beagleboard/beaglebone-ai/regulatory/FCC_ID/CTL1906244051-WF02 FCC 15.247  BT4.0.pdf

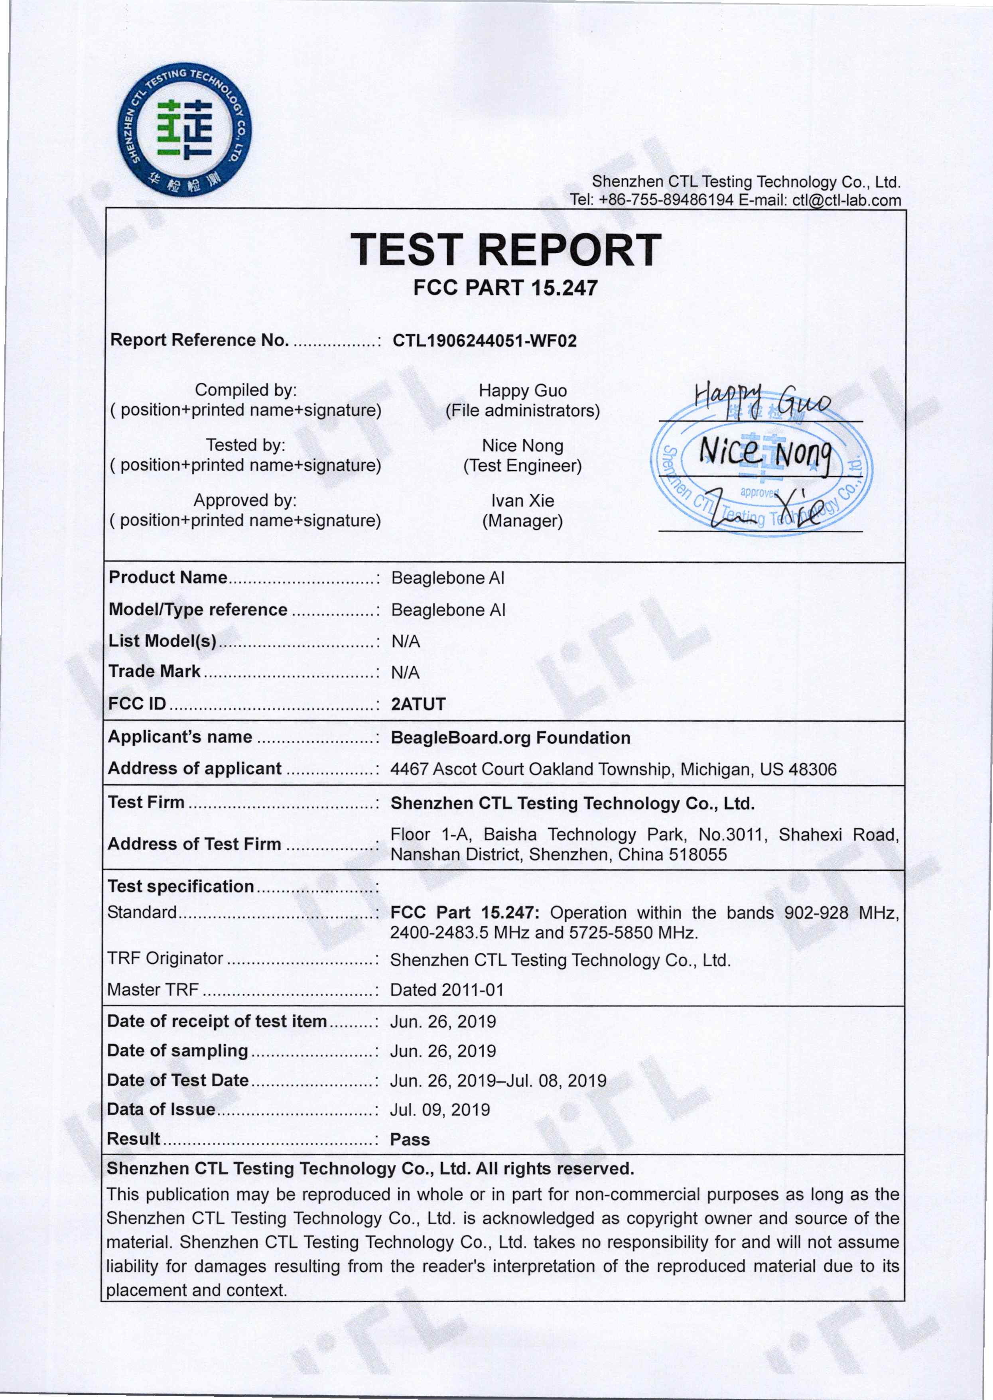
[picture p64: page 1]

V1.0 | Page 2 of 30 | Report No.: CTL1906244051-WF02

# TEST REPORT

Test Report No. : | CTL1906244051-WF02 | Jul. 09, 2019
Date of issue
Equipment under Test | : | Beaglebone AI
Model /Type | : | Beaglebone AI
Listed Models | : | N/A
Applicant | : | BeagleBoard.org Foundation
Address | : | 4467 Ascot Court Oakland Township, Michigan, US
48306
Manufacturer | : | BeagleBoard.org Foundation
Address | : | 4467 Ascot Court Oakland Township, Michigan, US
48306
Test result | Pass *

* In the configuration tested, the EUT complied with the standards specified page 5.
The test results presented in this report relate only to the object tested.
This report shall not be reproduced, except in full, without the written approval of the issuing testing laboratory.

V1.0 | Page 3 of 30 | Report No.: CTL1906244051-WF02

### ** Modified History **

Revisions | Description | Issued Data | Report No. | Remark
Version 1.0 | Initial Test Report Release | 2019-07-09 | CTL1906244051-WF02 | Tracy Qi

V1.0 | Page 4 of 30 | Report No.: CTL1906244051-WF02
| Table of Contents | Page

V1.0 | Page 5 of 30 | Report No.: CTL1906244051-WF02

## 1. SUMMARY

### 1.1. TEST STANDARDS

The tests were performed according to following standards:
FCC Rules Part 15.247: Frequency Hopping, Direct Spread Spectrum and Hybrid Systems that are in operation within the bands of 902-928 MHz, 2400-2483.5 MHz, and 5725-5850 MHz
ANSI C63.10: 2013: American National Standard for Testing Unlicensed Wireless Devices
KDB558074 D01 15.247 Meas Guidance v05r02: Guidance for Performing Compliance Measurements on Digital Transmission Systems (DTS) Operating Under §15.247

### 1.2. Test Description

FCC PART 15.247
FCC Part 15.207 | AC Power Conducted Emission | N/A
FCC Part 15.247(a)(2) | 6dB Bandwidth | PASS
FCC Part 15.247(d) | Spurious RF Conducted Emission | PASS
FCC Part 15.247(b) | Maximum Conducted Output Power | PASS
FCC Part 15.247(e) | Power Spectral Density | PASS
FCC Part 15.109/ 15.205/ 15.209 | Radiated Emissions | PASS
FCC Part 15.247(d) | Band Edge | PASS
FCC Part 15.203/15.247 (b) | Antenna Requirement | PASS

V1.0 | Page 6 of 30 | Report No.: CTL1906244051-WF02

### 1.3. Test Facility

### 1.3.1 Address of the test laboratory

Shenzhen CTL Testing Technology Co., Ltd.
Floor 1-A, Baisha Technology Park, No. 3011, Shahexi Road, Nanshan, Shenzhen 518055 China

There is one 3m semi-anechoic chamber and two line conducted labs for final test. The Test Sites meet the requirements in documents ANSI C63.4 and CISPR 32/EN 55032 requirements.

### 1.3.2 Laboratory accreditation

The test facility is recognized, certified, or accredited by the following organizations:
CNAS-Lab Code: L7497
Shenzhen CTL Testing Technology Co., Ltd. has been assessed and proved to be in compliance with CNAS-CL01 Accreditation Criteria for Testing and Calibration Laboratories (identical to ISO/IEC 17025: 2005 General Requirements) for the Competence of Testing and Calibration Laboratories.
A2LA-Lab Cert. No. 4343.01
Shenzhen CTL Testing Technology Co., Ltd. EMC Laboratory has been accredited by A2LA for technical competence in the field of electrical testing, and proved to be in compliance with ISO/IEC 17025: 2005 General Requirements for the Competence of Testing and Calibration Laboratories and any additional program requirements in the identified field of testing.
IC Registration No.: 9518B
CAB identifier: CN0041
The 3m alternate test site of Shenzhen CTL Testing Technology Co., Ltd. EMC Laboratory has been registered by Innovation, Science and Economic Development Canada to test to Canadian radio equipment requirements with Registration No.: 9518B on Jan. 22, 2019.
FCC-Registration No.: 399832
Designation No.: CN1216
Shenzhen CTL Testing Technology Co., Ltd. EMC Laboratory has been registered and fully described in a report filed with the (FCC) Federal Communications Commission. The acceptance letter from the FCC is maintained in our files. Registration 399832, December 08, 2017.

### 1.4. Statement of the measurement uncertainty

The data and results referenced in this document are true and accurate. The reader is cautioned that there may be errors within the calibration limits of the equipment and facilities. The measurement uncertainty was calculated for all measurements listed in this test report acc. to CISPR 16 - 4 “Specification for radio disturbance and immunity measuring apparatus and methods – Part 4: Uncertainty in EMC Measurements“ and is documented in the Shenzhen CTL Testing Technology Co., Ltd. quality system acc. to DIN EN ISO/IEC 17025. Furthermore, component and process variability of devices similar to that tested may result in additional deviation. The manufacturer has the sole responsibility of continued compliance of the device.

Hereafter the best measurement capability for CTL laboratory is reported:
Test | Measurement Uncertainty | Notes
Transmitter power conducted | ±0.57 dB | (1)
Transmitter power Radiated | ±2.20 dB | (1)
Conducted spurious emission 9KHz-40 GHz | ±2.20 dB | (1)
Occupied Bandwidth | ±0.01ppm | (1)
Radiated Emission 30~1000MHz | ±4.10dB | (1)
Radiated Emission Above 1GHz | ±4.32dB | (1)

V1.0 | Page 7 of 30 | Report No.: CTL1906244051-WF02
Conducted Disturbance0.15~30MHz | ±3.20dB | (1)
(1) This uncertainty represents an expanded uncertainty expressed at approximately the 95% confidence level using a coverage factor of k=2.

V1.0 | Page 8 of 30 | Report No.: CTL1906244051-WF02

## 2. GENERAL INFORMATION

### 2.1. Environmental conditions

During the measurement the environmental conditions were within the listed ranges:
Normal Temperature: | 25°C
Relative Humidity: | 55 %
Air Pressure: | 101 kPa

### 2.2. General Description of EUT

Product Name: | Beaglebone AI
Model/Type reference: | Beaglebone AI
Power supply: | DC 5.0V
Bluetooth LE
Supported type: | Bluetooth low Energy
Modulation: | GFSK
Operation frequency: | 2402MHz to 2480MHz
Channel number: | 40
Channel separation: | 2 MHz
Antenna type: | Snap antenna
Antenna gain: | 1.5dBi
Note: For more details, please refer to the user’s manual of the EUT.

### 2.3. Description of Test Modes and Test Frequency

The Applicant provides communication tools software to control the EUT for staying in continuous transmitting (Duty Cycle more than 98%) and receiving mode for testing.
There are 39 channels provided to the EUT and Channel 00/19/39 were selected for BLE test.

Operation Frequency List：
Channel | Frequency (MHz)
00 2402
02 | 2404
03 | 2406 ... ...
19 | 2440 ... ...
37 | 2476
38 | 2478
39 2480
Note: The line display in grey were the channel selected for testing

V1.0 | Page 9 of 30 | Report No.: CTL1906244051-WF02

### 2.4. Equipments Used during the Test

Test Equipment | Manufacturer | Model No. | Serial No. | Calibration Date | Calibration Due Date
LISN | R&S | ENV216 | 3560.6550.1 2 | 2019/05/24 | 2020/05/23
LISN | R&S | ESH2-Z5 | 860014/010 | 2019/05/24 | 2020/05/23
Bilog Antenna | Sunol Sciences Corp. | JB1 | A061713 | 2019/05/24 | 2020/05/23
EMI Test Receiver | R&S | ESCI | 1166.5950.03 | 2019/05/24 | 2020/05/23
Spectrum Analyzer | Agilent | E4407B | MY41440676 | 2019/05/24 | 2020/05/23
Spectrum Analyzer | Agilent | N9020 | US46220290 | 2019/05/24 | 2020/05/23
Controller | EM Electronics | EM 1000 | 060859 | 2019/05/24 | 2020/05/23
Horn Antenna | Sunol Sciences Corp. | DRH-118 | A062013 | 2019/05/24 | 2020/05/23
Active Loop Antenna | Da Ze | ZN30900A | / | 2019/05/24 | 2020/05/23
Amplifier | Agilent | 8449B | 3008A02306 | 2019/05/24 | 2020/05/23
Amplifier | Agilent | 8447D | 2944A10176 | 2019/05/24 | 2020/05/23
Temperature/Humi dity Meter | Gangxing | CTH-608 | 02 | 2019/05/24 | 2020/05/23
High-Pass Filter | micro-tranics | HPM50108 | G174 | 2019/05/24 | 2020/05/23
High-Pass Filter | micro-tranics | HPM50111 | G142 | 2019/05/24 | 2020/05/23
Coaxial Cables | HUBER+SUHN ER | SUCOFLEX 104PEA-10M | 10m | 2019/05/24 | 2020/05/23
Coaxial Cables | HUBER+SUHN ER | SUCOFLEX 104PEA-3M | 3m | 2019/05/24 | 2020/05/23
Coaxial Cables | HUBER+SUHN ER | SUCOFLEX 104PEA-3M | 3m | 2019/05/24 | 2020/05/23
RF Cable | Megalon | RF-A303 | N/A | 2019/05/24 | 2020/05/23
Power Sensor | Agilent | U2021XA | MY5365004 | 2019/05/24 | 2020/05/23
Power Meter | Agilent | U2531A | TW53323507 | 2019/05/24 | 2020/05/23
The calibration interval was one year

### 2.5. Related Submittal(s) / Grant (s)

This submittal(s) (test report) is intended to comply with Section 15.247 of the FCC Part 15, Subpart C Rules.

### 2.6. Modifications

No modifications were implemented to meet testing criteria.

V1.0 | Page 10 of 30 | Report No.: CTL1906244051-WF02

## 3. TEST CONDITIONS AND RESULTS

### 3.1. Conducted Emissions Test

LIMIT
FCC CFR Title 47 Part 15 Subpart C Section 15.207
Frequency range (MHz) | Limit (dBuV)
Quasi-peak | Average
0.15-0.5 | 66 to 56* | 56 to 46*
0.5-5 | 56 | 46
5-30 | 60 | 50

* Decreases with the logarithm of the frequency.

TEST CONFIGURATION

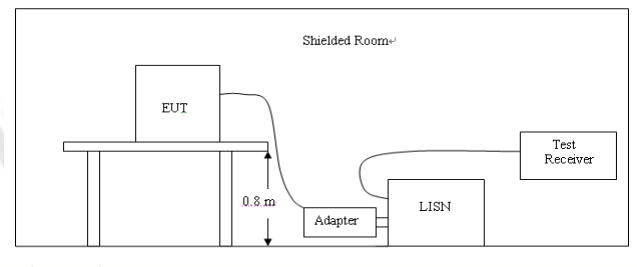
[picture p65: figure]

TEST PROCEDURE

1. The equipment was set up as per the test configuration to simulate typical actual usage per the user’s manual. The EUT is a tabletop system; a wooden table with a height of 0.8 meters is used and is placed on the ground plane as per ANSI C63.10:2013.
2. Support equipment, if needed, was placed as per ANSI C63.10:2013.
3. All I/O cables were positioned to simulate typical actual usage as per ANSI C63.10:2013.
4. The adapter received AC120V/60Hz power through a Line Impedance Stabilization Network (LISN) which supplied power source and was grounded to the ground plane.
5. All support equipments received AC power from a second LISN, if any.
6. The EUT test program was started. Emissions were measured on each current carrying line of the EUT using a spectrum Analyzer / Receiver connected to the LISN powering the EUT. The LISN has two monitoring points: Line 1 (Hot Side) and Line 2 (Neutral Side). Two scans were taken: one with Line 1 connected to Analyzer / Receiver and Line 2 connected to a 50 ohm load; the second scan had Line 1 connected to a 50 ohm load and Line 2 connected to the Analyzer / Receiver.
7. Analyzer / Receiver scanned from 150 KHz to 30MHz for emissions in each of the test modes.
8. During the above scans, the emissions were maximized by cable manipulation.

TEST RESULTS

Not applicable to this device, which is powered by battery.

V1.0 | Page 11 of 30 | Report No.: CTL1906244051-WF02

### 3.2. Radiated Emissions and Band Edge

Limit

For intentional device, according to § 15.209(a), the general requirement of field strength of radiated emission out of authorized band shall not exceed the following table at a 3 meters measurement distance.
In addition, radiated emissions which fall in the restricted bands, as defined in §15.205(a), must also comply with the radiated emission limits specified in §15.209(a)

Radiated emission limits
Frequency (MHz) | Distance (Meters) | Radiated (dBμV/m) | Radiated (μV/m)
0.009-0.49 | 3 | 20log(2400/F(KHz))+40log(300/3) | 2400/F(KHz)
0.49-1.705 | 3 | 20log(24000/F(KHz))+ 40log(30/3) | 24000/F(KHz)
1.705-30 | 3 | 20log(30)+ 40log(30/3) | 30
30-88 | 3 | 40.0 | 100
88-216 | 3 | 43.5 | 150
216-960 | 3 | 46.0 | 200
Above 960 | 3 | 54.0 | 500

TEST CONFIGURATION
(A) Radiated Emission Test Set-Up, Frequency Below 30MHz

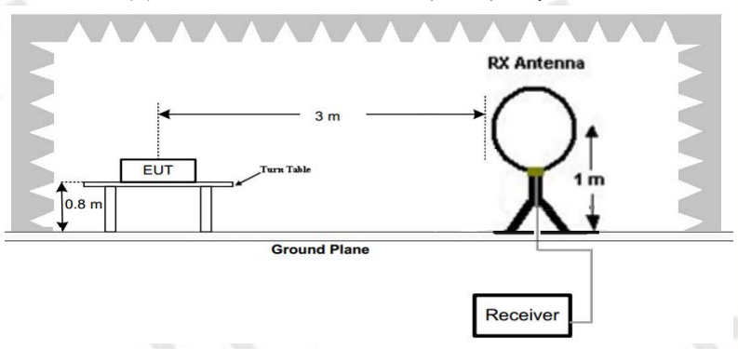
[picture p66: figure]

(B) Radiated Emission Test Set-Up, Frequency below 1000MHz

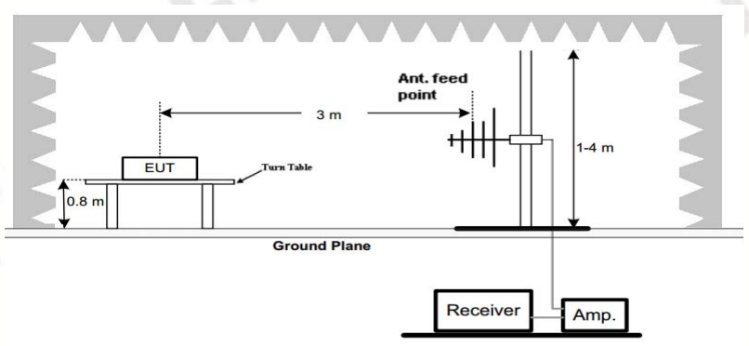
[picture p67: figure]

(C) Radiated Emission Test Set-Up, Frequency above 1000MHz

V1.0 | Page 12 of 30 | Report No.: CTL1906244051-WF02

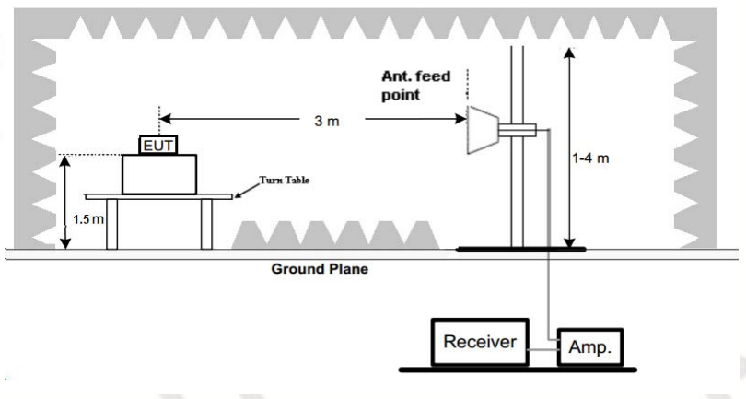
[picture p68: figure]

Test Procedure

1. Below 1GHz measurement the EUT is placed on a turntable which is 0.8m above ground plane, and above 1GHz measurement EUT was placed on a low permittivity and low loss tangent turn table which is 1.5m above ground plane.
2. Maximum procedure was performed by raising the receiving antenna from 1m to 4m and rotating the turn table from 0℃ to 360℃ to acquire the highest emissions from EUT
3. And also, each emission was to be maximized by changing the polarization of receiving antenna both horizontal and vertical.
4. Repeat above procedures until all frequency measurements have been completed.

TEST RESULTS
Remark:
1. For below 1GHz testing recorded worst at BLE low channel.
2. Radiated emission test from 9 KHz to 10th harmonic of fundamental was verified, and no emission found except system noise floor in 9 KHz to 30MHz and not recorded in this report.

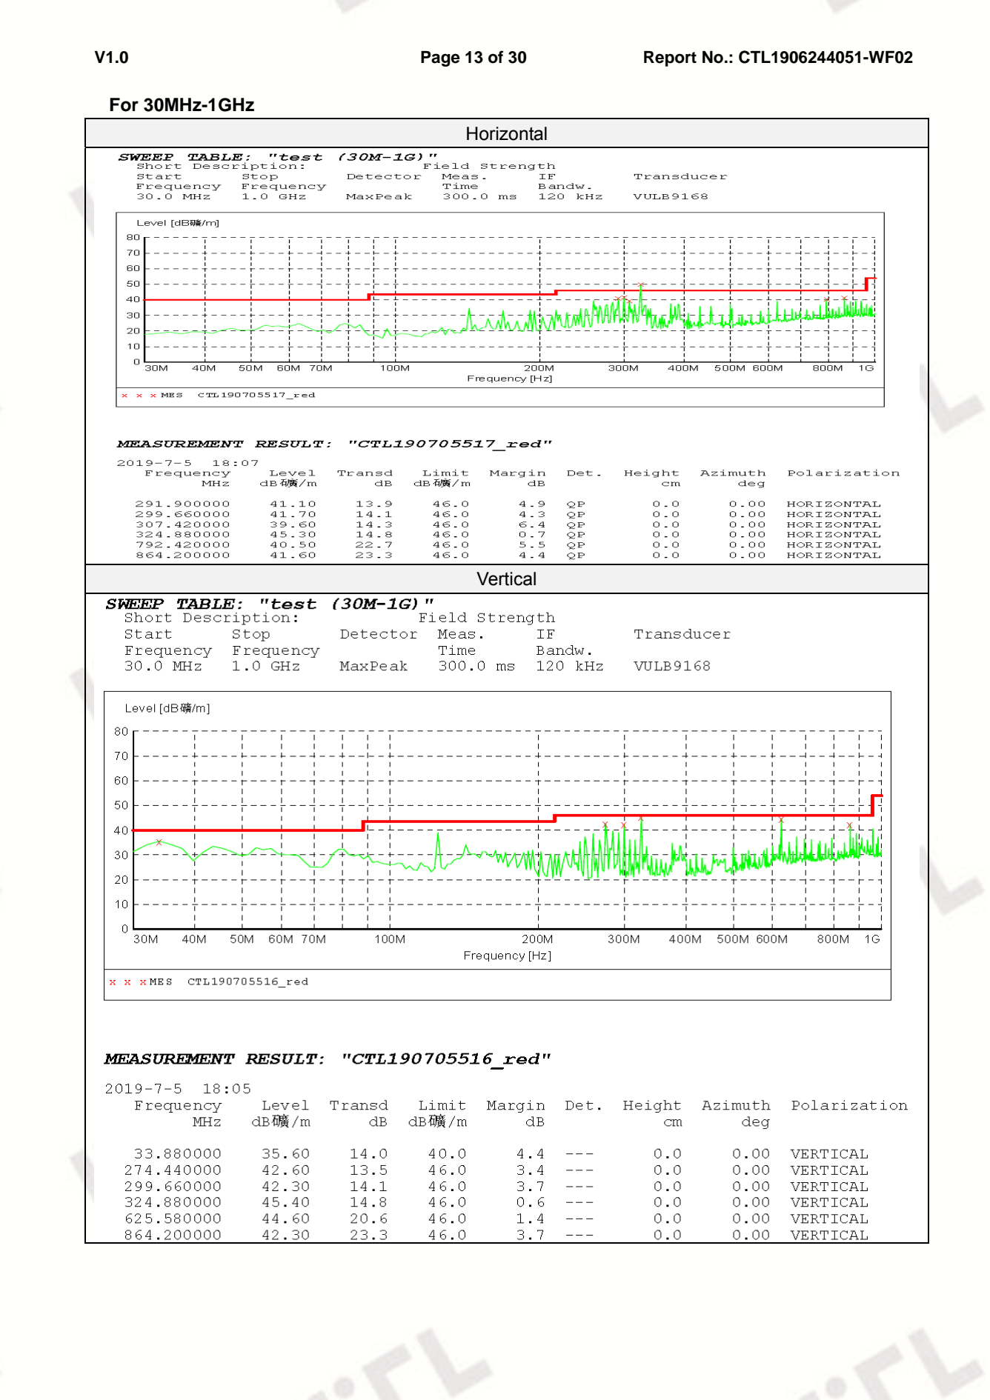
[picture p69: page 13]

V1.0 | Page 13 of 30 | Report No.: CTL1906244051-WF02

For 30MHz-1GHz
Horizontal

Vertical

V1.0 | Page 14 of 30 | Report No.: CTL1906244051-WF02

For 1GHz to 25GHz
BLE Mode (above 1GHz)
Frequency(MHz): | 2402 | Polarity: | HORIZONTAL
Frequency (MHz) | Emission Level (dBuV/m) | Limit (dBuV/m) | Margin (dB) | Raw Value (dBuV) | Antenna Factor (dB/m) | Cable Factor (dB) | Pre-amplifier (dB) | Correction Factor (dB/m)
4804.00 | 51.16 | PK | 74.00 | 22.84 | 46.65 | 33.49 | 6.91 | 35.89 | 4.51
4804.00 | -- | AV | 54.00 | -- | -- | -- | -- | -- | --
5120.05 | 46.15 | PK | 74.00 | 27.85 | 38.94 | 34.38 | 7.10 | 34.27 | 7.21
5120.05 | -- | AV | 54.00 | -- | -- | -- | -- | -- | --
7206.00 | 46.29 | PK | 74.00 | 27.71 | 35.19 | 36.95 | 9.18 | 35.03 | 11.10
7206.00 | -- | AV | 54.00 | -- | -- | -- | -- | -- | --
Frequency(MHz): | 2402 | Polarity: | VERTICAL
Frequency (MHz) | Emission Level (dBuV/m) | Limit (dBuV/m) | Margin (dB) | Raw Value (dBuV) | Antenna Factor (dB/m) | Cable Factor (dB) | Pre-amplifier (dB) | Correction Factor (dB/m)
4804.00 | 49.16 | PK | 74.00 | 24.84 | 44.65 | 33.49 | 6.91 | 35.89 | 4.51
4804.00 | -- | AV | 54.00 | -- | -- | -- | -- | -- | --
5120.05 | 47.01 | PK | 74.00 | 26.99 | 39.45 | 34.69 | 7.23 | 34.36 | 7.56
5120.05 | -- | AV | 54.00 | -- | -- | -- | -- | -- | --
7206.00 | 45.86 | PK | 74.00 | 28.14 | 34.76 | 36.95 | 9.18 | 35.03 | 11.10
7206.00 | -- | AV | 54.00 | -- | -- | -- | -- | -- | --
Frequency(MHz): | 2440 | Polarity: | HORIZONTAL
Frequency (MHz) | Emission Level (dBuV/m) | Limit (dBuV/m) | Margin (dB) | Raw Value (dBuV) | Antenna Factor (dB/m) | Cable Factor (dB) | Pre-amplifier (dB) | Correction Factor (dB/m)
4880.00 | 47.03 | PK | 74.00 | 26.97 | 40.78 | 33.60 | 6.95 | 34.30 | 6.25
4880.00 | -- | AV | 54.00 | -- | -- | -- | -- | -- | --
5235.15 | 43.86 | PK | 74.00 | 30.14 | 36.23 | 34.57 | 7.16 | 34.10 | 7.63
5235.15 | -- | AV | 54.00 | -- | -- | -- | -- | -- | --
7320.00 | 45.18 | PK | 74.00 | 28.82 | 33.49 | 37.46 | 9.23 | 35.00 | 11.69
7320.00 | -- | AV | 54.00 | -- | -- | -- | -- | -- | --
Frequency(MHz): | 2440 | Polarity: | VERTICAL
Frequency (MHz) | Emission Level (dBuV/m) | Limit (dBuV/m) | Margin (dB) | Raw Value (dBuV) | Antenna Factor (dB/m) | Cable Factor (dB) | Pre-amplifier (dB) | Correction Factor (dB/m)
4880.00 | 48.25 | PK | 74.00 | 25.75 | 42.00 | 33.60 | 6.95 | 34.30 | 6.25
4880.00 | -- | AV | 54.00 | -- | -- | -- | -- | -- | --
5235.15 | 42.58 | PK | 74.00 | 31.42 | 34.94 | 34.58 | 7.16 | 34.10 | 7.64
5235.15 | -- | AV | 54.00 | -- | -- | -- | -- | -- | --
7320.00 | 46.31 | PK | 74.00 | 27.69 | 34.62 | 37.46 | 9.23 | 35.00 | 11.69
7320.00 | -- | AV | 54.00 | -- | -- | -- | -- | -- | --

V1.0 | Page 15 of 30 | Report No.: CTL1906244051-WF02
Frequency(MHz): | 2480 | Polarity: | HORIZONTAL
Frequency (MHz) | Emission Level (dBuV/m) | Limit (dBuV/m) | Margin (dB) | Raw Value (dBuV) | Antenna Factor (dB/m) | Cable Factor (dB) | Pre-amplifier (dB) | Correction Factor (dB/m)
4960.00 | 48.69 | PK | 74.00 | 25.31 | 43.77 | 33.84 | 7.00 | 35.92 | 4.92
4960.00 | -- | AV | 54.00 | -- | -- | -- | -- | -- | --
5325.05 | 44.56 | PK | 74.00 | 29.44 | 37.02 | 34.67 | 7.22 | 34.35 | 7.54
5325.05 | -- | AV | 54.00 | -- | -- | -- | -- | -- | --
7440.00 | 45.83 | PK | 74.00 | 28.17 | 33.88 | 37.64 | 9.28 | 34.97 | 11.95
7440.00 | -- | AV | 54.00 | -- | -- | -- | -- | -- | --
Frequency(MHz): | 2480 | Polarity: | VERTICAL
Frequency (MHz) | Emission Level (dBuV/m) | Limit (dBuV/m) | Margin (dB) | Raw Value (dBuV) | Antenna Factor (dB/m) | Cable Factor (dB) | Pre-amplifier (dB) | Correction Factor (dB/m)
4960.00 | 47.68 | PK | 74.00 | 26.32 | 42.76 | 33.84 | 7.00 | 35.92 | 4.92
4960.00 | -- | AV | 54.00 | -- | -- | -- | -- | -- | --
5325.05 | 43.51 | PK | 74.00 | 30.49 | 36.32 | 34.36 | 7.10 | 34.27 | 7.19
5325.05 | -- | AV | 54.00 | -- | -- | -- | -- | -- | --
7440.00 | 44.32 | PK | 74.00 | 29.68 | 32.37 | 37.64 | 9.28 | 34.97 | 11.95
7440.00 | -- | AV | 54.00 | -- | -- | -- | -- | -- | --

REMARKS:
1. Emission level (dBuV/m) =Raw Value (dBuV)+Correction Factor (dB/m)
2. Correction Factor (dB/m) = Antenna Factor (dB/m)+Cable Factor (dB)-Pre-amplifier Factor
3. Margin value = Limit value- Emission level.
4. -- Mean the PK detector measured value is below average limit.
5. The other emission levels were very low against the limit.
6. RBW1MHz VBW3MHz Peak detector is for PK value; RBW 1MHz VBW10Hz Peak detector is for AV value.

V1.0 | Page 16 of 30 | Report No.: CTL1906244051-WF02

Results of Band Edges Test (Radiated)
Frequency(MHz): | 2402 | Polarity: | HORIZONTAL
Frequency (MHz) | Emission Level (dBuV/m) | Limit (dBuV/m) | Margin (dB) | Raw Value (dBuV) | Antenna Factor (dB/m) | Cable Factor (dB) | Pre-amplifier (dB) | Correction Factor (dB/m)
2402.00 | 94.93 | PK | -- | -- | 61.54 | 28.78 | 4.61 | 0.00 | 33.39
2402.00 | 90.48 | AV | -- | -- | 57.09 | 28.78 | 4.61 | 0.00 | 33.39
2357.75 | 44.81 | PK | 74.00 | 29.19 | 11.73 | 28.52 | 4.56 | 0.00 | 33.08
2357.75 | -- | AV | 54.00 | -- | -- | -- | -- | -- | --
2390.00 | 45.20 | PK | 74.00 | 28.80 | 11.88 | 28.72 | 4.60 | 0.00 | 33.32
2390.00 | -- | AV | 54.00 | -- | -- | -- | -- | -- | --
2400.00 | 47.85 | PK | 74.00 | 26.15 | 14.46 | 28.78 | 4.61 | 0.00 | 33.39
2400.00 | -- | AV | 54.00 | -- | -- | -- | -- | -- | --
Frequency(MHz): | 2402 | Polarity: | VERTICAL
Frequency (MHz) | Emission Level (dBuV/m) | Limit (dBuV/m) | Margin (dB) | Raw Value (dBuV) | Antenna Factor (dB/m) | Cable Factor (dB) | Pre-amplifier (dB) | Correction Factor (dB/m)
2402.00 | 94.71 | PK | -- | -- | 61.32 | 28.78 | 4.61 | 0 | 33.39
2402.00 | 89.22 | AV | -- | -- | 55.83 | 28.78 | 4.61 | 0 | 33.39
2357.75 | 45.07 | PK | 74 | 28.93 | 11.99 | 28.52 | 4.56 | 0 | 33.08
2357.75 | -- | AV | 54 | -- | -- | -- | -- | -- | --
2390.00 | 46.18 | PK | 74 | 27.82 | 12.86 | 28.72 | 4.60 | 0 | 33.32
2390.00 | -- | AV | 54 | -- | -- | -- | -- | -- | --
2400.00 | 48.26 | PK | 74 | 25.74 | 14.87 | 28.78 | 4.61 | 0 | 33.39
2400.00 | -- | AV | 54 | -- | -- | -- | -- | -- | --
Frequency(MHz): | 2480 | Polarity: | HORIZONTAL
Frequency (MHz) | Emission Level (dBuV/m) | Limit (dBuV/m) | Margin (dB) | Raw Value (dBuV) | Antenna Factor (dB/m) | Cable Factor (dB) | Pre-amplifier (dB) | Correction Factor (dB/m)
2480.00 | 95.11 | PK | -- | -- | 61.49 | 28.92 | 4.70 | 0.00 | 33.62
2480.00 | 90.35 | AV | -- | -- | 56.73 | 28.92 | 4.70 | 0.00 | 33.62
2483.50 | 43.12 | PK | 74 | 30.88 | 9.49 | 28.93 | 4.70 | 0.00 | 33.63
2483.50 | -- | AV | 54 | -- | -- | -- | -- | -- | --
2491.95 | 43.26 | PK | 74 | 30.74 | 9.6 | 28.95 | 4.71 | 0.00 | 33.66
2491.95 | -- | AV | 54 | -- | -- | -- | -- | -- | --
2500.00 | 47.42 | PK | 74 | 26.58 | 13.74 | 28.96 | 4.72 | 0.00 | 33.68
2500.00 | -- | AV | 54 | -- | -- | -- | -- | -- | --
Frequency(MHz): | 2480 | Polarity: | VERTICAL
Frequency (MHz) | Emission Level (dBuV/m) | Limit (dBuV/m) | Margin (dB) | Raw Value (dBuV) | Antenna Factor (dB/m) | Cable Factor (dB) | Pre-amplifier (dB) | Correction Factor (dB/m)
2480.00 | 93.87 | PK | -- | -- | 60.25 | 28.92 | 4.70 | 0.00 | 33.62
2480.00 | 89.04 | AV | -- | -- | 55.42 | 28.92 | 4.70 | 0.00 | 33.62
2483.50 | 43.06 | PK | 74 | 30.94 | 9.43 | 28.93 | 4.70 | 0.00 | 33.63
2483.50 | -- | AV | 54 | -- | -- | -- | -- | -- | --
2489.05 | 42.71 | PK | 74 | 31.29 | 9.05 | 28.95 | 4.71 | 0.00 | 33.66
2489.05 | -- | AV | 54 | -- | -- | -- | -- | -- | --
2500.00 | 45.25 | PK | 74 | 28.75 | 11.57 | 28.96 | 4.72 | 0.00 | 33.68
2500.00 | -- | AV | 54 | -- | -- | -- | -- | -- | --

V1.0 | Page 17 of 30 | Report No.: CTL1906244051-WF02

REMARKS:
1. Emission level (dBuV/m) =Raw Value (dBuV)+Correction Factor (dB/m)
2. Correction Factor (dB/m) = Antenna Factor (dB/m)+Cable Factor (dB)-Pre-amplifier Factor
3. Margin value = Limit value- Emission level.
4. -- Mean the PK detector measured value is below average limit.
5. The other emission levels were very low against the limit.
6. RBW1MHz VBW3MHz Peak detector is for PK value; RBW 1MHz VBW10Hz Peak detector is for AV value.
7. For fundamental frequency, RBW 3MHz VBW 3MHz Peak detector is for PK Value; RMS detector is for AV value.

V1.0 | Page 18 of 30 | Report No.: CTL1906244051-WF02

### 3.3. Maximum Conducted Output Power

Limit

The Maximum Peak Output Power Measurement is 30dBm.

Test Procedure

Remove the antenna from the EUT and then connect a low loss RF cable from the antenna port to the power sensor.

Test Configuration

EUT

| Power Sensor | Power Meter

Test Results

Type | Channel | Output power (dBm) | Limit (dBm) | Result
GFSK | 00 | 1.562 | 30.00 | Pass
| 19 | 2.191
| 39 | 0.833
Note: 1.The test results including the cable lose.

V1.0 | Page 19 of 30 | Report No.: CTL1906244051-WF02

### 3.4. Power Spectral Density

Limit

For digitally modulated systems, the power spectral density conducted from the intentional radiator to the antenna shall not be greater than 8 dBm in any 3 kHz band during any time interval of continuous transmission.
Test Procedure
1. Use this procedure when the maximum peak conducted output power in the fundamental emission is used to demonstrate compliance.
2. Set the RBW ≥ 3 kHz.
3. Set the VBW ≥ 3× RBW.
4. Set the span to 1.5 times the DTS channel bandwidth.
5. Detector = peak.
6. Sweep time = auto couple.
7. Trace mode = max hold.
8. Allow trace to fully stabilize.
9. Use the peak marker function to determine the maximum power level.
10. If measured value exceeds limit, reduce RBW (no less than 3 kHz) and repeat.
11. The resulting peak PSD level must be 8dBm.
Test Configuration

EUT

SPECTRUM
ANALYZER

Test Results

Type | Channel | Power Spectral Density (dBm/3KHz) | Limit (dBm/3KHz) | Result
GFSK | 00 | -12.853 | 8.00 | Pass
| 19 | -12.157
| 39 | -13.513

Test plot as follows:

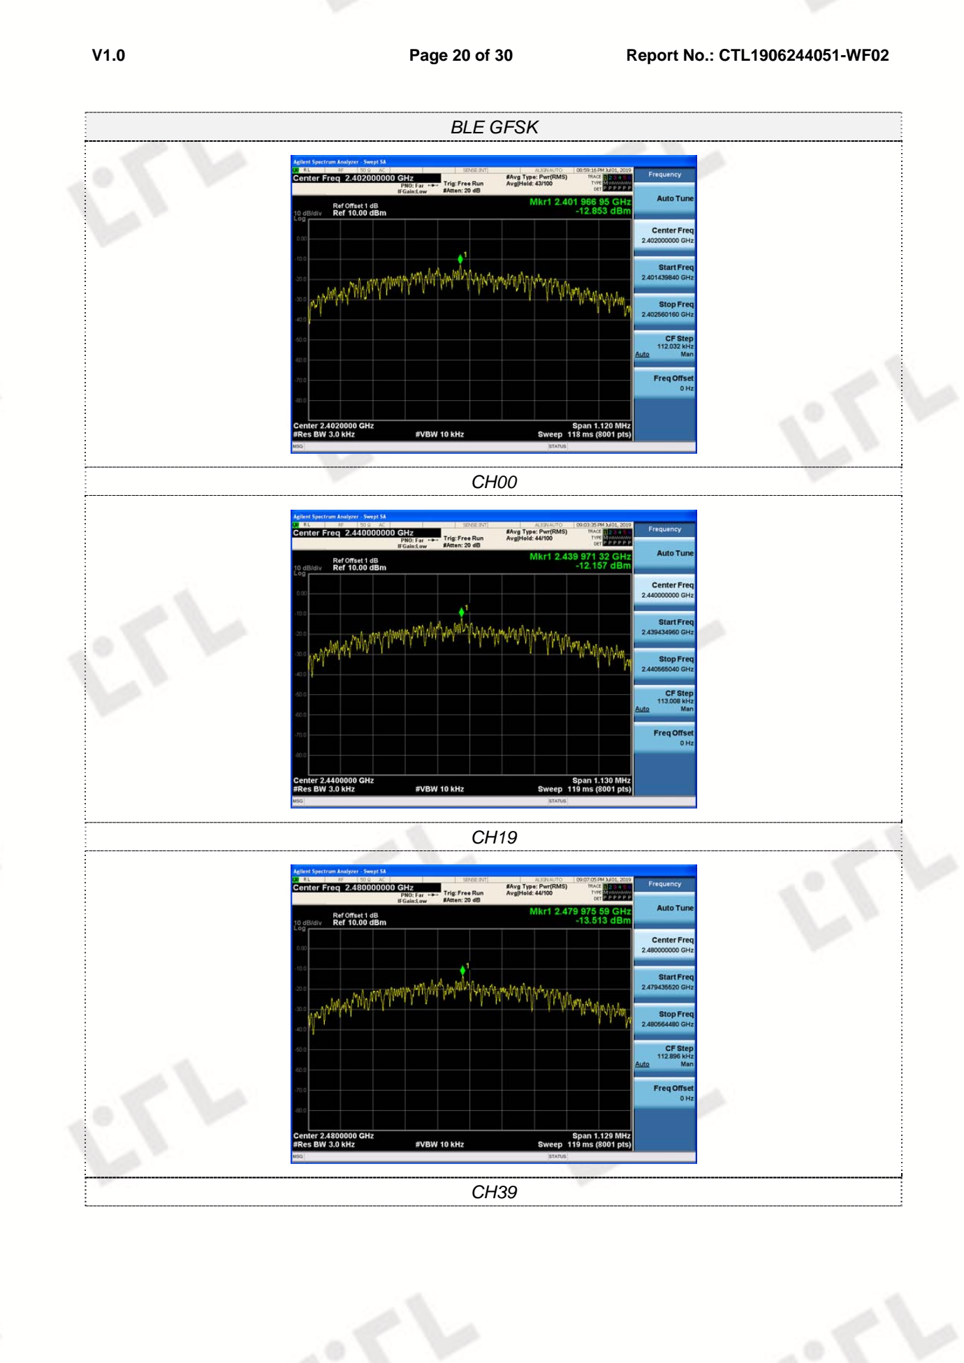
[picture p70: page 20]

V1.0 | Page 20 of 30 | Report No.: CTL1906244051-WF02

BLE GFSK

CH00

CH19

CH39

V1.0 | Page 21 of 30 | Report No.: CTL1906244051-WF02

### 3.5. 6dB Bandwidth

Limit

For digital modulation systems, the minimum 6 dB bandwidth shall be at least 500 kHz

Test Procedure

The transmitter output was connected to the spectrum analyzer through an attenuator. The bandwidth of the fundamental frequency was measured by spectrum analyzer with 100 KHz RBW and 300 KHz VBW. The 6dB bandwidth is defined as the total spectrum the power of which is higher than peak power minus 6dB.

Test Configuration

EUT

SPECTRUM
ANALYZER

Test Results

Type | Channel | 6dB Bandwidth (MHz) | 99% OBW (MHz) | Limit (KHz) | Result
GFSK | 00 | 0.7002 | 1.0842 | ≥500 | Pass
| 19 | 0.7063 | 1.0866
| 39 | 0.7056 | 1.0842

Test plot as follows:

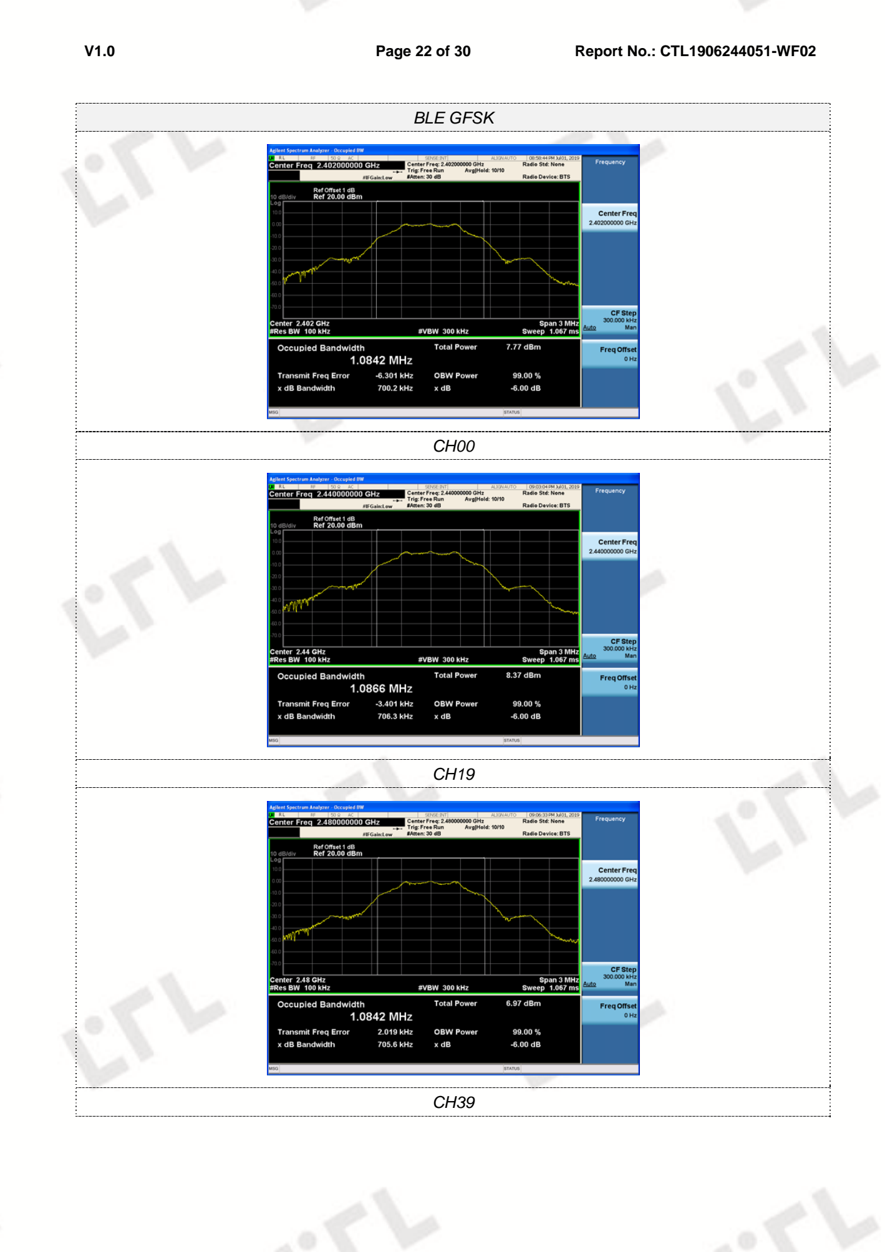
[picture p71: page 22]

V1.0 | Page 22 of 30 | Report No.: CTL1906244051-WF02

BLE GFSK

CH00

CH19

CH39

V1.0 | Page 23 of 30 | Report No.: CTL1906244051-WF02

### 3.6. Out-of-band Emissions

Limit
In any 100 kHz bandwidth outside the frequency band in which the spread spectrum or digitally modulated intentional radiator is operating, the radio frequency power that is produced by the intentional radiator shall be at least 20 dB below that in the 100 kHz bandwidth within the band that contains the highest level of the desired power, based on either an RF con-ducted or a radiated measurement, pro-vided the transmitter demonstrates compliance with the peak conducted power limits. If the transmitter com-plies with the conducted power limits based on the use of RMS averaging over a time interval, as permitted under paragraph (b)(3) of this section, the attenuation required under this paragraph shall be 30 dB instead of 20 dB. Attenuation below the general limits specified in §15.209(a) is not required.

Test Procedure

Connect the transmitter output to spectrum analyzer using a low loss RF cable, and set the spectrum analyzer to RBW=100 kHz, VBW= 300 kHz, peak detector , and max hold. Measurements utilizing these setting are made of the in-band reference level, bandedge and out-of-band emissions.

Test Configuration

EUT

SPECTRUM
ANALYZER

Test Results

Remark: The measurement frequency range is from 30MHz to the 10th harmonic of the fundamental frequency. The lowest, middle and highest channels are tested to verify the spurious emissions and bandage measurement data.

Test plot as follows:

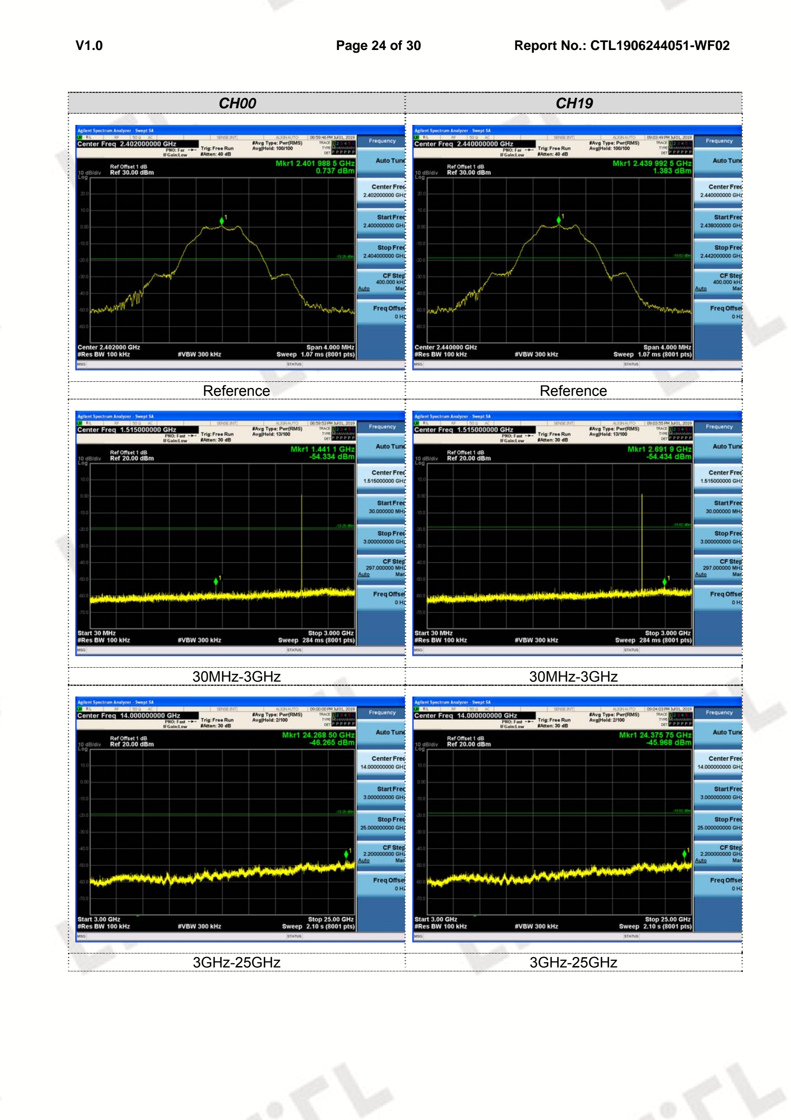
[picture p72: page 24]

V1.0 | Page 24 of 30 | Report No.: CTL1906244051-WF02
CH00 | CH19
Reference | Reference
30MHz-3GHz | 30MHz-3GHz
3GHz-25GHz | 3GHz-25GHz

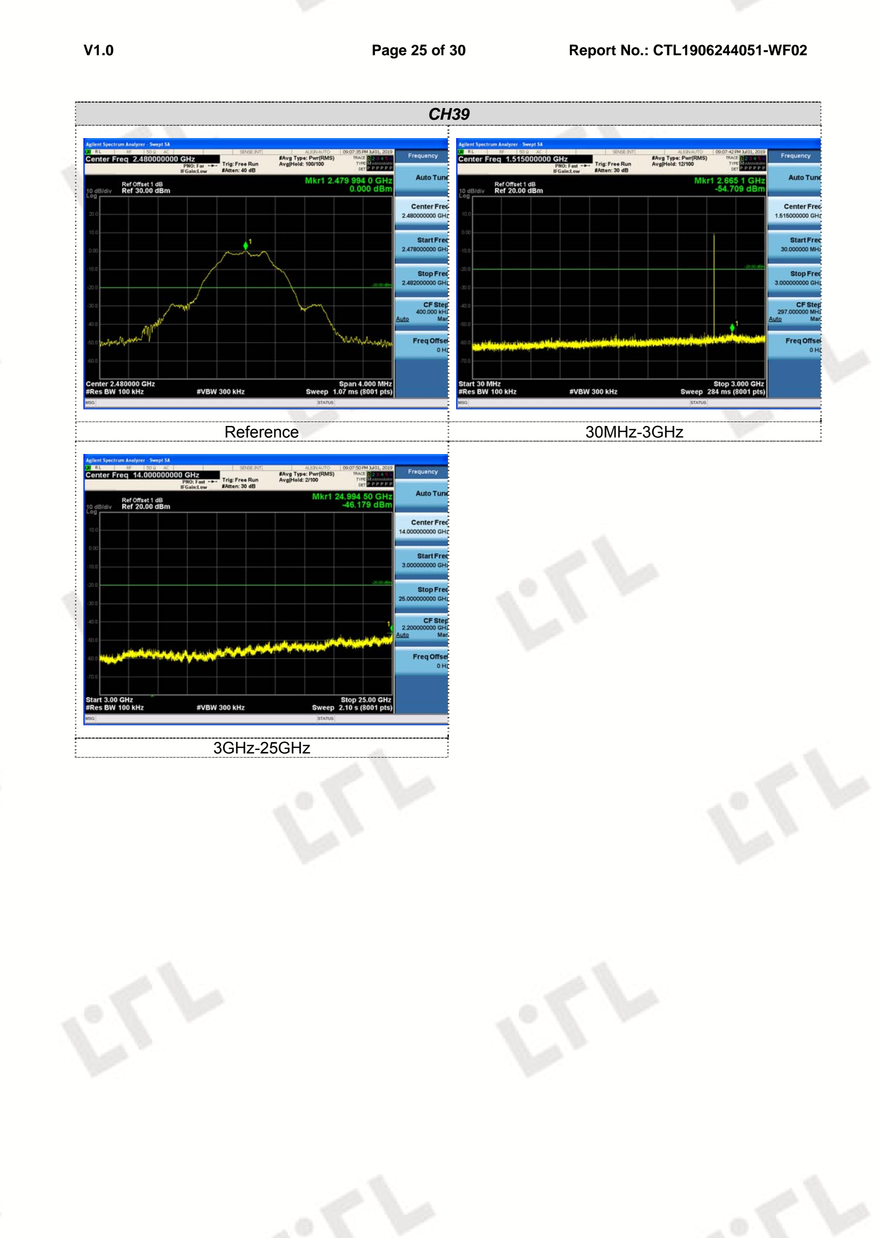
[picture p73: page 25]

V1.0 | Page 25 of 30 | Report No.: CTL1906244051-WF02

CH39

Reference | 30MHz-3GHz

3GHz-25GHz

V1.0 | Page 26 of 30 | Report No.: CTL1906244051-WF02

Band-edge Measurements for RF Conducted Emissions:

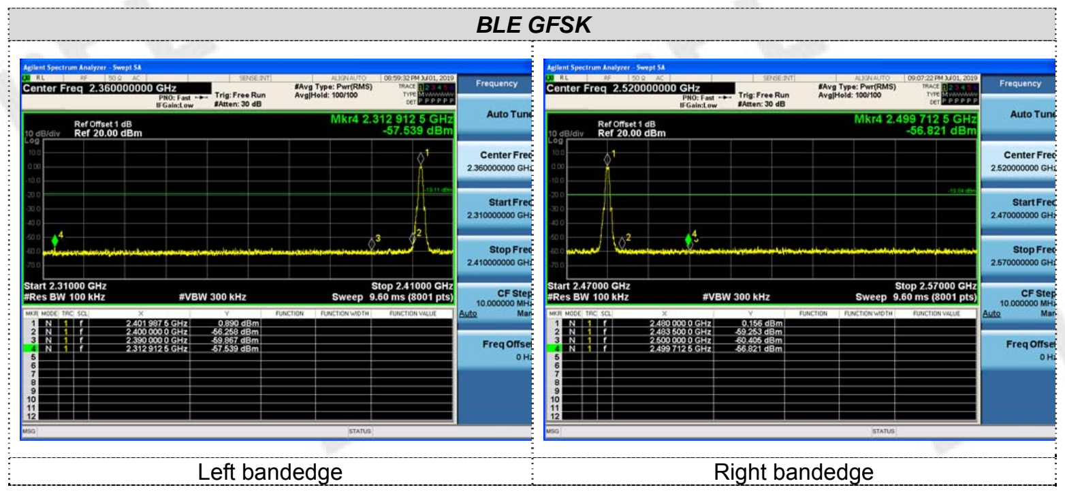
[picture p74: figure]
BLE GFSK; Left bandedge; Right bandedge

V1.0 | Page 27 of 30 | Report No.: CTL1906244051-WF02

### 3.7. Antenna Requirement

Standard Applicable

For intentional device, according to FCC 47 CFR Section 15.203:

An intentional radiator shall be designed to ensure that no antenna other than that furnished by the responsible party shall be used with the device. The use of a permanently attached antenna or of an antenna that uses a unique coupling to the intentional radiator, the manufacturer may design the unit so that a broken antenna can be replaced by the user, but the use of a standard antenna jack or electrical connector is prohibited

FCC CFR Title 47 Part 15 Subpart C Section 15.247(c) (1) (I):

(i) Systems operating in the 2400-2483.5 MHz band that is used exclusively for fixed. Point-to-point operations may employ transmitting antennas with directional gain greater than 6dBi provided the maximum conducted output power of the intentional radiator is reduced by 1 dB for every 3 dB that the directional gain of the antenna exceeds 6dBi.

Test Result:
The maximum gain of antenna was 1.5dBi.

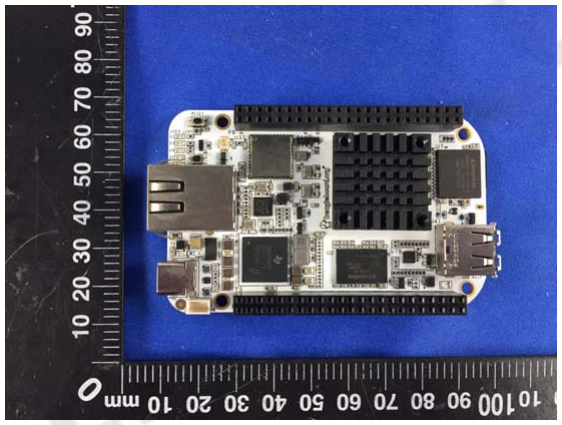
[picture p75: figure]

## 4. Test Setup Photos of the EUT

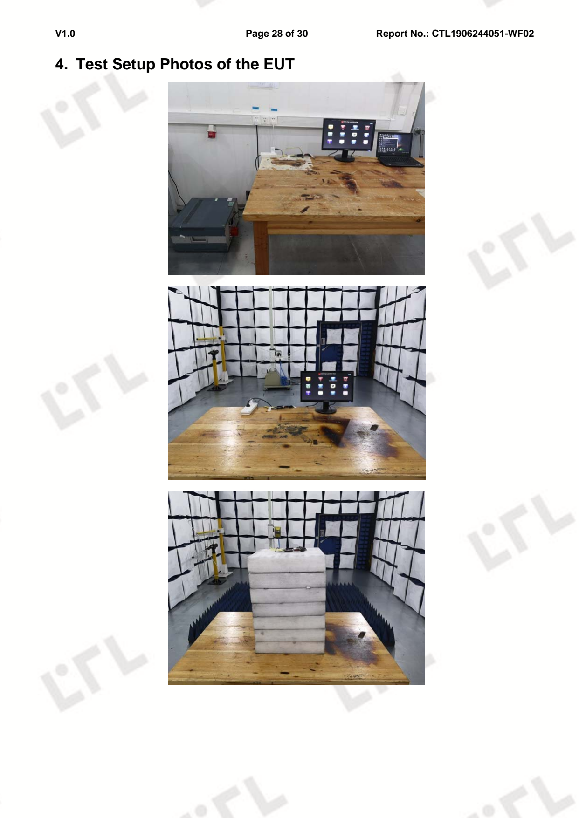
[picture p76: page 28]

V1.0 | Page 28 of 30 | Report No.: CTL1906244051-WF02

## 5. Photos of the EUT

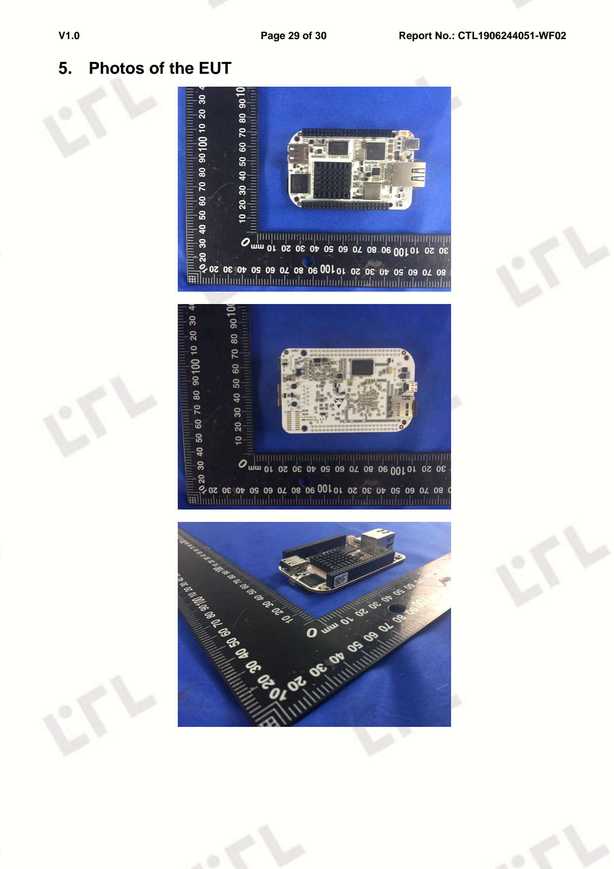
[picture p77: page 29]

V1.0 | Page 29 of 30 | Report No.: CTL1906244051-WF02

V1.0 | Page 30 of 30 | Report No.: CTL1906244051-WF02

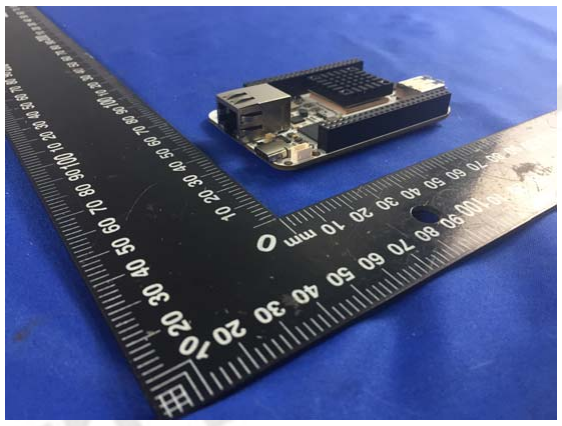
[picture p78: figure]

********************** End of Report **********************
