beagleboard/beaglebone-ai/kicad/beaglebone-ai-rev-a1/adc.kicad_sch

## KiCad design kicad/beaglebone-ai-rev-a1/adc.kicad_sch (2021-06-15)

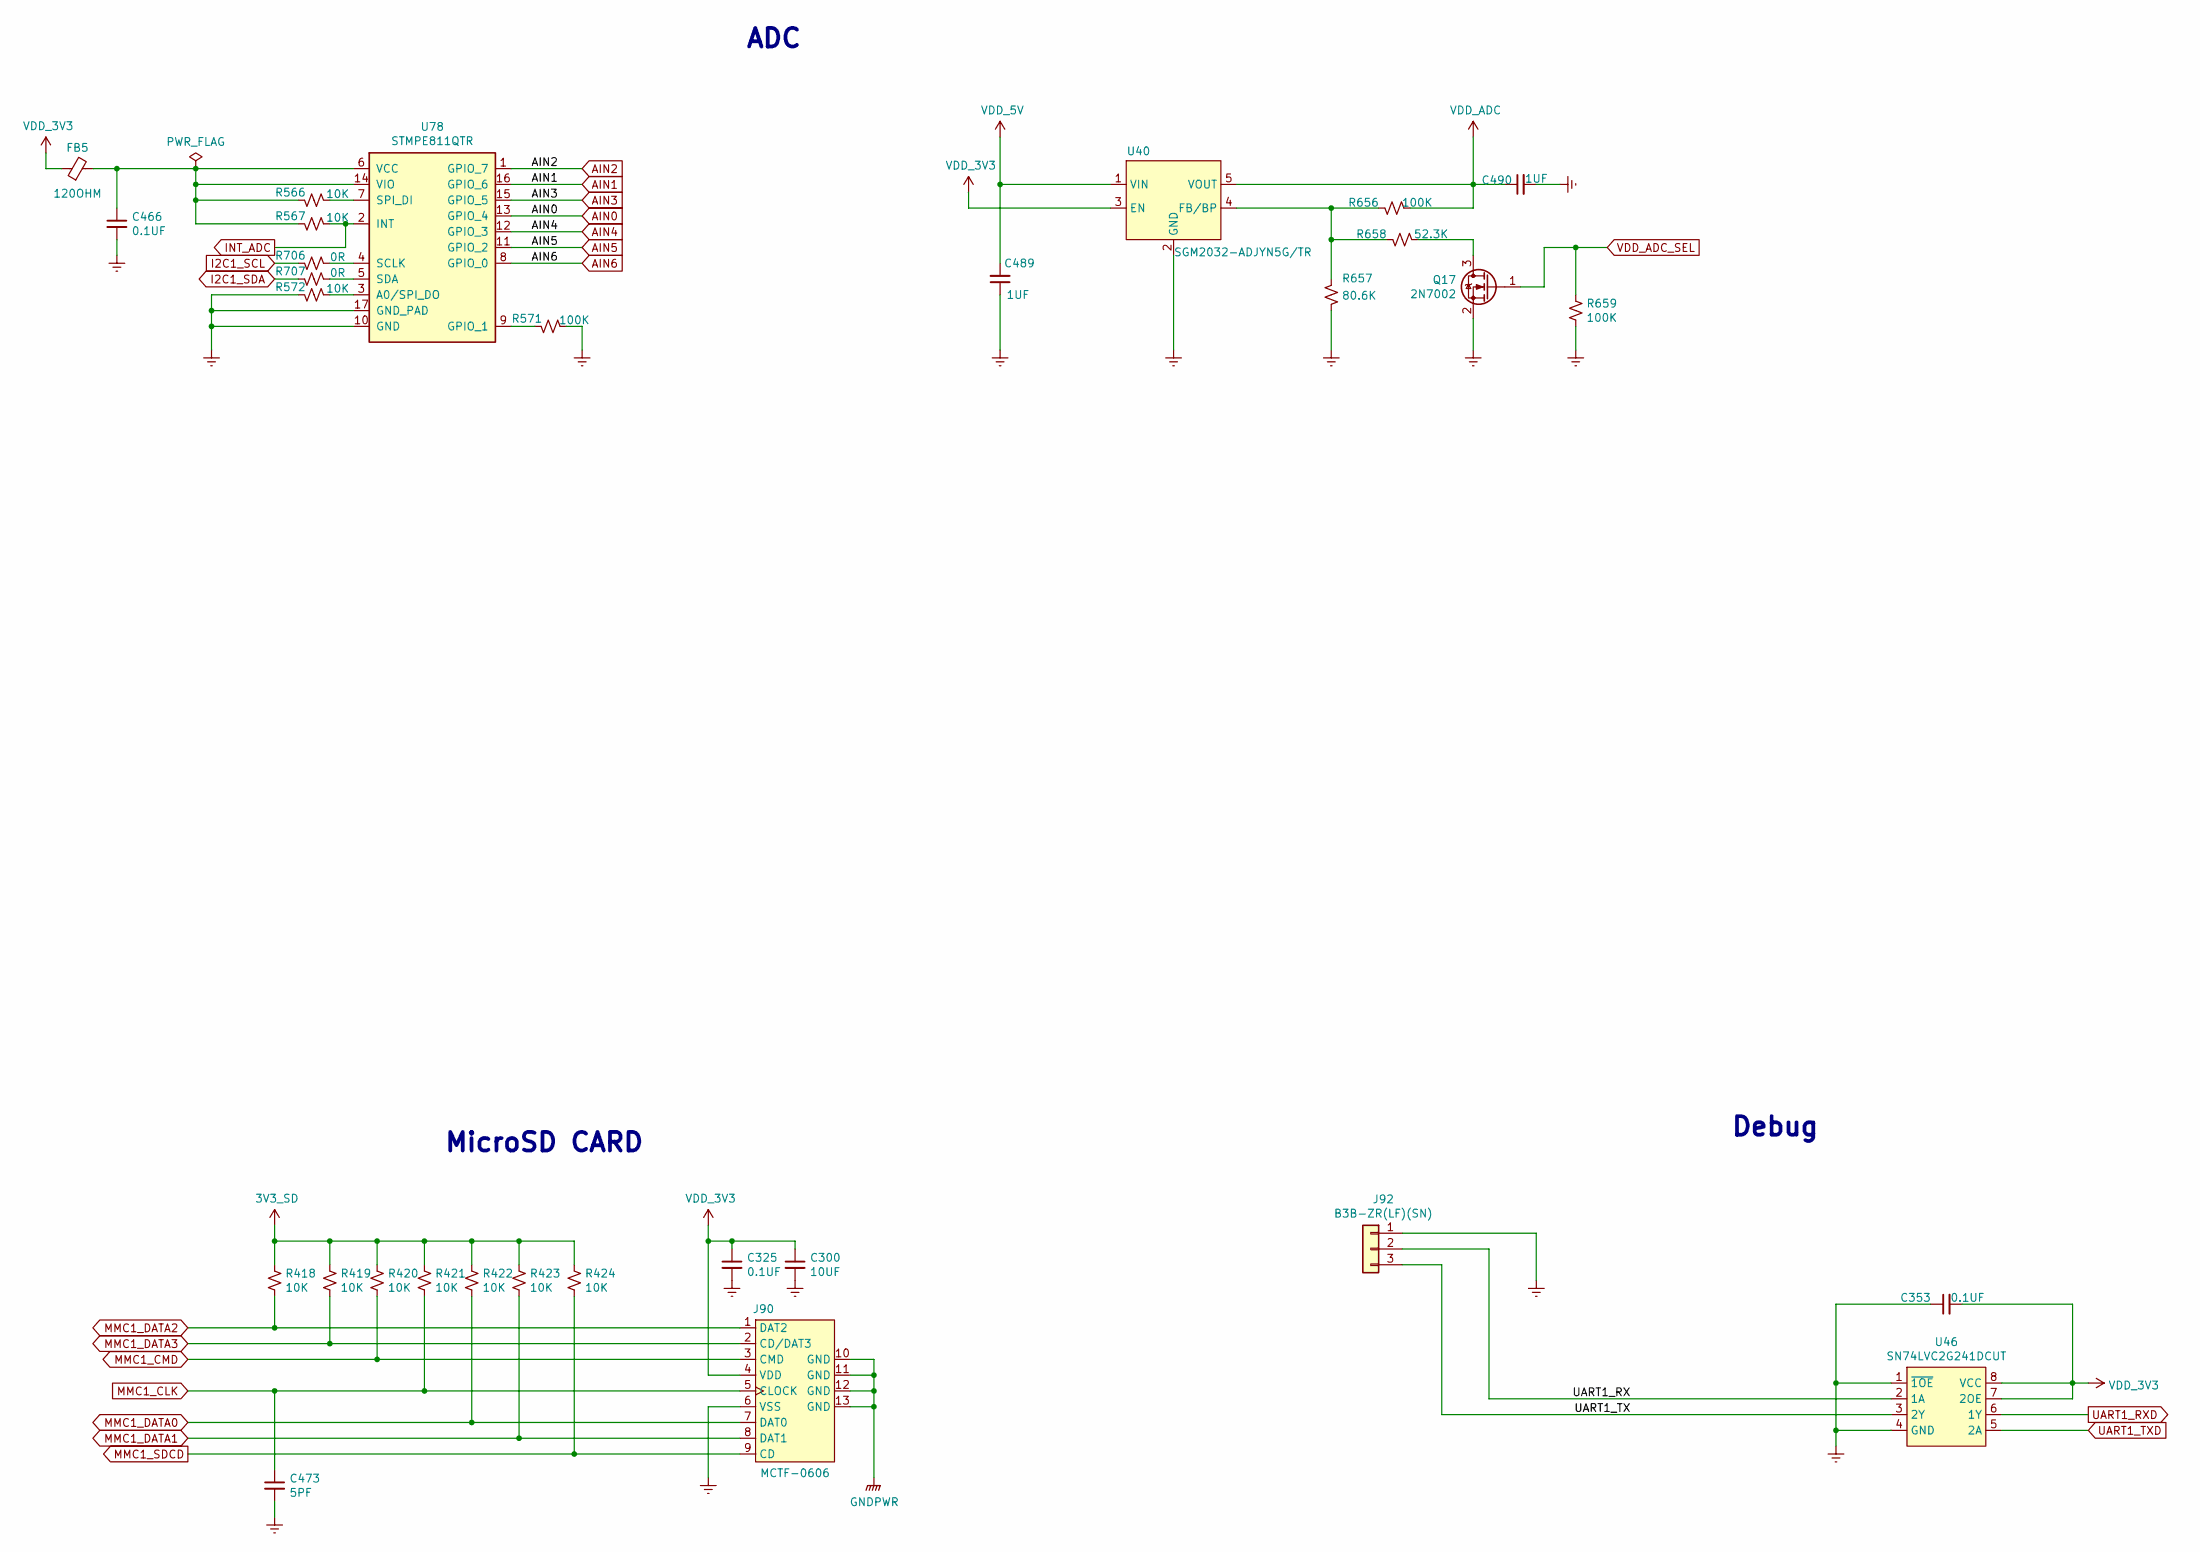
[picture p122: schematic adc.kicad_sch]

Parts:
C300: 10UF; C0603; Rating 10V,X5R; Manufacturer P/N GRM188R61A106KE69D
C325, C353, C466: 0.1UF; C0402; Rating 16V,X7R; Manufacturer P/N GRM155R71C104KA88D
C473: 5PF; C0402; Rating 50V,C0G; Manufacturer P/N GRM1555C1H5R0CA01D
C489, C490: 1UF; C0402; Rating 10V,X5R; Manufacturer P/N GRM155R61A105KE15D
FB5: 120OHM; L0402; Rating 1300mA; Manufacturer P/N BLM15PD121SN1D
J90: MCTF-0606; SD_HSF-COMPLIANT_MCTF-0606; Manufacturer P/N Card Connector MCTF-0606 Connector,Micr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
J92: B3B-ZR(LF)(SN); CON3B35X60; Manufacturer P/N Connector, Wire-To-Board Top Entry, ZH 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
Q17: 2N7002; SOT-23; Manufacturer P/N 2N7002
R418, R419, R420, R421, R422, R423, R424: 10K; R0402; Rating 1%; Manufacturer P/N RC0402FR-0710KL
R566, R567, R572: 10K; R0402; Rating 5%; Manufacturer P/N RC0402JR-0710KL
R571: 100K; R0402; Rating 5%; Manufacturer P/N RC0402JR-07100KL
R656, R659: 100K; R0402; Rating 1%; Manufacturer P/N RC0402FR-07100KL
R657: 80.6K; R0402; Rating 1%; Manufacturer P/N RC0402FR-0780K6L
R658: 52.3K; R0402; Rating 1%; Manufacturer P/N RC0402FR-0752K3L
R706, R707: 0R; R0402; Rating 5%; Manufacturer P/N RC0402JR-070RL
U40: SGM2032-ADJYN5G/TR; SOT23_5; Manufacturer P/N SGM2032-ADJYN5G/TR
U46: SN74LVC2G241DCUT; VSSOP8CR; Manufacturer P/N SN74LVC2G241DCUT
U78: STMPE811QTR; QFN50P300X300X100-17N; Manufacturer P/N STMPE811QTR

Connections:
3V3_SD: R418.1, R419.1, R420.1, R421.1, R422.1, R423.1, R424.1
AIN0: U78.13 (GPIO_4)
AIN1: U78.16 (GPIO_6)
AIN2: U78.1 (GPIO_7)
AIN3: U78.15 (GPIO_5)
AIN4: U78.12 (GPIO_3)
AIN5: U78.11 (GPIO_2)
AIN6: U78.8 (GPIO_0)
Earth: C300.2, C325.2, C353.1, C466.2, C473.2, C489.1, C490.2, J90.6 (VSS), J92.1, Q17.2 (S), R571.2, R572.1, R657.1, R659.2, U40.2 (GND), U46.1 (~1OE), U46.4 (GND), U78.10 (GND), U78.17 (GND_PAD)
GNDPWR: J90.10 (GND), J90.11 (GND), J90.12 (GND), J90.13 (GND)
I2C1_SCL: R706.1
I2C1_SDA: R707.1
INT_ADC: R567.2, U78.2 (INT)
MMC1_CLK: C473.1, J90.5 (CLOCK), R421.2
MMC1_CMD: J90.3 (CMD), R420.2
MMC1_DATA0: J90.7 (DAT0), R422.2
MMC1_DATA1: J90.8 (DAT1), R423.2
MMC1_DATA2: J90.1 (DAT2), R418.2
MMC1_DATA3: J90.2 (CD/DAT3), R419.2
MMC1_SDCD: J90.9 (CD), R424.2
unnamed: C466.1, FB5.2, R566.1, R567.1, U78.6 (VCC), U78.14 (VIO)
unnamed: Q17.3 (D), R658.2
unnamed: R566.2, U78.7 (SPI_DI)
unnamed: R571.1, U78.9 (GPIO_1)
unnamed: R572.2, U78.3 (A0/SPI_DO)
unnamed: R656.1, R657.2, R658.1, U40.4 (FB/BP)
unnamed: R706.2, U78.4 (SCLK)
unnamed: R707.2, U78.5 (SDA)
UART1_RX: J92.2, U46.2 (1A)
UART1_RXD: U46.6 (1Y)
UART1_TX: J92.3, U46.3 (2Y)
UART1_TXD: U46.5 (2A)
VDD_3V3: C300.1, C325.1, C353.2, FB5.1, J90.4 (VDD), U40.3 (EN), U46.7 (2OE), U46.8 (VCC)
VDD_5V: C489.2, U40.1 (VIN)
VDD_ADC: C490.1, R656.2, U40.5 (VOUT)
VDD_ADC_SEL: Q17.1 (G), R659.1

Notes on the sheet:
MicroSD CARD
ADC
Debug
