beagleboard/beaglebone-ai/kicad/beaglebone-ai-rev-a1/am572system.kicad_sch

## KiCad design kicad/beaglebone-ai-rev-a1/am572system.kicad_sch (2021-06-15)

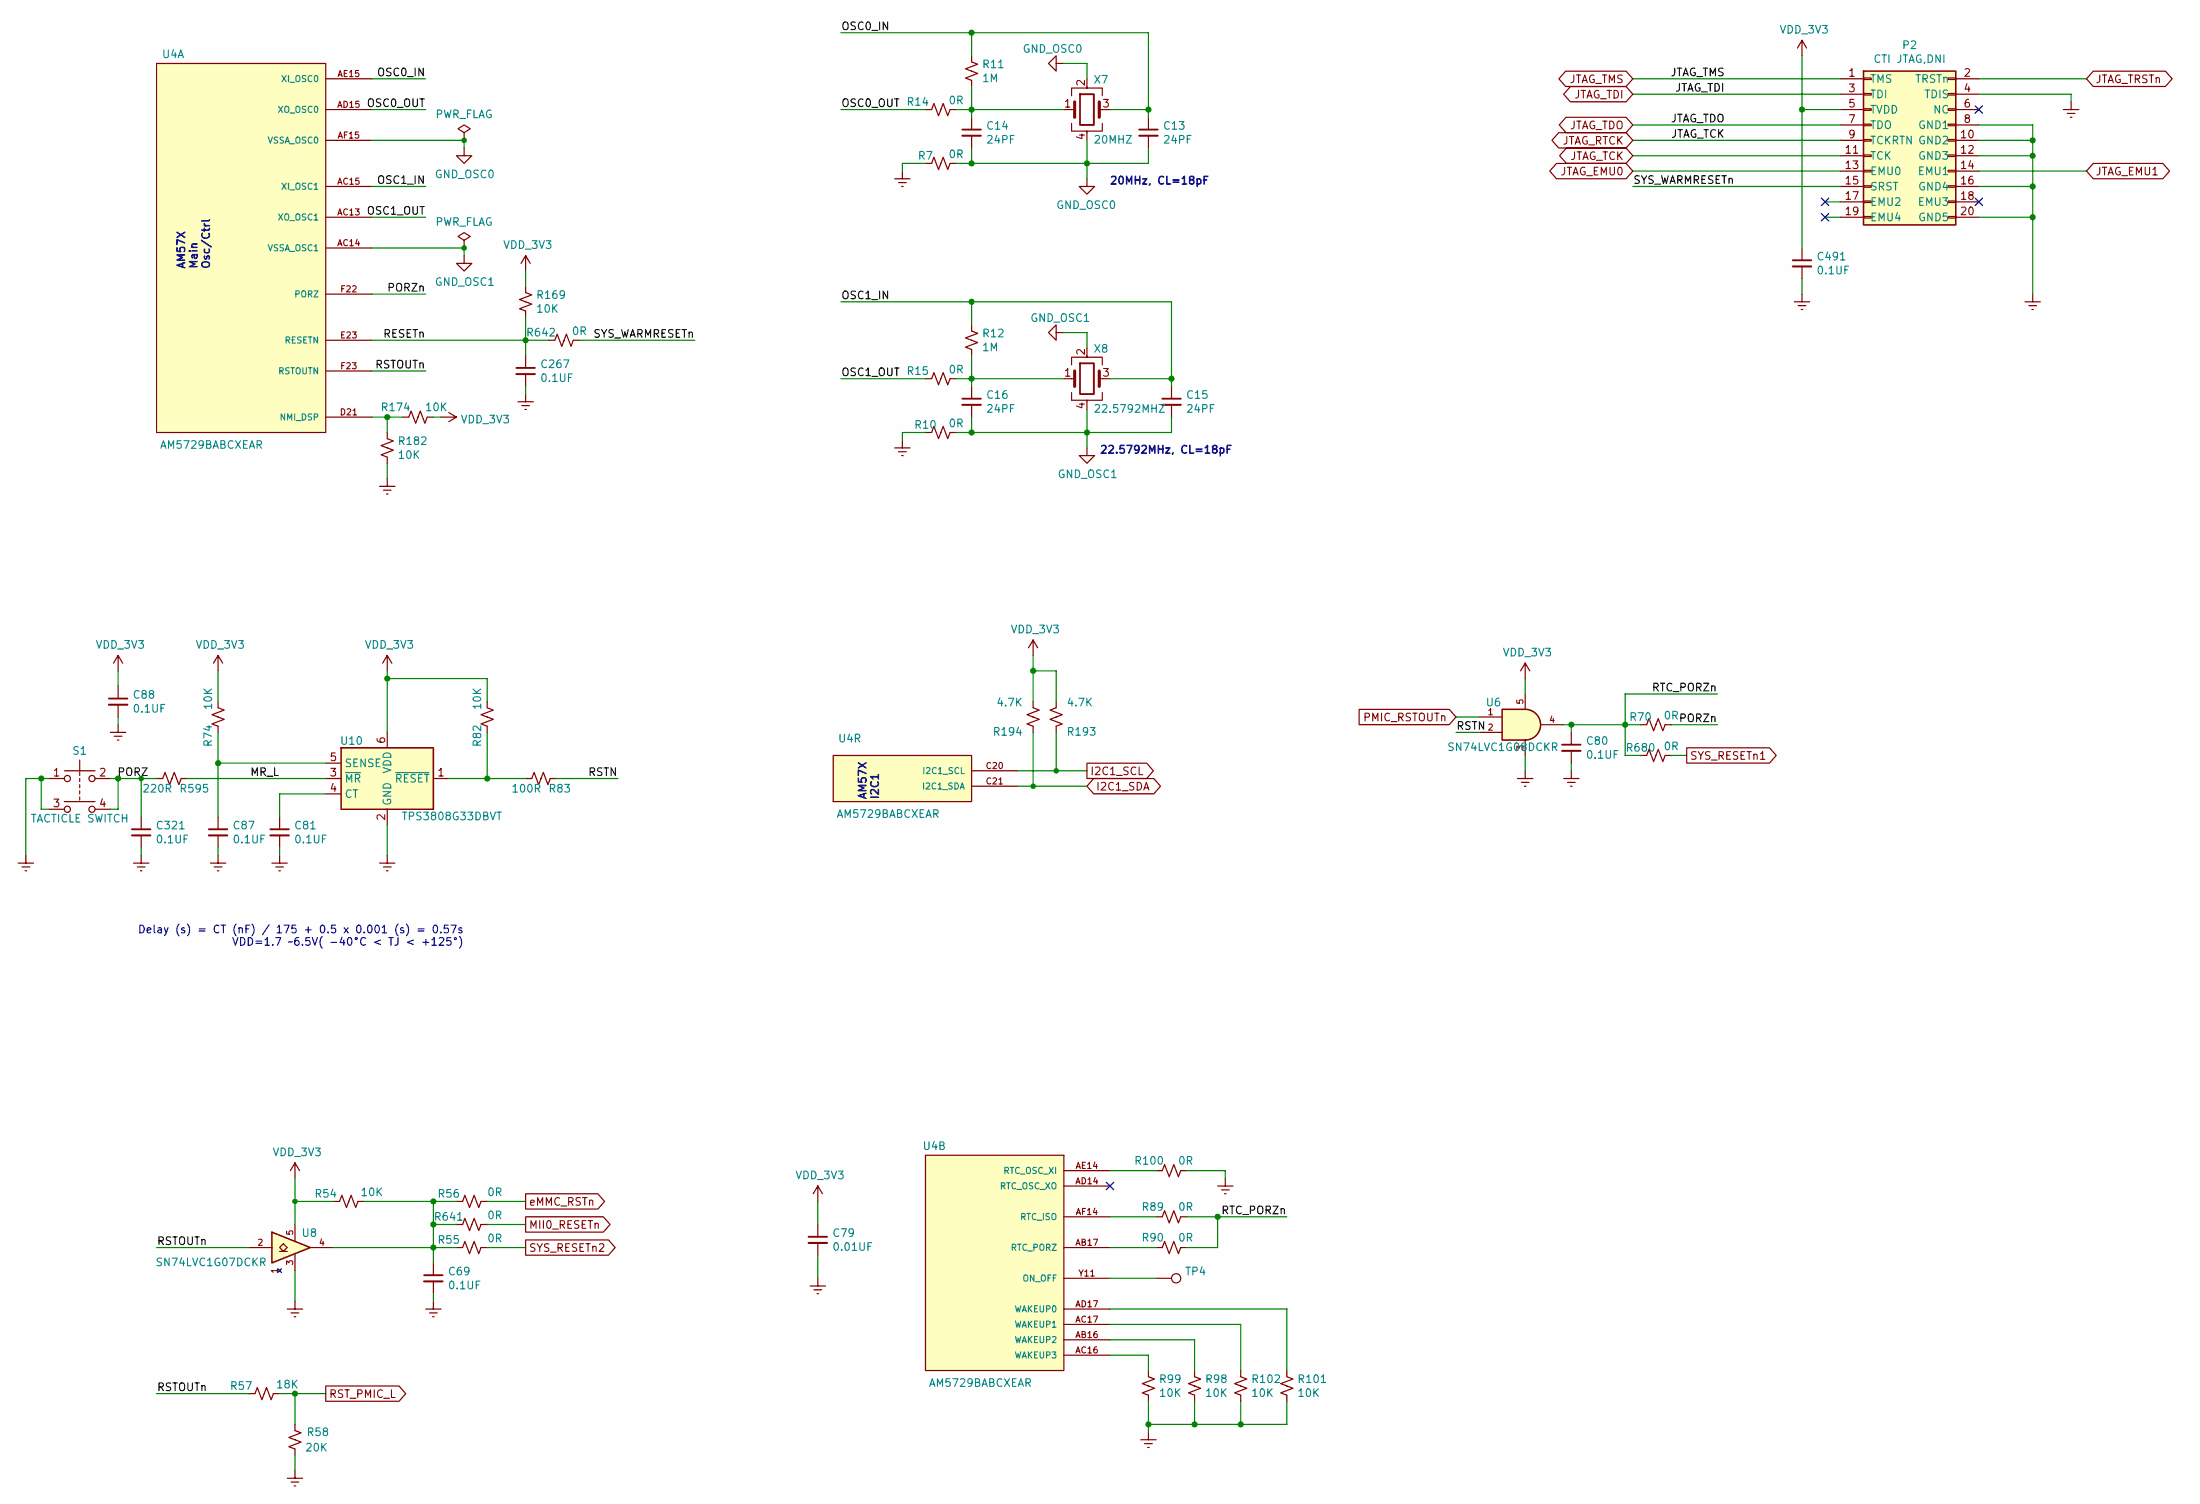
[picture p123: schematic am572system.kicad_sch]

Parts:
C13, C14, C15, C16: 24PF; C0402; Rating 50V,C0G; Manufacturer P/N GRM1555C1H240JA01D
C69, C80, C81, C87, C88, C267, C321, C491: 0.1UF; C0402; Rating 16V,X7R; Manufacturer P/N GRM155R71C104KA88D
C79: 0.01UF; C0402; Rating X7R,16V; Manufacturer P/N GRM155R71C103KA01D
P2: CTI JTAG,DNI; HEADER10X2_SMD; Manufacturer P/N Dual Line Header 10x2pin Tin
R7, R10, R14, R15, R55, R56, R70, R89, R90, R100, R641, R642, R680: 0R; R0402; Rating 5%; Manufacturer P/N RC0402JR-070RL
R11, R12: 1M; R0402; Rating 5%; Manufacturer P/N RC0402JR-071ML
R54, R74, R82, R98, R99, R101, R102, R169, R174, R182: 10K; R0402; Rating 5%; Manufacturer P/N RC0402JR-0710KL
R57: 18K; R0402; Rating 1%; Manufacturer P/N RC0402FR-0718KL
R58: 20K; R0402; Rating 1%; Manufacturer P/N RC0402FR-0720KL
R83: 100R; R0402; Rating 5%; Manufacturer P/N RC0402JR-07100RL
R193, R194: 4.7K; R0402; Rating 5%; Manufacturer P/N RC0402JR-074K7L
R595: 220R; R0402; Rating 5%; Manufacturer P/N RC0402JR-07220RL
S1: TACTICLE SWITCH; SWS4B46X28; Manufacturer P/N KMR231GLFS
TP4: NI; TP30
U4: AM5729BABCXEAR; BGA760C80P28X28_2300X2300X255; Manufacturer P/N AM5729BABCXEAR
U6: SN74LVC1G08DCKR; SC70_5; Manufacturer P/N SN74LVC1G08DCKR
U8: SN74LVC1G07DCKR; SC70_5; Manufacturer P/N SN74LVC1G07DCKR
U10: TPS3808G33DBVT; SOT-23-6; Manufacturer P/N TPS3808G33DBVT
X7: 20MHZ; OSCCC250X200X60-4N; Rating 10PPM; Manufacturer P/N 5ZAA20000181TFA2Q3
X8: 22.5792MHZ; OSCCC250X200X60-4N; Rating 20PPM; Manufacturer P/N 5ZAA22579182TFA0Q3

Connections:
Earth: C69.2, C79.2, C80.2, C81.2, C87.2, C88.2, C267.2, C321.2, C491.2, P2.4 (TDIS), P2.8 (GND1), P2.10 (GND2), P2.12 (GND3), P2.16 (GND4), P2.20 (GND5), R7.1, R10.1, R58.1, R98.2, R99.2, R100.2, R101.2, R102.2, R182.2, S1.1, S1.3, U6.3 (GND), U8.3 (GND), U10.2 (GND)
GND_OSC0: C13.2, C14.2, R7.2, U4.AF15 (VSSA_OSC0), X7.2, X7.4
GND_OSC1: C15.2, C16.2, R10.2, U4.AC14 (VSSA_OSC1), X8.2, X8.4
I2C1_SCL: R193.1, U4.C20 (I2C1_SCL)
I2C1_SDA: R194.1, U4.C21 (I2C1_SDA)
JTAG_EMU0: P2.13 (EMU0)
JTAG_EMU1: P2.14 (EMU1)
JTAG_RTCK: P2.9 (TCKRTN)
JTAG_TCK: P2.11 (TCK)
JTAG_TDI: P2.3 (TDI)
JTAG_TDO: P2.7 (TDO)
JTAG_TMS: P2.1 (TMS)
JTAG_TRSTn: P2.2 (TRSTn)
MII0_RESETn: R641.2
MR_L: R595.1, U10.3 (~MR)
unnamed: C14.1, R11.1, R14.1, X7.1
unnamed: C16.1, R12.1, R15.1, X8.1
unnamed: C69.1, R54.2, R55.1, R56.1, R641.1, U8.4
unnamed: C81.1, U10.4 (CT)
unnamed: C87.1, R74.1, U10.5 (SENSE)
unnamed: R82.1, R83.2, U10.1 (~RESET)
unnamed: R89.1, U4.AF14 (RTC_ISO)
unnamed: R90.1, U4.AB17 (RTC_PORZ)
unnamed: R98.1, U4.AB16 (WAKEUP2)
unnamed: R99.1, U4.AC16 (WAKEUP3)
unnamed: R100.1, U4.AE14 (RTC_OSC_XI)
unnamed: R101.1, U4.AD17 (WAKEUP0)
unnamed: R102.1, U4.AC17 (WAKEUP1)
unnamed: R174.1, R182.1, U4.D21 (NMI_DSP)
unnamed: TP4.1, U4.Y11 (ON_OFF)
OSC0_IN: C13.1, R11.2, U4.AE15 (XI_OSC0), X7.3
OSC0_OUT: R14.2, U4.AD15 (XO_OSC0)
OSC1_IN: C15.1, R12.2, U4.AC15 (XI_OSC1), X8.3
OSC1_OUT: R15.2, U4.AC13 (XO_OSC1)
PMIC_RSTOUTn: U6.1
PORZ: C321.1, R595.2, S1.2, S1.4
PORZn: R70.2, U4.F22 (PORZ)
RESETn: C267.1, R169.2, R642.1, U4.E23 (RESETN)
RSTN: R83.1, U6.2
RSTOUTn: R57.1, U4.F23 (RSTOUTN), U8.2
RST_PMIC_L: R57.2, R58.2
RTC_PORZn: C80.1, R70.1, R89.2, R90.2, R680.1, U6.4
SYS_RESETn1: R680.2
SYS_RESETn2: R55.2
SYS_WARMRESETn: P2.15 (SRST), R642.2
VDD_3V3: C79.1, C88.1, C491.1, P2.5 (TVDD), R54.1, R74.2, R82.2, R169.1, R174.2, R193.2, R194.2, U6.5 (VCC), U8.5 (VCC), U10.6 (VDD)
eMMC_RSTn: R56.2

Notes on the sheet:
AM57X Main Osc/Ctrl
Delay (s) = CT (nF) / 175 + 0.5 x 0.001 (s) = 0.57s VDD=1.7 ~~6.5V( -40°C < TJ < +125°)
AM57X I2C1
20MHz, CL=18pF
22.5792MHz, CL=18pF
