beagleboard/beaglebone-ai/kicad/beaglebone-ai-rev-a1/ddr1.kicad_sch

## KiCad design kicad/beaglebone-ai-rev-a1/ddr1.kicad_sch (2021-06-15)

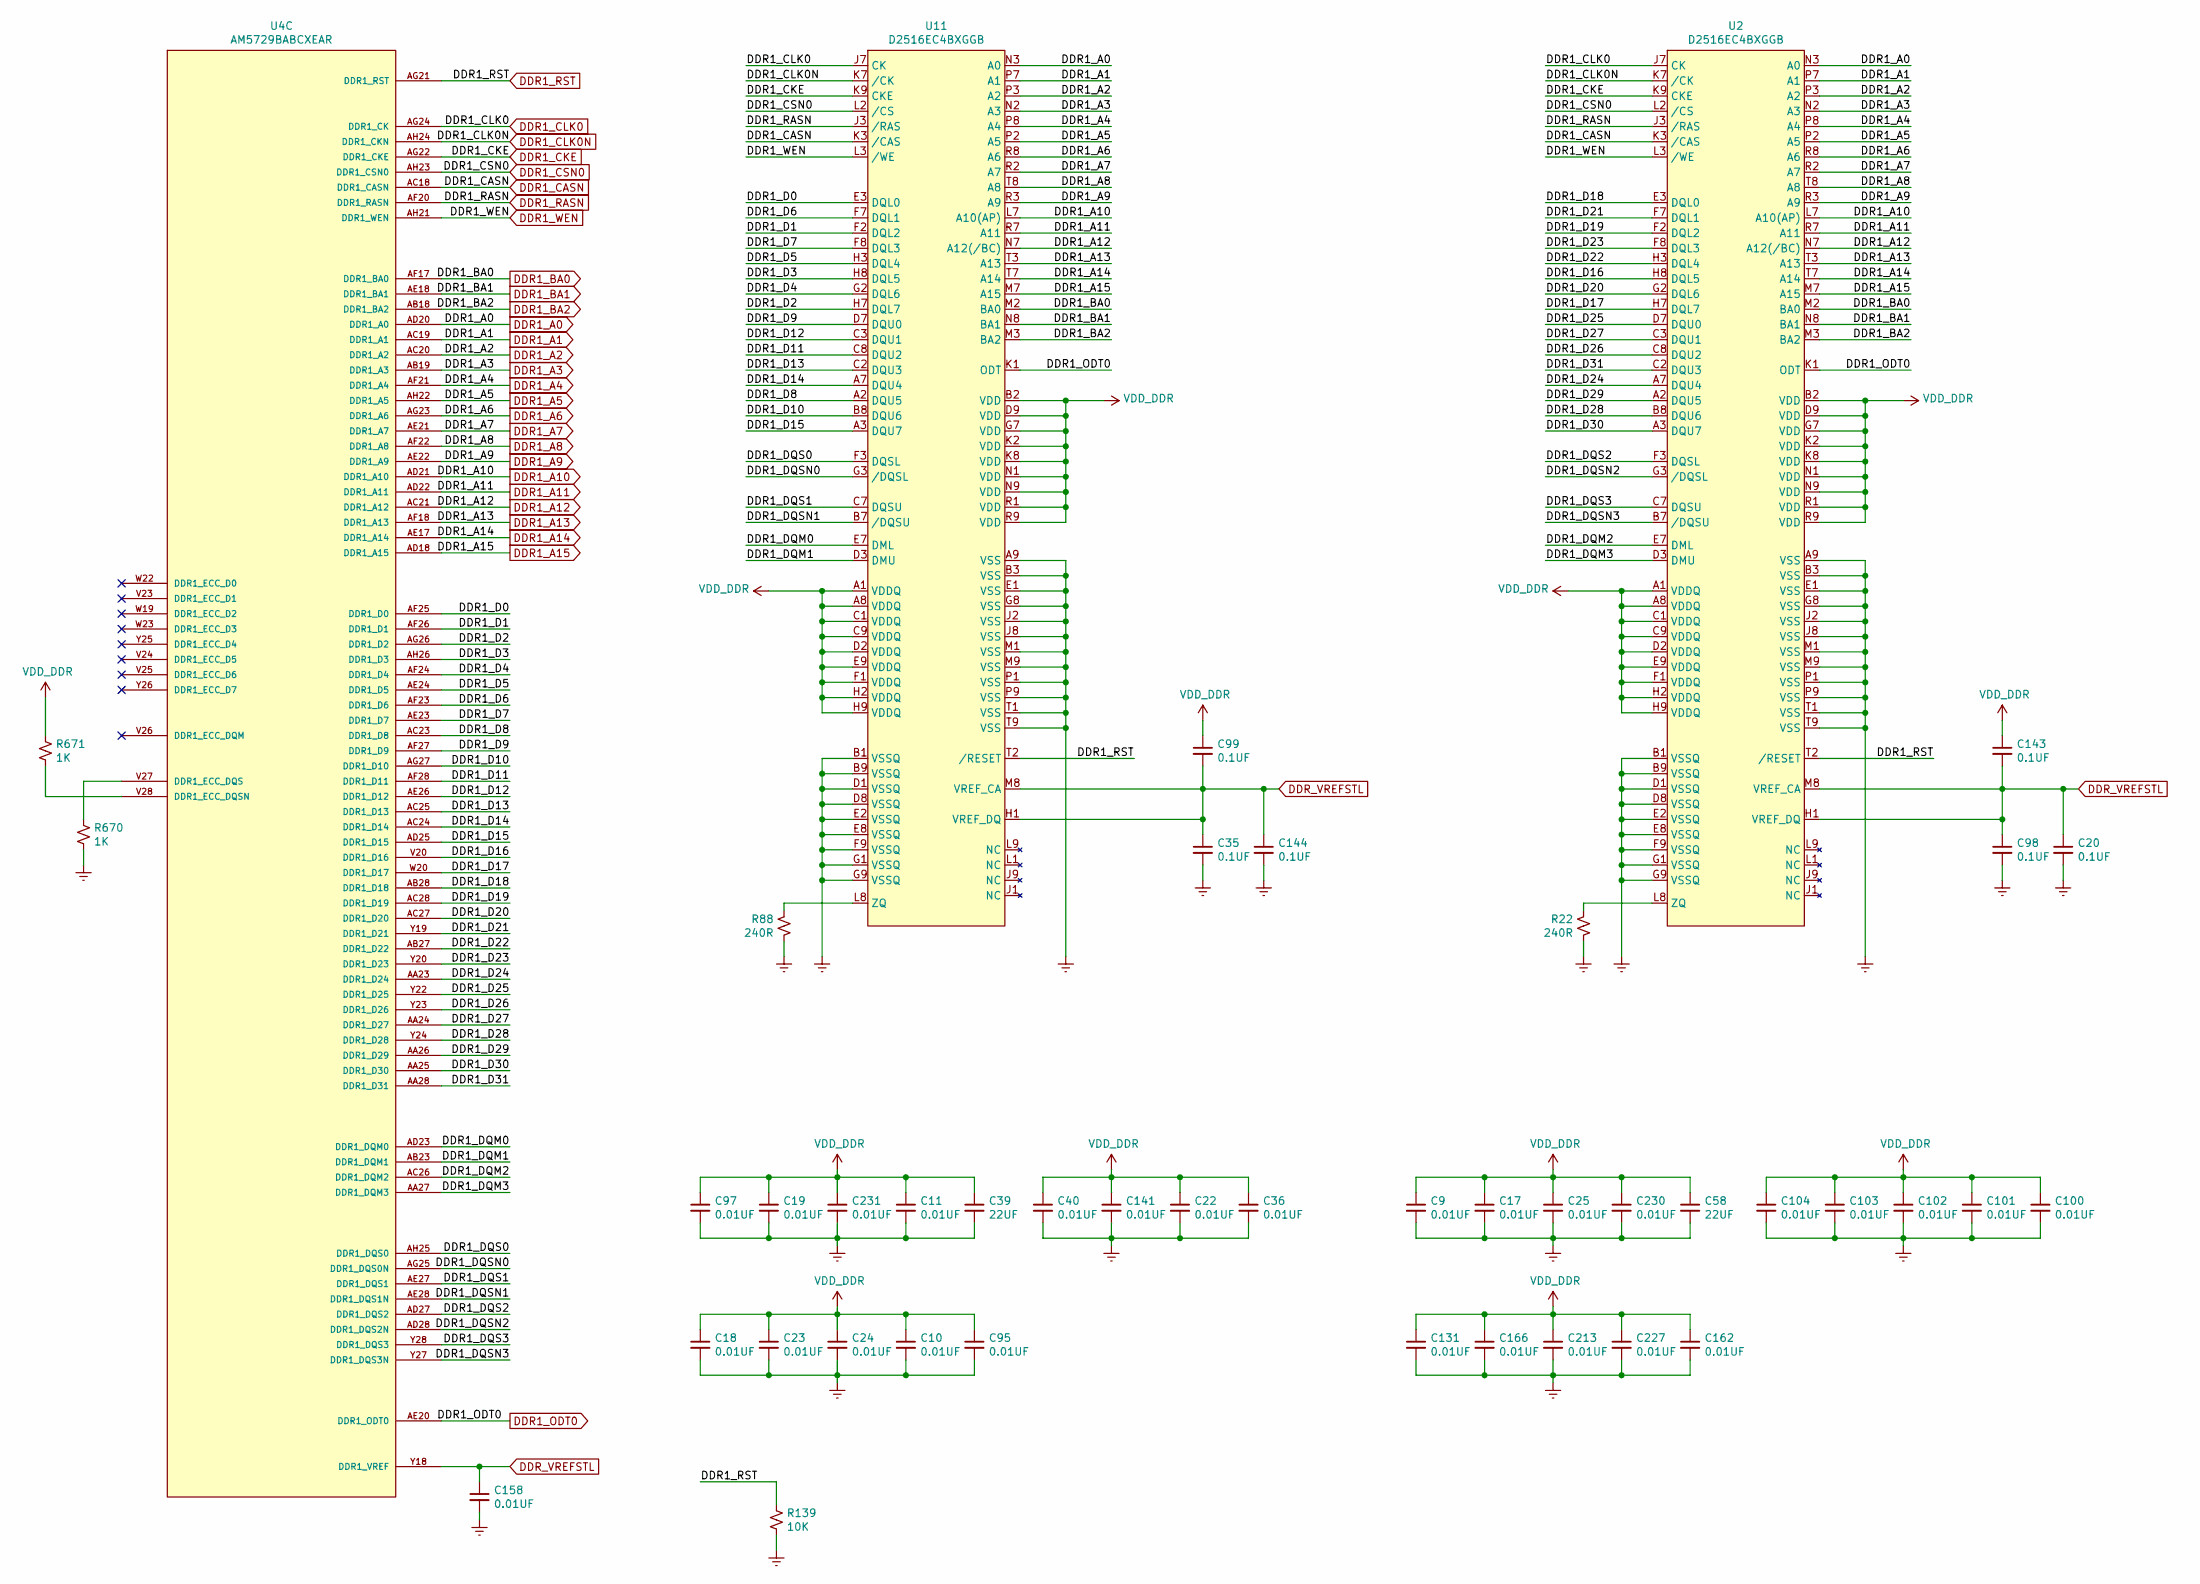
[picture p124: schematic ddr1.kicad_sch]

Parts:
C9, C10, C11, C17, C18, C19, C22, C23, C24, C25, C36, C40, C95, C97, C100, C101, C102, C103, C104, C131, C141, C158, C162, C166, C213, C227, C230, C231: 0.01UF; C0402; Rating X7R,16V; Manufacturer P/N GRM155R71C103KA01D
C20, C35, C98, C99, C143, C144: 0.1UF; C0402; Rating 16V,X7R; Manufacturer P/N GRM155R71C104KA88D
C39: 22UF; C0603; Rating 6.3V,X5R; Manufacturer P/N GRM188R60J226MEA0D
C58: 22UF; C0603; Rating 10V,X5R; Manufacturer P/N GRM188R61A226ME15D
R22, R88: 240R; R0402; Rating 1%; Manufacturer P/N RC0402FR-07240RL
R139: 10K; R0402; Rating 5%; Manufacturer P/N RC0402JR-0710KL
R670, R671: 1K; R0402; Rating 5%; Manufacturer P/N RC0402JR-071KL
U2, U11: D2516EC4BXGGB; BGA96G; Manufacturer P/N D2516EC4BXGGB
U4: AM5729BABCXEAR; BGA760C80P28X28_2300X2300X255; Manufacturer P/N AM5729BABCXEAR

Connections:
DDR1_A0: U2.N3 (A0), U4.AD20 (DDR1_A0), U11.N3 (A0)
DDR1_A1: U2.P7 (A1), U4.AC19 (DDR1_A1), U11.P7 (A1)
DDR1_A2: U2.P3 (A2), U4.AC20 (DDR1_A2), U11.P3 (A2)
DDR1_A3: U2.N2 (A3), U4.AB19 (DDR1_A3), U11.N2 (A3)
DDR1_A4: U2.P8 (A4), U4.AF21 (DDR1_A4), U11.P8 (A4)
DDR1_A5: U2.P2 (A5), U4.AH22 (DDR1_A5), U11.P2 (A5)
DDR1_A6: U2.R8 (A6), U4.AG23 (DDR1_A6), U11.R8 (A6)
DDR1_A7: U2.R2 (A7), U4.AE21 (DDR1_A7), U11.R2 (A7)
DDR1_A8: U2.T8 (A8), U4.AF22 (DDR1_A8), U11.T8 (A8)
DDR1_A9: U2.R3 (A9), U4.AE22 (DDR1_A9), U11.R3 (A9)
DDR1_A10: U2.L7 (A10(AP)), U4.AD21 (DDR1_A10), U11.L7 (A10(AP))
DDR1_A11: U2.R7 (A11), U4.AD22 (DDR1_A11), U11.R7 (A11)
DDR1_A12: U2.N7 (A12(/BC)), U4.AC21 (DDR1_A12), U11.N7 (A12(/BC))
DDR1_A13: U2.T3 (A13), U4.AF18 (DDR1_A13), U11.T3 (A13)
DDR1_A14: U2.T7 (A14), U4.AE17 (DDR1_A14), U11.T7 (A14)
DDR1_A15: U2.M7 (A15), U4.AD18 (DDR1_A15), U11.M7 (A15)
DDR1_BA0: U2.M2 (BA0), U4.AF17 (DDR1_BA0), U11.M2 (BA0)
DDR1_BA1: U2.N8 (BA1), U4.AE18 (DDR1_BA1), U11.N8 (BA1)
DDR1_BA2: U2.M3 (BA2), U4.AB18 (DDR1_BA2), U11.M3 (BA2)
DDR1_CASN: U2.K3 (/CAS), U4.AC18 (DDR1_CASN), U11.K3 (/CAS)
DDR1_CKE: U2.K9 (CKE), U4.AG22 (DDR1_CKE), U11.K9 (CKE)
DDR1_CLK0: U2.J7 (CK), U4.AG24 (DDR1_CK), U11.J7 (CK)
DDR1_CLK0N: U2.K7 (/CK), U4.AH24 (DDR1_CKN), U11.K7 (/CK)
DDR1_CSN0: U2.L2 (/CS), U4.AH23 (DDR1_CSN0), U11.L2 (/CS)
DDR1_D0: U4.AF25 (DDR1_D0), U11.E3 (DQL0)
DDR1_D1: U4.AF26 (DDR1_D1), U11.F2 (DQL2)
DDR1_D2: U4.AG26 (DDR1_D2), U11.H7 (DQL7)
DDR1_D3: U4.AH26 (DDR1_D3), U11.H8 (DQL5)
DDR1_D4: U4.AF24 (DDR1_D4), U11.G2 (DQL6)
DDR1_D5: U4.AE24 (DDR1_D5), U11.H3 (DQL4)
DDR1_D6: U4.AF23 (DDR1_D6), U11.F7 (DQL1)
DDR1_D7: U4.AE23 (DDR1_D7), U11.F8 (DQL3)
DDR1_D8: U4.AC23 (DDR1_D8), U11.A2 (DQU5)
DDR1_D9: U4.AF27 (DDR1_D9), U11.D7 (DQU0)
DDR1_D10: U4.AG27 (DDR1_D10), U11.B8 (DQU6)
DDR1_D11: U4.AF28 (DDR1_D11), U11.C8 (DQU2)
DDR1_D12: U4.AE26 (DDR1_D12), U11.C3 (DQU1)
DDR1_D13: U4.AC25 (DDR1_D13), U11.C2 (DQU3)
DDR1_D14: U4.AC24 (DDR1_D14), U11.A7 (DQU4)
DDR1_D15: U4.AD25 (DDR1_D15), U11.A3 (DQU7)
DDR1_D16: U2.H8 (DQL5), U4.V20 (DDR1_D16)
DDR1_D17: U2.H7 (DQL7), U4.W20 (DDR1_D17)
DDR1_D18: U2.E3 (DQL0), U4.AB28 (DDR1_D18)
DDR1_D19: U2.F2 (DQL2), U4.AC28 (DDR1_D19)
DDR1_D20: U2.G2 (DQL6), U4.AC27 (DDR1_D20)
DDR1_D21: U2.F7 (DQL1), U4.Y19 (DDR1_D21)
DDR1_D22: U2.H3 (DQL4), U4.AB27 (DDR1_D22)
DDR1_D23: U2.F8 (DQL3), U4.Y20 (DDR1_D23)
DDR1_D24: U2.A7 (DQU4), U4.AA23 (DDR1_D24)
DDR1_D25: U2.D7 (DQU0), U4.Y22 (DDR1_D25)
DDR1_D26: U2.C8 (DQU2), U4.Y23 (DDR1_D26)
DDR1_D27: U2.C3 (DQU1), U4.AA24 (DDR1_D27)
DDR1_D28: U2.B8 (DQU6), U4.Y24 (DDR1_D28)
DDR1_D29: U2.A2 (DQU5), U4.AA26 (DDR1_D29)
DDR1_D30: U2.A3 (DQU7), U4.AA25 (DDR1_D30)
DDR1_D31: U2.C2 (DQU3), U4.AA28 (DDR1_D31)
DDR1_DQM0: U4.AD23 (DDR1_DQM0), U11.E7 (DML)
DDR1_DQM1: U4.AB23 (DDR1_DQM1), U11.D3 (DMU)
DDR1_DQM2: U2.E7 (DML), U4.AC26 (DDR1_DQM2)
DDR1_DQM3: U2.D3 (DMU), U4.AA27 (DDR1_DQM3)
DDR1_DQS0: U4.AH25 (DDR1_DQS0), U11.F3 (DQSL)
DDR1_DQS1: U4.AE27 (DDR1_DQS1), U11.C7 (DQSU)
DDR1_DQS2: U2.F3 (DQSL), U4.AD27 (DDR1_DQS2)
DDR1_DQS3: U2.C7 (DQSU), U4.Y28 (DDR1_DQS3)
DDR1_DQSN0: U4.AG25 (DDR1_DQS0N), U11.G3 (/DQSL)
DDR1_DQSN1: U4.AE28 (DDR1_DQS1N), U11.B7 (/DQSU)
DDR1_DQSN2: U2.G3 (/DQSL), U4.AD28 (DDR1_DQS2N)
DDR1_DQSN3: U2.B7 (/DQSU), U4.Y27 (DDR1_DQS3N)
DDR1_ODT0: U2.K1 (ODT), U4.AE20 (DDR1_ODT0), U11.K1 (ODT)
DDR1_RASN: U2.J3 (/RAS), U4.AF20 (DDR1_RASN), U11.J3 (/RAS)
DDR1_RST: R139.1, U2.T2 (/RESET), U4.AG21 (DDR1_RST), U11.T2 (/RESET)
DDR1_WEN: U2.L3 (/WE), U4.AH21 (DDR1_WEN), U11.L3 (/WE)
DDR_VREFSTL: C20.1, C35.1, C98.1, C99.2, C143.2, C144.1, C158.1, U2.H1 (VREF_DQ), U2.M8 (VREF_CA), U4.Y18 (DDR1_VREF), U11.H1 (VREF_DQ), U11.M8 (VREF_CA)
Earth: C9.2, C10.2, C11.2, C17.2, C18.2, C19.2, C20.2, C22.2, C23.2, C24.2, C25.2, C35.2, C36.2, C39.2, C40.2, C58.2, C95.2, C97.2, C98.2, C100.2, C101.2, C102.2, C103.2, C104.2, C131.2, C141.2, C144.2, C158.2, C162.2, C166.2, C213.2, C227.2, C230.2, C231.2, R22.1, R88.1, R139.2, R670.2, U2.A9 (VSS), U2.B1 (VSSQ), U2.B3 (VSS), U2.B9 (VSSQ), U2.D1 (VSSQ), U2.D8 (VSSQ), U2.E1 (VSS), U2.E2 (VSSQ), U2.E8 (VSSQ), U2.F9 (VSSQ), U2.G1 (VSSQ), U2.G8 (VSS), U2.G9 (VSSQ), U2.J2 (VSS), U2.J8 (VSS), U2.M1 (VSS), U2.M9 (VSS), U2.P1 (VSS), U2.P9 (VSS), U2.T1 (VSS), U2.T9 (VSS), U11.A9 (VSS), U11.B1 (VSSQ), U11.B3 (VSS), U11.B9 (VSSQ), U11.D1 (VSSQ), U11.D8 (VSSQ), U11.E1 (VSS), U11.E2 (VSSQ), U11.E8 (VSSQ), U11.F9 (VSSQ), U11.G1 (VSSQ), U11.G8 (VSS), U11.G9 (VSSQ), U11.J2 (VSS), U11.J8 (VSS), U11.M1 (VSS), U11.M9 (VSS), U11.P1 (VSS), U11.P9 (VSS), U11.T1 (VSS), U11.T9 (VSS)
unnamed: R22.2, U2.L8 (ZQ)
unnamed: R88.2, U11.L8 (ZQ)
unnamed: R670.1, U4.V27 (DDR1_ECC_DQS)
unnamed: R671.2, U4.V28 (DDR1_ECC_DQSN)
VDD_DDR: C9.1, C10.1, C11.1, C17.1, C18.1, C19.1, C22.1, C23.1, C24.1, C25.1, C36.1, C39.1, C40.1, C58.1, C95.1, C97.1, C99.1, C100.1, C101.1, C102.1, C103.1, C104.1, C131.1, C141.1, C143.1, C162.1, C166.1, C213.1, C227.1, C230.1, C231.1, R671.1, U2.A1 (VDDQ), U2.A8 (VDDQ), U2.B2 (VDD), U2.C1 (VDDQ), U2.C9 (VDDQ), U2.D2 (VDDQ), U2.D9 (VDD), U2.E9 (VDDQ), U2.F1 (VDDQ), U2.G7 (VDD), U2.H2 (VDDQ), U2.H9 (VDDQ), U2.K2 (VDD), U2.K8 (VDD), U2.N1 (VDD), U2.N9 (VDD), U2.R1 (VDD), U2.R9 (VDD), U11.A1 (VDDQ), U11.A8 (VDDQ), U11.B2 (VDD), U11.C1 (VDDQ), U11.C9 (VDDQ), U11.D2 (VDDQ), U11.D9 (VDD), U11.E9 (VDDQ), U11.F1 (VDDQ), U11.G7 (VDD), U11.H2 (VDDQ), U11.H9 (VDDQ), U11.K2 (VDD), U11.K8 (VDD), U11.N1 (VDD), U11.N9 (VDD), U11.R1 (VDD), U11.R9 (VDD)
