beagleboard/beaglebone-ai/kicad/beaglebone-ai-rev-a1/ddr2.kicad_sch

## KiCad design kicad/beaglebone-ai-rev-a1/ddr2.kicad_sch (2021-06-15)

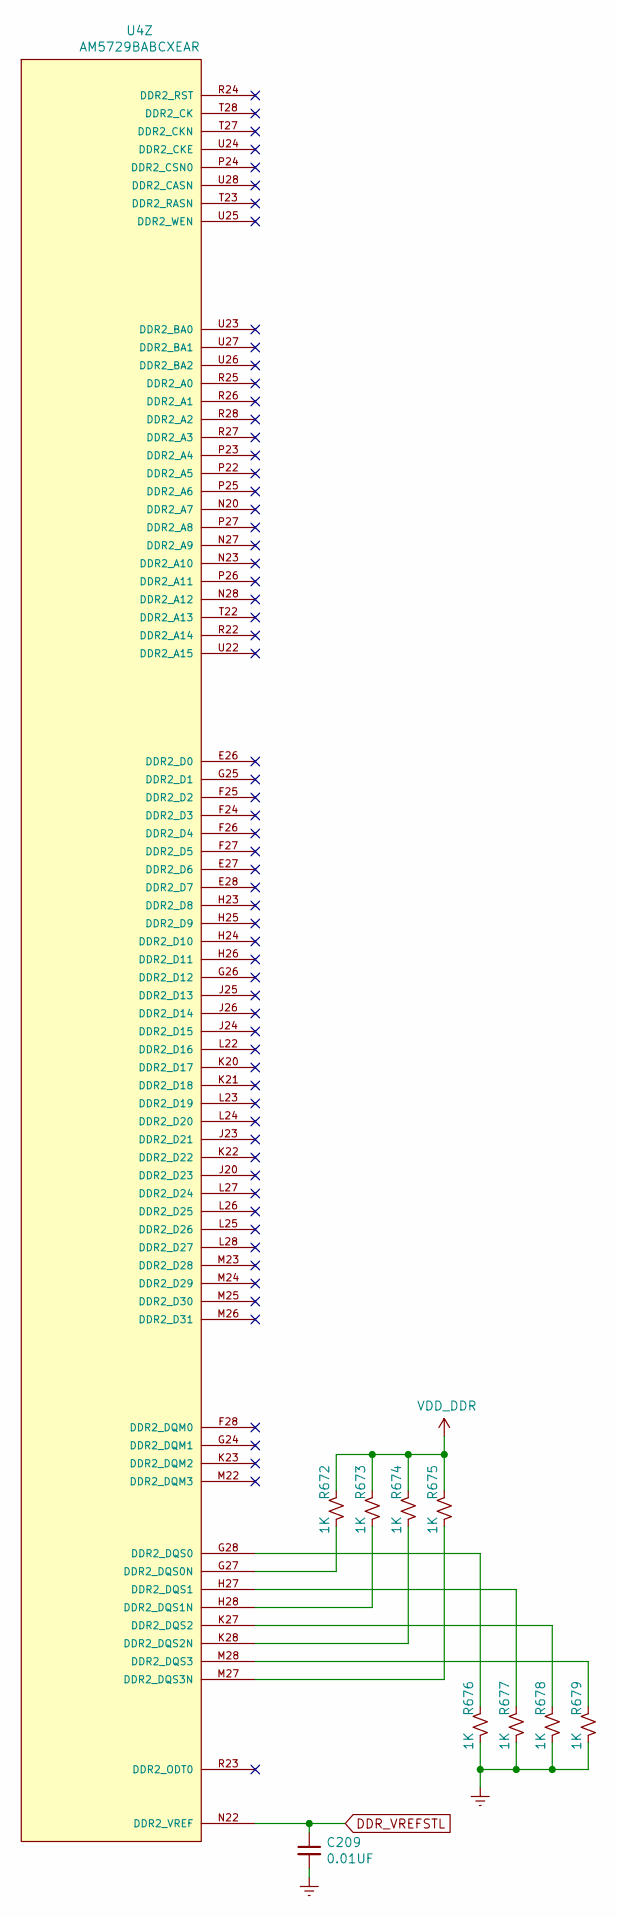
[picture p125: schematic ddr2.kicad_sch]

Parts:
C209: 0.01UF; C0402; Rating X7R,16V; Manufacturer P/N GRM155R71C103KA01D
R672, R673, R674, R675, R676, R677, R678, R679: 1K; R0402; Rating 5%; Manufacturer P/N RC0402JR-071KL
U4: AM5729BABCXEAR; BGA760C80P28X28_2300X2300X255; Manufacturer P/N AM5729BABCXEAR

Connections:
DDR_VREFSTL: C209.1, U4.N22 (DDR2_VREF)
Earth: C209.2, R676.2, R677.2, R678.2, R679.2
unnamed: R672.2, U4.G27 (DDR2_DQS0N)
unnamed: R673.2, U4.H28 (DDR2_DQS1N)
unnamed: R674.2, U4.K28 (DDR2_DQS2N)
unnamed: R675.2, U4.M27 (DDR2_DQS3N)
unnamed: R676.1, U4.G28 (DDR2_DQS0)
unnamed: R677.1, U4.H27 (DDR2_DQS1)
unnamed: R678.1, U4.K27 (DDR2_DQS2)
unnamed: R679.1, U4.M28 (DDR2_DQS3)
VDD_DDR: R672.1, R673.1, R674.1, R675.1
