beagleboard/beaglebone-ai/kicad/beaglebone-ai-rev-a1/ddr_vtt_leds.kicad_sch

## KiCad design kicad/beaglebone-ai-rev-a1/ddr_vtt_leds.kicad_sch (2021-06-15)

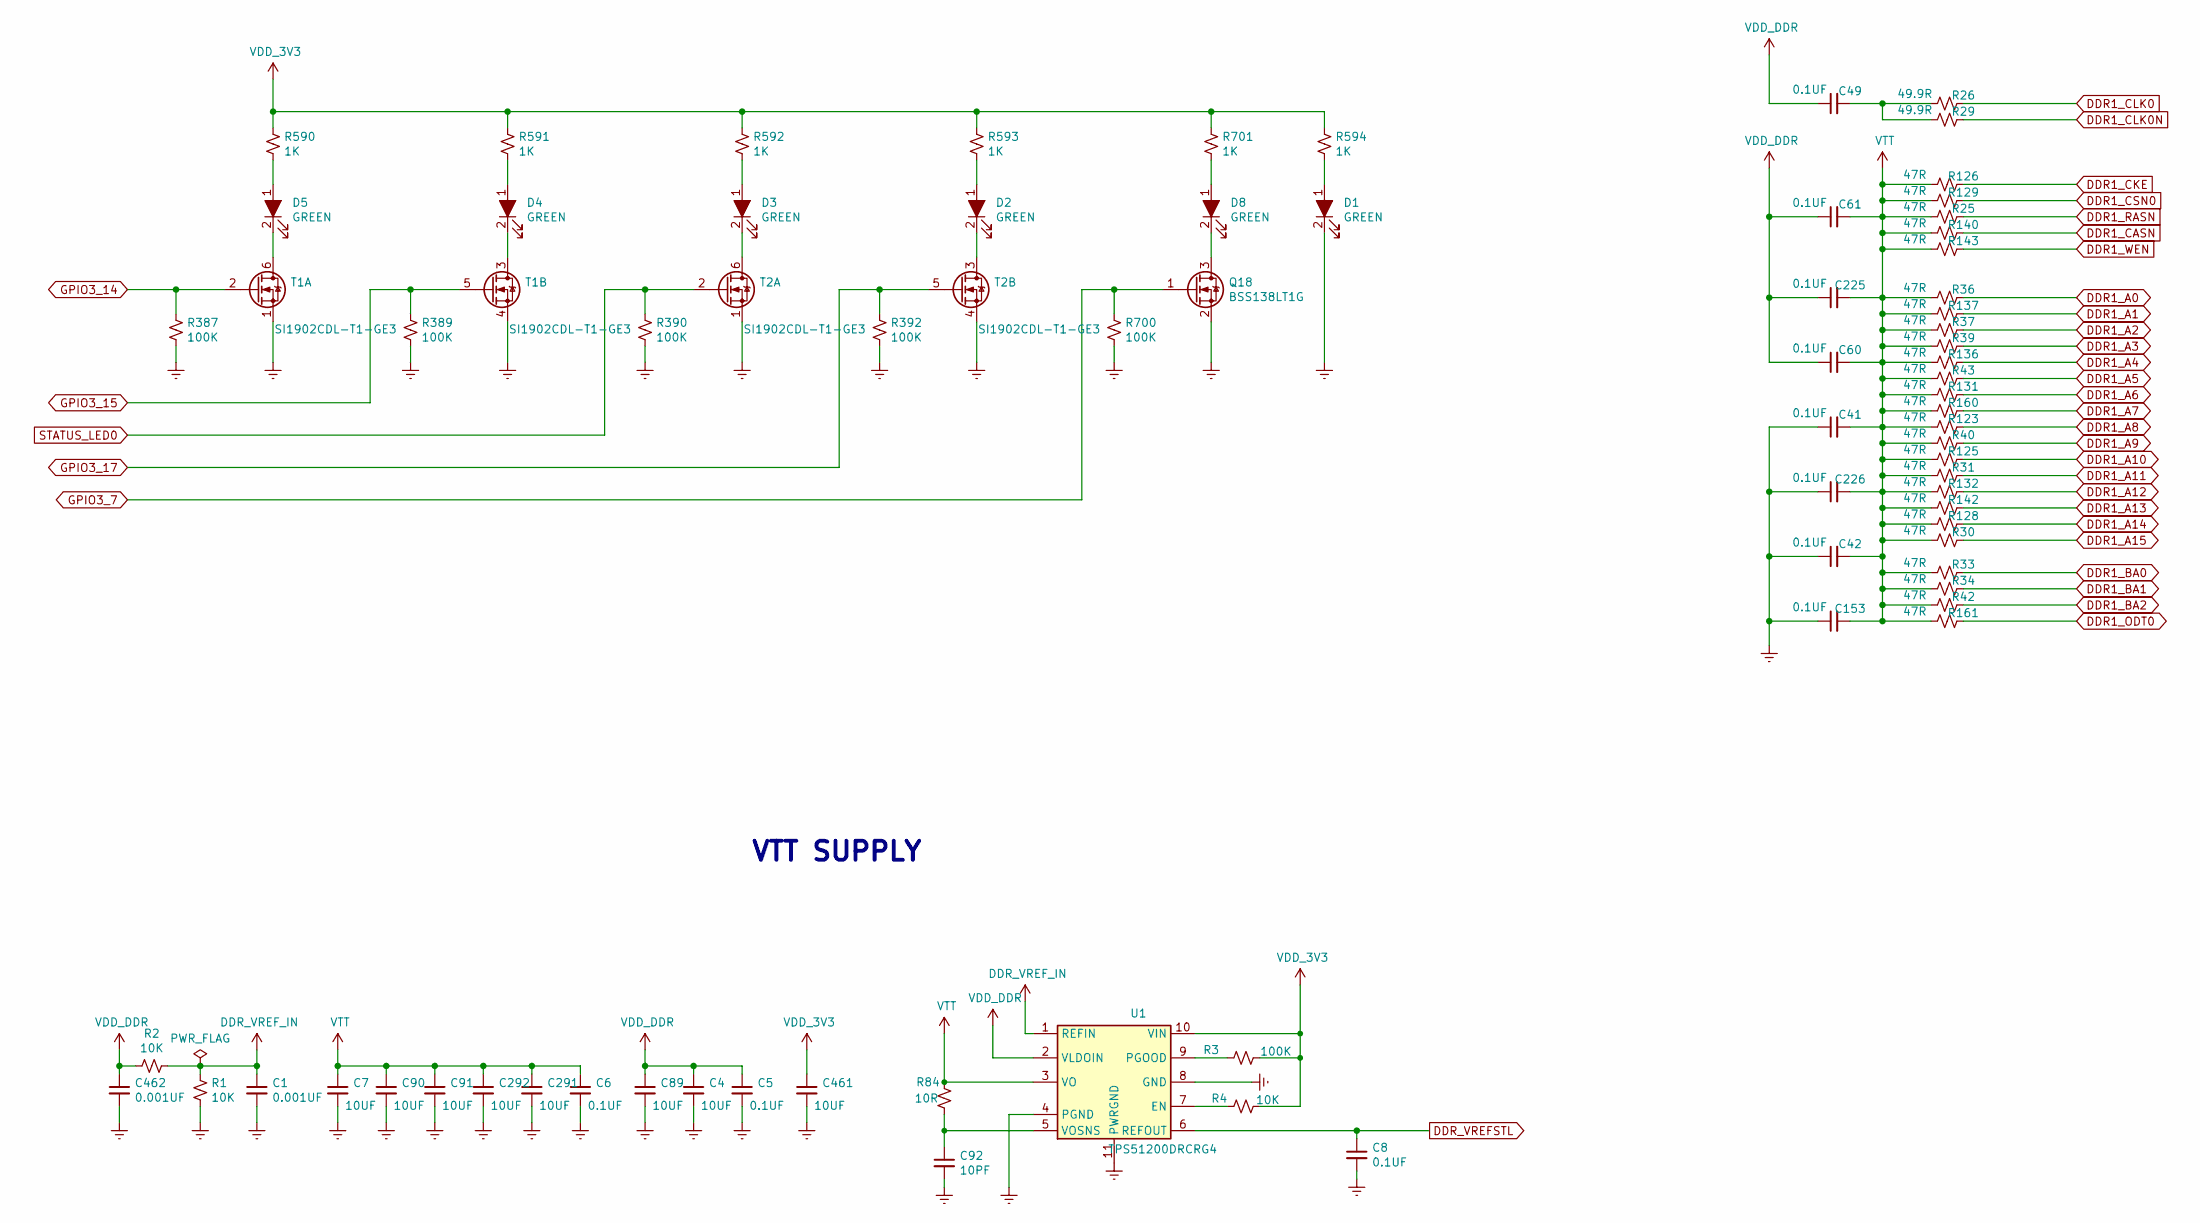
[picture p126: schematic ddr_vtt_leds.kicad_sch]

Parts:
C1, C462: 0.001UF; C0402; Rating 50V,X7R; Manufacturer P/N GRM155R71H102KA01D
C4, C7, C89, C90, C91, C291, C292, C461: 10UF; C0603; Rating 10V,X5R; Manufacturer P/N GRM188R61A106KE69D
C5, C6, C8, C41, C42, C49, C60, C61, C153, C225, C226: 0.1UF; C0402; Rating 16V,X7R; Manufacturer P/N GRM155R71C104KA88D
C92: 10PF; C0402; Rating 50V,C0G; Manufacturer P/N GRM1555C1H100JA01D
D1, D2, D3, D4, D5, D8: GREEN; D0603; Rating 20mA; Manufacturer P/N 19-217/G7C-AN1P2/3T
Q18: BSS138LT1G; SOT-23; Manufacturer P/N BSS138LT1G
R1, R2: 10K; R0402; Rating 1%; Manufacturer P/N RC0402FR-0710KL
R3, R387, R389, R390, R392, R700: 100K; R0402; Rating 5%; Manufacturer P/N RC0402JR-07100KL
R4: 10K; R0402; Rating 5%; Manufacturer P/N RC0402JR-0710KL
R25, R30, R31, R33, R34, R36, R37, R39, R40, R42, R43, R123, R125, R126, R128, R129, R131, R132, R136, R137, R140, R142, R143, R160, R161: 47R; R0402; Rating 1%; Manufacturer P/N RC0402FR-0747RL
R26, R29: 49.9R; R0402; Rating 1%; Manufacturer P/N RC0402FR-0749R9L
R84: 10R; R0402; Rating 1%; Manufacturer P/N RC0402FR-0710RL
R590, R591, R592, R593, R594, R701: 1K; R0402; Rating 5%; Manufacturer P/N RC0402JR-071KL
T1, T2: SI1902CDL-T1-GE3; SOT363_6; Manufacturer P/N Si1902CDL-T1-GE3
U1: TPS51200DRCRG4; VSON-10-1EP_3x3mm_P0.5mm_EP1.65x2.4mm; Manufacturer P/N TPS51200DRCRG4

Connections:
DDR1_A0: R36.2
DDR1_A1: R137.2
DDR1_A2: R37.2
DDR1_A3: R39.2
DDR1_A4: R136.2
DDR1_A5: R43.2
DDR1_A6: R131.2
DDR1_A7: R160.2
DDR1_A8: R123.2
DDR1_A9: R40.2
DDR1_A10: R125.2
DDR1_A11: R31.2
DDR1_A12: R132.2
DDR1_A13: R142.2
DDR1_A14: R128.2
DDR1_A15: R30.2
DDR1_BA0: R33.2
DDR1_BA1: R34.2
DDR1_BA2: R42.2
DDR1_CASN: R140.2
DDR1_CKE: R126.2
DDR1_CLK0: R26.2
DDR1_CLK0N: R29.2
DDR1_CSN0: R129.2
DDR1_ODT0: R161.2
DDR1_RASN: R25.2
DDR1_WEN: R143.2
DDR_VREFSTL: C8.1, U1.6 (REFOUT)
DDR_VREF_IN: C1.1, R1.1, R2.2, U1.1 (REFIN)
Earth: C1.2, C4.2, C5.2, C6.2, C7.2, C8.2, C41.1, C42.1, C89.2, C90.2, C91.2, C92.2, C153.1, C226.1, C291.2, C292.2, C461.2, C462.2, D1.2 (K), Q18.2 (S), R1.2, R387.2, R389.2, R390.2, R392.2, R700.2, T1.1 (S), T1.4 (S), T2.1 (S), T2.4 (S), U1.4 (PGND), U1.8 (GND), U1.11 (PWRGND)
GPIO3_7: Q18.1 (G), R700.1
GPIO3_14: R387.1, T1.2 (G)
GPIO3_15: R389.1, T1.5 (G)
GPIO3_17: R392.1, T2.5 (G)
unnamed: C49.2, R26.1, R29.1
unnamed: C92.1, R84.1, U1.5 (VOSNS)
unnamed: D1.1 (A), R594.2
unnamed: D2.1 (A), R593.2
unnamed: D2.2 (K), T2.3 (D)
unnamed: D3.1 (A), R592.2
unnamed: D3.2 (K), T2.6 (D)
unnamed: D4.1 (A), R591.2
unnamed: D4.2 (K), T1.3 (D)
unnamed: D5.1 (A), R590.2
unnamed: D5.2 (K), T1.6 (D)
unnamed: D8.1 (A), R701.2
unnamed: D8.2 (K), Q18.3 (D)
unnamed: R3.2, U1.9 (PGOOD)
unnamed: R4.2, U1.7 (EN)
STATUS_LED0: R390.1, T2.2 (G)
VDD_3V3: C461.1, R3.1, R4.1, R590.1, R591.1, R592.1, R593.1, R594.1, R701.1, U1.10 (VIN)
VDD_DDR: C4.1, C5.1, C49.1, C60.1, C61.1, C89.1, C225.1, C462.1, R2.1, U1.2 (VLDOIN)
VTT: C6.1, C7.1, C41.2, C42.2, C60.2, C61.2, C90.1, C91.1, C153.2, C225.2, C226.2, C291.1, C292.1, R25.1, R30.1, R31.1, R33.1, R34.1, R36.1, R37.1, R39.1, R40.1, R42.1, R43.1, R84.2, R123.1, R125.1, R126.1, R128.1, R129.1, R131.1, R132.1, R136.1, R137.1, R140.1, R142.1, R143.1, R160.1, R161.1, U1.3 (VO)

Notes on the sheet:
VTT SUPPLY
