beagleboard/beaglebone-ai/kicad/beaglebone-ai-rev-a1/ethernet.kicad_sch

## KiCad design kicad/beaglebone-ai-rev-a1/ethernet.kicad_sch (2021-06-15)

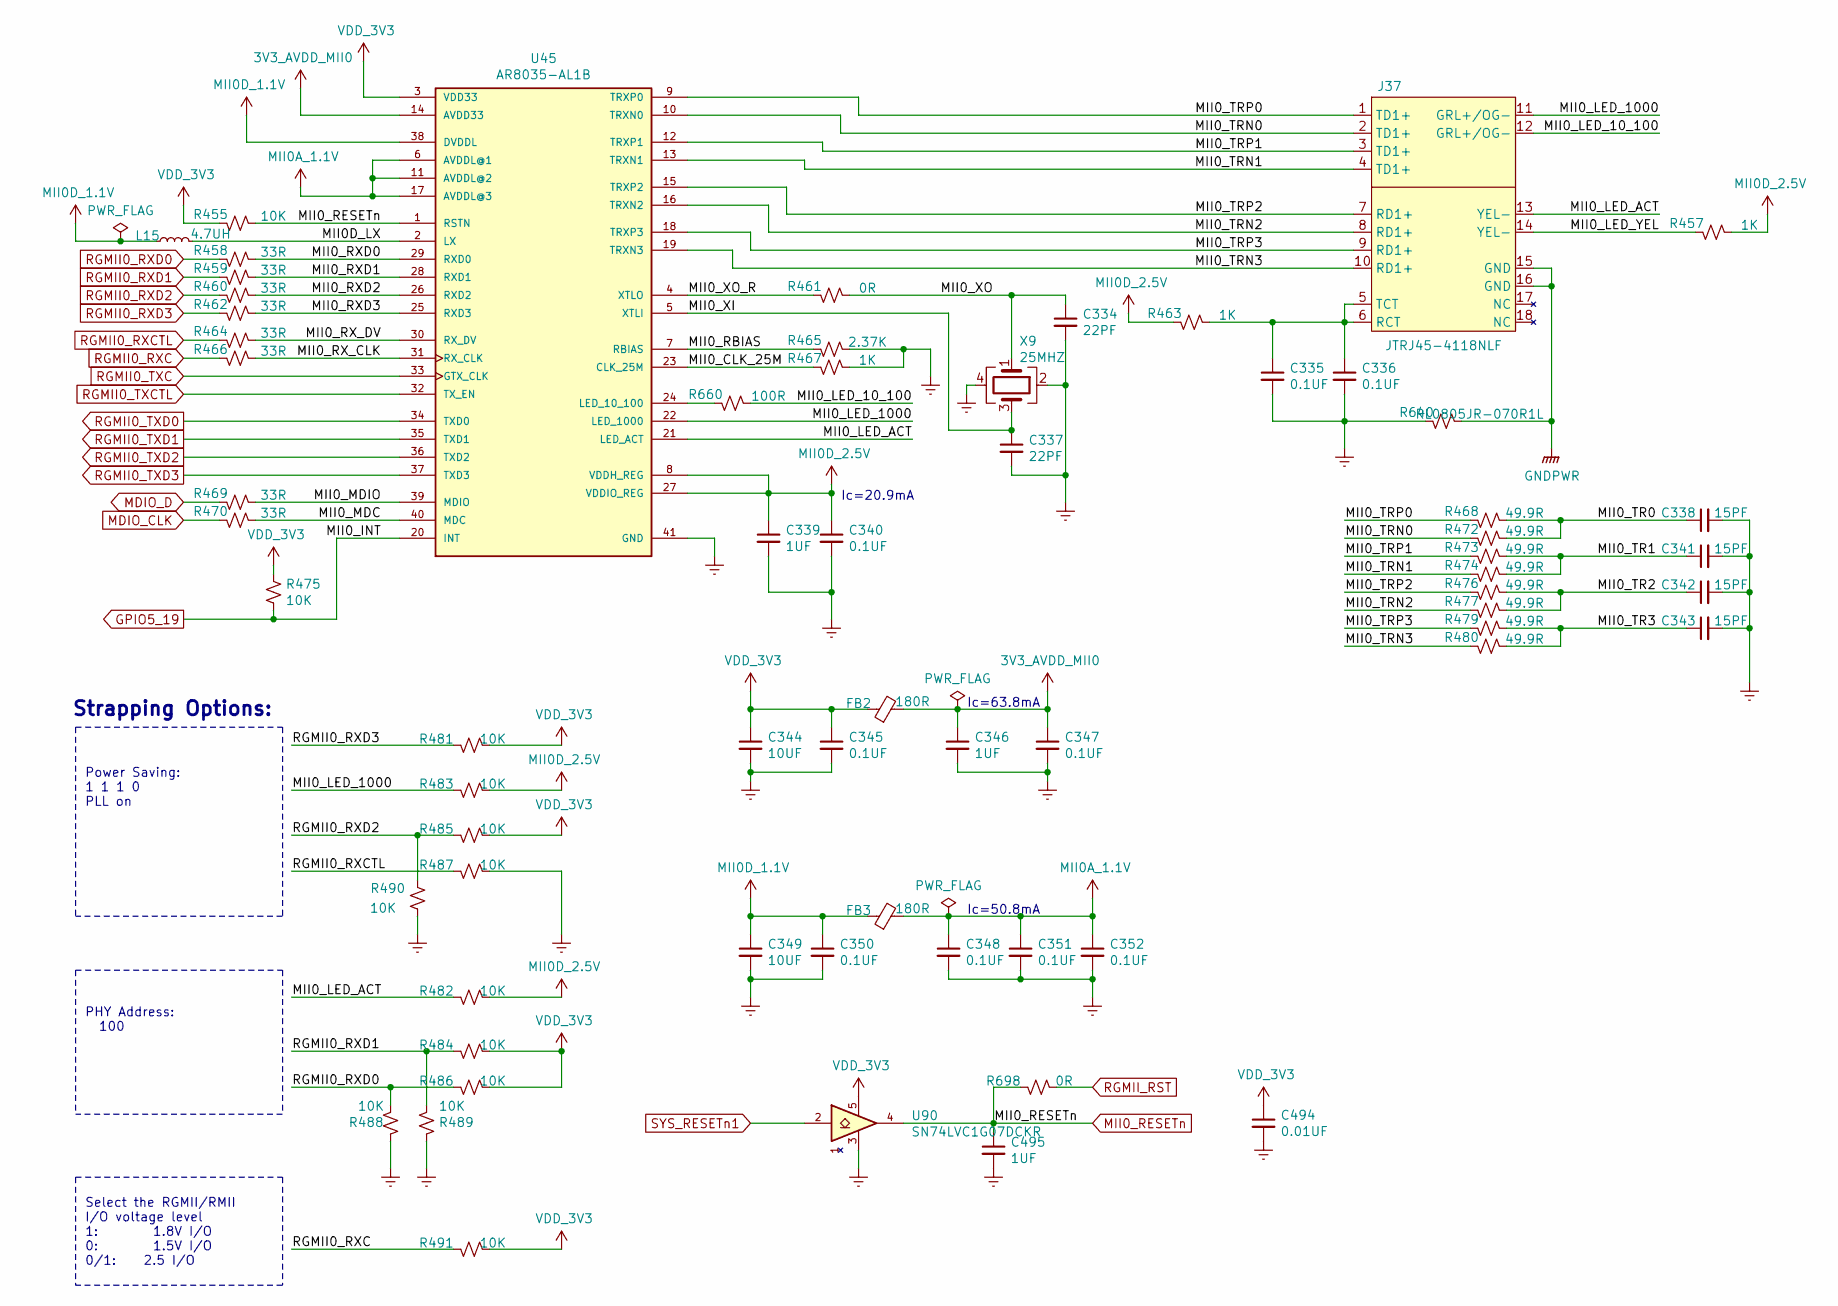
[picture p127: schematic ethernet.kicad_sch]

Parts:
C334, C337: 22PF; C0402; Rating 50V,C0G; Manufacturer P/N GRM1555C1H220JA01D
C335, C336, C340, C345, C347, C348, C350, C351, C352: 0.1UF; C0402; Rating 16V,X7R; Manufacturer P/N GRM155R71C104KA88D
C338, C341, C342, C343: 15PF; C0402; Rating 50V,C0G; Manufacturer P/N GRM1555C1H150GA01D
C339, C346, C495: 1UF; C0402; Rating 10V,X5R; Manufacturer P/N GRM155R61A105KE15D
C344, C349: 10UF; C0603; Rating 10V,X5R; Manufacturer P/N GRM188R61A106KE69D
C494: 0.01UF; C0402; Rating X7R,16V; Manufacturer P/N GRM155R71C103KA01D
FB2, FB3: 180R; L0603; Rating 1500mA; Manufacturer P/N BLM18PG181SN1D
J37: JTRJ45-4118NLF; RJ45_MTCONN_JTRJ45-4118NLF; Manufacturer P/N Connector,RJ45 Jack with integrated mag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
L15: 4.7UH; L30X30_A; Manufacturer P/N Power Inductor,Magnetic shielded,4.7uH,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
R455, R475, R481, R482, R483, R484, R485, R486, R487, R488, R489, R490, R491: 10K; R0402; Rating 1%; Manufacturer P/N RC0402FR-0710KL
R457, R463, R467: 1K; R0402; Rating 1%; Manufacturer P/N RC0402FR-071KL
R458, R459, R460, R462, R464, R466, R469, R470: 33R; R0402; Rating 5%; Manufacturer P/N RC0402JR-0733RL
R461, R698: 0R; R0402; Rating 5%; Manufacturer P/N RC0402JR-070RL
R465: 2.37K; R0402; Rating 1%; Manufacturer P/N RC0402FR-072K37L
R468, R472, R473, R474, R476, R477, R479, R480: 49.9R; R0402; Rating 1%; Manufacturer P/N RC0402FR-0749R9L
R640: RL0805JR-070R1L; R0805; Rating 5%; Manufacturer P/N RL0805JR-070R1L
R660: 100R; R0402; Rating 5%; Manufacturer P/N RC0402JR-07100RL
U45: AR8035-AL1B; QFN40P500X500X75-41N; Manufacturer P/N AR8035-AL1B
U90: SN74LVC1G07DCKR; SC70_5; Manufacturer P/N SN74LVC1G07DCKR
X9: 25MHZ; OSCCC250X200X60-4N; Rating 20PPM; Manufacturer P/N 5ZAA25000202TFA0Q3

Connections:
3V3_AVDD_MII0: C346.1, C347.1, FB2.2, U45.14 (AVDD33)
Earth: C334.2, C335.2, C336.2, C337.2, C338.2, C339.2, C340.2, C341.2, C342.2, C343.2, C344.2, C345.2, C346.2, C347.2, C348.2, C349.2, C350.2, C351.2, C352.2, C494.2, C495.2, R465.2, R467.2, R487.2, R488.1, R489.1, R490.1, R640.1, U45.41 (GND), U90.3 (GND), X9.2, X9.4
GNDPWR: J37.15 (GND), J37.16 (GND), R640.2
GPIO5_19: R475.2, U45.20 (INT)
MDIO_CLK: R470.1
MDIO_D: R469.1
MII0A_1.1V: C348.1, C351.1, C352.1, FB3.2, U45.6 (AVDDL@1), U45.11 (AVDDL@2), U45.17 (AVDDL@3)
MII0D_1.1V: C349.1, C350.1, FB3.1, L15.1, U45.38 (DVDDL)
MII0D_2.5V: C339.1, C340.1, R457.2, R463.1, R482.2, R483.2, U45.8 (VDDH_REG), U45.27 (VDDIO_REG)
MII0D_LX: L15.2, U45.2 (LX)
MII0_CLK_25M: R467.1, U45.23 (CLK_25M)
MII0_LED_10_100: J37.12 (GRL+/OG-), R660.2
MII0_LED_1000: J37.11 (GRL+/OG-), R483.1, U45.22 (LED_1000)
MII0_LED_ACT: J37.13 (YEL-), R482.1, U45.21 (LED_ACT)
MII0_LED_YEL: J37.14 (YEL-), R457.1
MII0_MDC: R470.2, U45.40 (MDC)
MII0_MDIO: R469.2, U45.39 (MDIO)
MII0_RBIAS: R465.1, U45.7 (RBIAS)
MII0_RESETn: C495.1, R455.2, R698.1, U45.1 (RSTN), U90.4
MII0_RXD0: R458.2, U45.29 (RXD0)
MII0_RXD1: R459.2, U45.28 (RXD1)
MII0_RXD2: R460.2, U45.26 (RXD2)
MII0_RXD3: R462.2, U45.25 (RXD3)
MII0_RX_CLK: R466.2, U45.31 (RX_CLK)
MII0_RX_DV: R464.2, U45.30 (RX_DV)
MII0_TR0: C338.1, R468.2, R472.2
MII0_TR1: C341.1, R473.2, R474.2
MII0_TR2: C342.1, R476.2, R477.2
MII0_TR3: C343.1, R479.2, R480.2
MII0_TRN0: J37.2 (TD1+), R472.1, U45.10 (TRXN0)
MII0_TRN1: J37.4 (TD1+), R474.1, U45.13 (TRXN1)
MII0_TRN2: J37.8 (RD1+), R477.1, U45.16 (TRXN2)
MII0_TRN3: J37.10 (RD1+), R480.1, U45.19 (TRXN3)
MII0_TRP0: J37.1 (TD1+), R468.1, U45.9 (TRXP0)
MII0_TRP1: J37.3 (TD1+), R473.1, U45.12 (TRXP1)
MII0_TRP2: J37.7 (RD1+), R476.1, U45.15 (TRXP2)
MII0_TRP3: J37.9 (RD1+), R479.1, U45.18 (TRXP3)
MII0_XI: C337.1, U45.5 (XTLI), X9.3
MII0_XO: C334.1, R461.2, X9.1
MII0_XO_R: R461.1, U45.4 (XTLO)
unnamed: C335.1, C336.1, J37.5 (TCT), J37.6 (RCT), R463.2
unnamed: R660.1, U45.24 (LED_10_100)
RGMII0_RXC: R466.1, R491.1
RGMII0_RXCTL: R464.1, R487.1
RGMII0_RXD0: R458.1, R486.1, R488.2
RGMII0_RXD1: R459.1, R484.1, R489.2
RGMII0_RXD2: R460.1, R485.1, R490.2
RGMII0_RXD3: R462.1, R481.1
RGMII0_TXC: U45.33 (GTX_CLK)
RGMII0_TXCTL: U45.32 (TX_EN)
RGMII0_TXD0: U45.34 (TXD0)
RGMII0_TXD1: U45.35 (TXD1)
RGMII0_TXD2: U45.36 (TXD2)
RGMII0_TXD3: U45.37 (TXD3)
RGMII_RST: R698.2
SYS_RESETn1: U90.2
VDD_3V3: C344.1, C345.1, C494.1, FB2.1, R455.1, R475.1, R481.2, R484.2, R485.2, R486.2, R491.2, U45.3 (VDD33), U90.5 (VCC)

Notes on the sheet:
Power Saving: 1 1 1 0 PLL on
PHY Address: 100
Select the RGMII/RMII I/O voltage level 1: 1.8V I/O 0: 1.5V I/O 0/1: 2.5 I/O
Strapping Options:
Ic=20.9mA
Ic=63.8mA
Ic=50.8mA
