beagleboard/beaglebone-ai/kicad/beaglebone-ai-rev-a1/expconn.kicad_sch

## KiCad design kicad/beaglebone-ai-rev-a1/expconn.kicad_sch (2021-06-15)

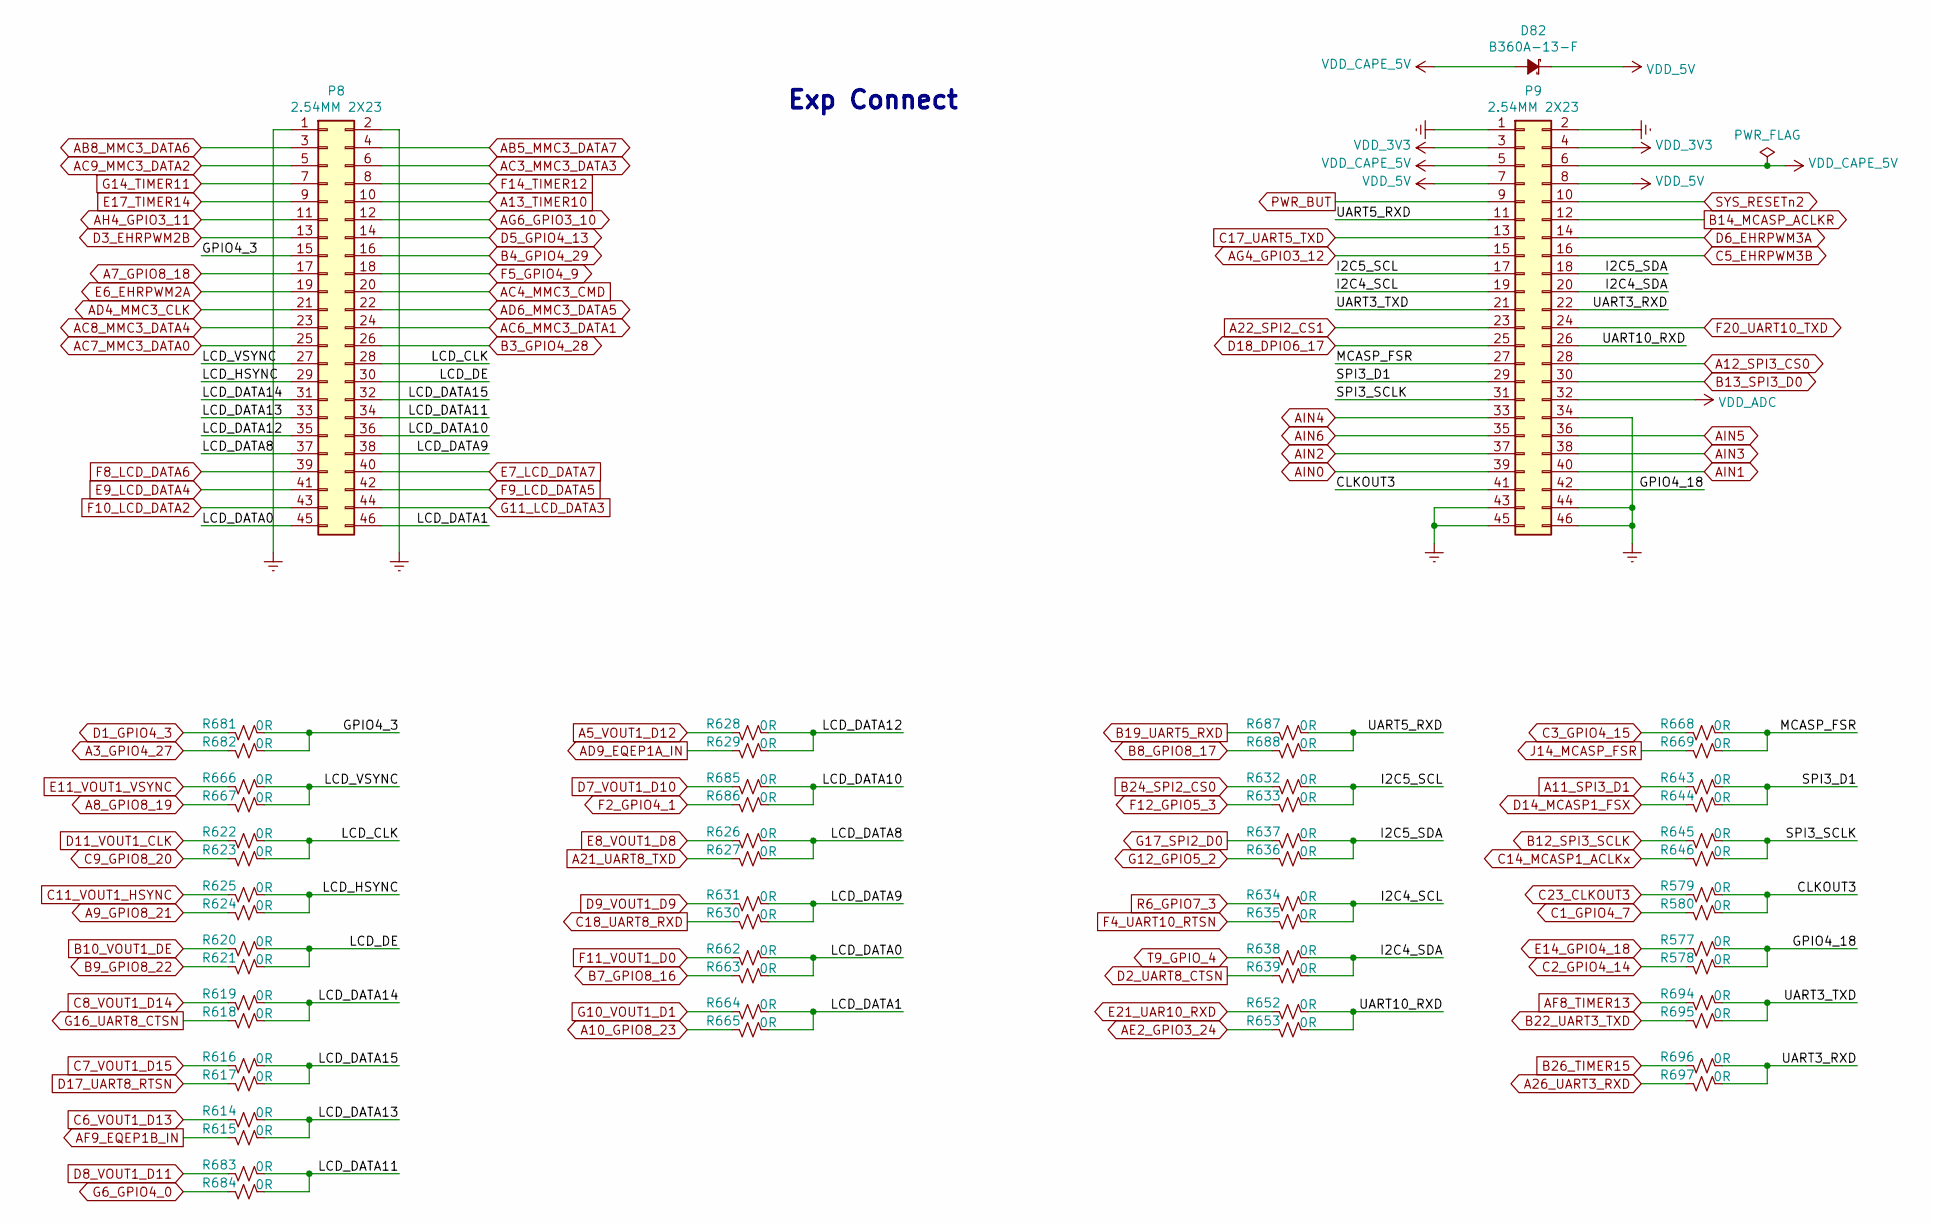
[picture p128: schematic expconn.kicad_sch]

Parts:
D82: B360A-13-F; D_SMA; Manufacturer P/N B360A-13-F
P8, P9: 2.54MM 2X23; H2X23MZ; Manufacturer P/N JT254F-D180-850-223-001-G
R577, R578, R579, R580, R614, R615, R616, R617, R618, R619, R620, R621, R622, R623, R624, R625, R626, R627, R628, R629, R630, R631, R632, R633, R634, R635, R636, R637, R638, R639, R643, R644, R645, R646, R652, R653, R662, R663, R664, R665, R666, R667, R668, R669, R681, R682, R683, R684, R685, R686, R687, R688, R694, R695, R696, R697: 0R; R0402; Rating 5%; Manufacturer P/N RC0402JR-070RL

Connections:
A3_GPIO4_27: R682.1
A5_VOUT1_D12: R628.1
A7_GPIO8_18: P8.17
A8_GPIO8_19: R667.1
A9_GPIO8_21: R624.1
A10_GPIO8_23: R665.1
A11_SPI3_D1: R643.1
A12_SPI3_CS0: P9.28
A13_TIMER10: P8.10
A21_UART8_TXD: R627.1
A22_SPI2_CS1: P9.23
A26_UART3_RXD: R697.1
AB5_MMC3_DATA7: P8.4
AB8_MMC3_DATA6: P8.3
AC3_MMC3_DATA3: P8.6
AC4_MMC3_CMD: P8.20
AC6_MMC3_DATA1: P8.24
AC7_MMC3_DATA0: P8.25
AC8_MMC3_DATA4: P8.23
AC9_MMC3_DATA2: P8.5
AD4_MMC3_CLK: P8.21
AD6_MMC3_DATA5: P8.22
AD9_EQEP1A_IN: R629.1
AE2_GPIO3_24: R653.1
AF8_TIMER13: R694.1
AF9_EQEP1B_IN: R615.1
AG4_GPIO3_12: P9.15
AG6_GPIO3_10: P8.12
AH4_GPIO3_11: P8.11
AIN0: P9.39
AIN1: P9.40
AIN2: P9.37
AIN3: P9.38
AIN4: P9.33
AIN5: P9.36
AIN6: P9.35
B3_GPIO4_28: P8.26
B4_GPIO4_29: P8.16
B7_GPIO8_16: R663.1
B8_GPIO8_17: R688.1
B9_GPIO8_22: R621.1
B10_VOUT1_DE: R620.1
B12_SPI3_SCLK: R645.1
B13_SPI3_D0: P9.30
B14_MCASP_ACLKR: P9.12
B19_UART5_RXD: R687.1
B22_UART3_TXD: R695.1
B24_SPI2_CS0: R632.1
B26_TIMER15: R696.1
C1_GPIO4_7: R580.1
C2_GPIO4_14: R578.1
C3_GPIO4_15: R668.1
C5_EHRPWM3B: P9.16
C6_VOUT1_D13: R614.1
C7_VOUT1_D15: R616.1
C8_VOUT1_D14: R619.1
C9_GPIO8_20: R623.1
C11_VOUT1_HSYNC: R625.1
C14_MCASP1_ACLKx: R646.1
C17_UART5_TXD: P9.13
C18_UART8_RXD: R630.1
C23_CLKOUT3: R579.1
CLKOUT3: P9.41, R579.2, R580.2
D1_GPIO4_3: R681.1
D2_UART8_CTSN: R639.1
D3_EHRPWM2B: P8.13
D5_GPIO4_13: P8.14
D6_EHRPWM3A: P9.14
D7_VOUT1_D10: R685.1
D8_VOUT1_D11: R683.1
D9_VOUT1_D9: R631.1
D11_VOUT1_CLK: R622.1
D14_MCASP1_FSX: R644.1
D17_UART8_RTSN: R617.1
D18_DPIO6_17: P9.25
E6_EHRPWM2A: P8.19
E7_LCD_DATA7: P8.40
E8_VOUT1_D8: R626.1
E9_LCD_DATA4: P8.41
E11_VOUT1_VSYNC: R666.1
E14_GPIO4_18: R577.1
E17_TIMER14: P8.9
E21_UAR10_RXD: R652.1
Earth: P8.1, P8.2, P9.1, P9.2, P9.34, P9.43, P9.44, P9.45, P9.46
F2_GPIO4_1: R686.1
F4_UART10_RTSN: R635.1
F5_GPIO4_9: P8.18
F8_LCD_DATA6: P8.39
F9_LCD_DATA5: P8.42
F10_LCD_DATA2: P8.43
F11_VOUT1_D0: R662.1
F12_GPIO5_3: R633.1
F14_TIMER12: P8.8
F20_UART10_TXD: P9.24
G6_GPIO4_0: R684.1
G10_VOUT1_D1: R664.1
G11_LCD_DATA3: P8.44
G12_GPIO5_2: R636.1
G14_TIMER11: P8.7
G16_UART8_CTSN: R618.1
G17_SPI2_D0: R637.1
GPIO4_3: P8.15, R681.2, R682.2
GPIO4_18: P9.42, R577.2, R578.2
I2C4_SCL: P9.19, R634.2, R635.2
I2C4_SDA: P9.20, R638.2, R639.2
I2C5_SCL: P9.17, R632.2, R633.2
I2C5_SDA: P9.18, R636.2, R637.2
J14_MCASP_FSR: R669.1
LCD_CLK: P8.28, R622.2, R623.2
LCD_DATA0: P8.45, R662.2, R663.2
LCD_DATA1: P8.46, R664.2, R665.2
LCD_DATA8: P8.37, R626.2, R627.2
LCD_DATA9: P8.38, R630.2, R631.2
LCD_DATA10: P8.36, R685.2, R686.2
LCD_DATA11: P8.34, R683.2, R684.2
LCD_DATA12: P8.35, R628.2, R629.2
LCD_DATA13: P8.33, R614.2, R615.2
LCD_DATA14: P8.31, R618.2, R619.2
LCD_DATA15: P8.32, R616.2, R617.2
LCD_DE: P8.30, R620.2, R621.2
LCD_HSYNC: P8.29, R624.2, R625.2
LCD_VSYNC: P8.27, R666.2, R667.2
MCASP_FSR: P9.27, R668.2, R669.2
PWR_BUT: P9.9
R6_GPIO7_3: R634.1
SPI3_D1: P9.29, R643.2, R644.2
SPI3_SCLK: P9.31, R645.2, R646.2
SYS_RESETn2: P9.10
T9_GPIO_4: R638.1
UART3_RXD: P9.22, R696.2, R697.2
UART3_TXD: P9.21, R694.2, R695.2
UART5_RXD: P9.11, R687.2, R688.2
UART10_RXD: P9.26, R652.2, R653.2
VDD_3V3: P9.3, P9.4
VDD_5V: D82.2 (K), P9.7, P9.8
VDD_ADC: P9.32
VDD_CAPE_5V: D82.1 (A), P9.5, P9.6

Notes on the sheet:
Exp Connect
