beagleboard/beaglebone-ai/kicad/beaglebone-ai-rev-a1/hdmi.kicad_sch

## KiCad design kicad/beaglebone-ai-rev-a1/hdmi.kicad_sch (2021-06-15)

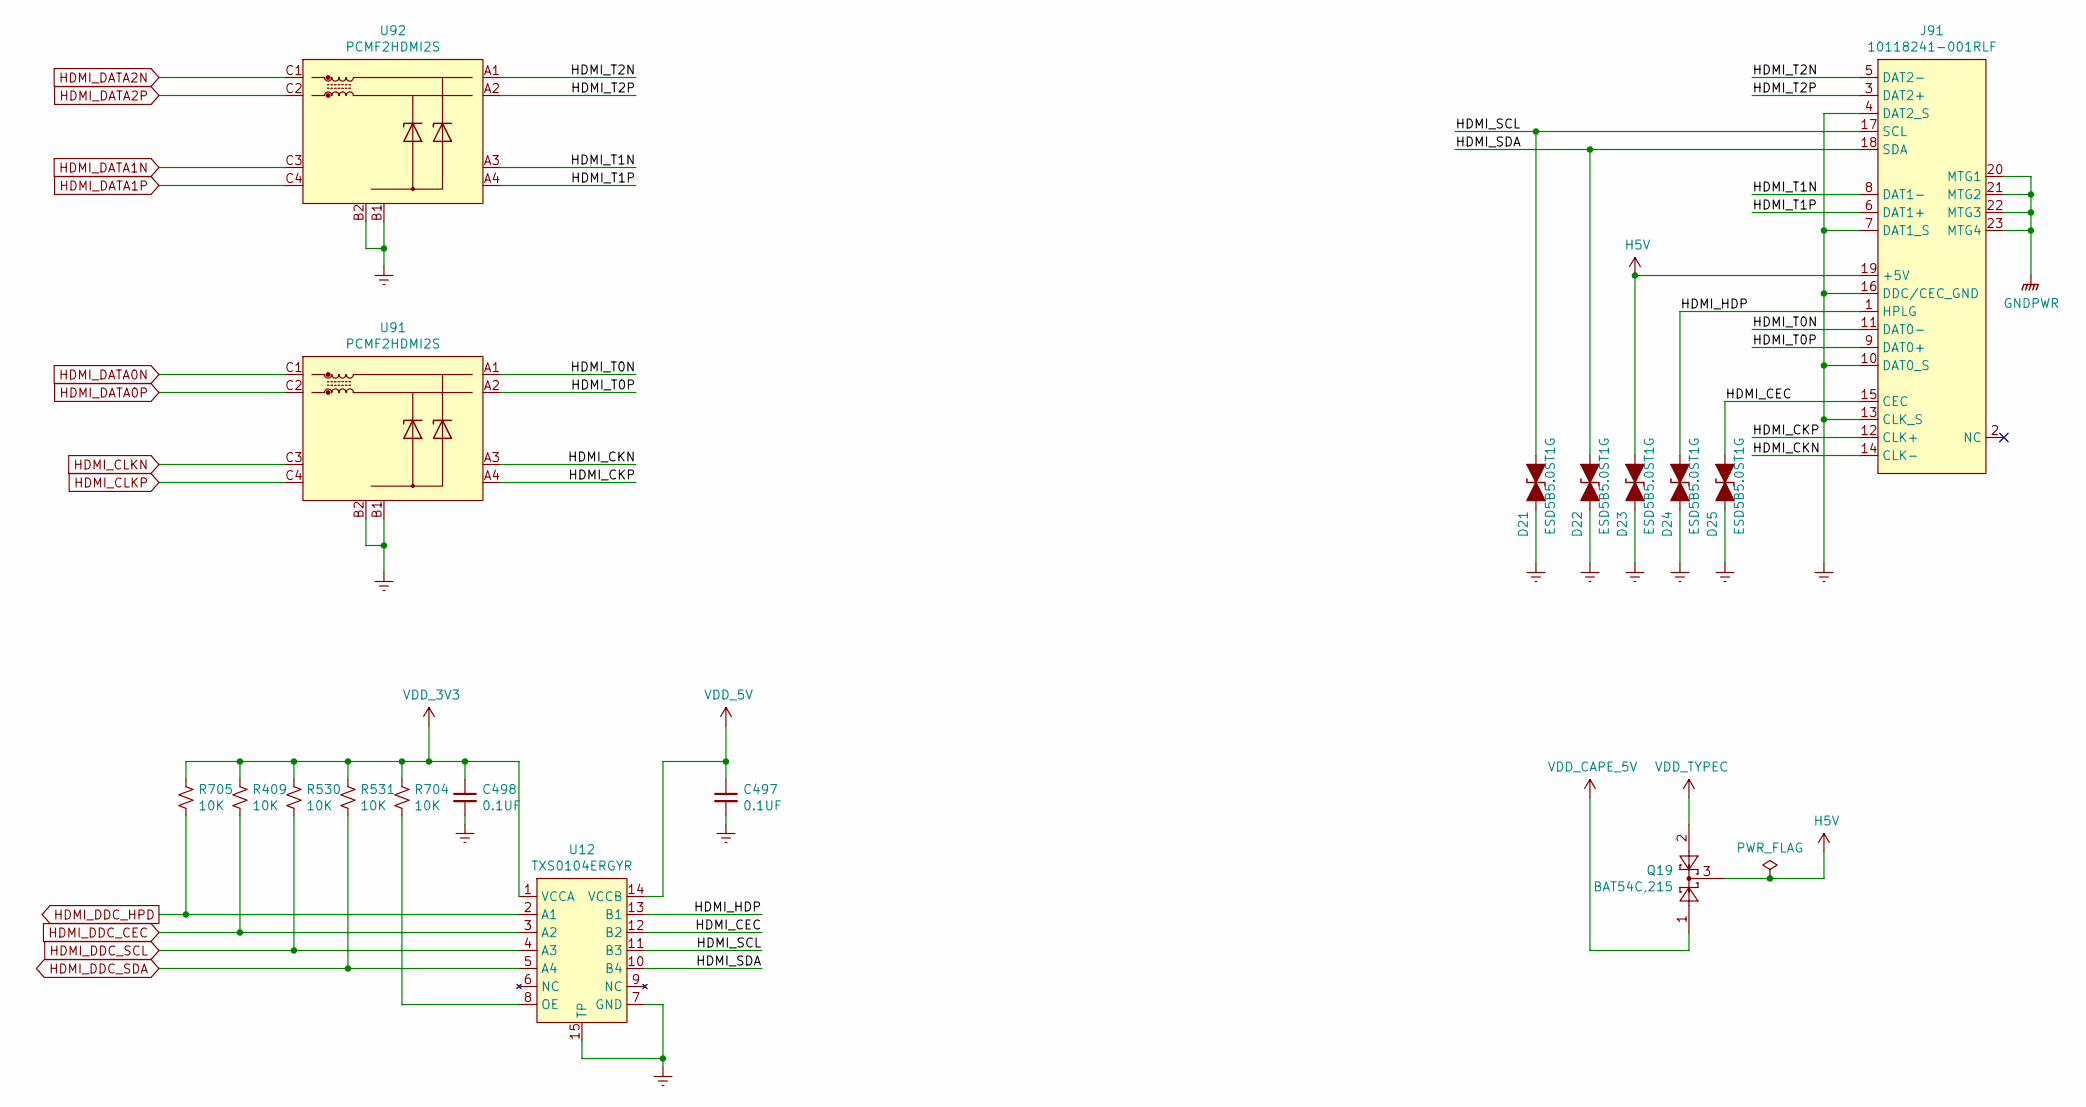
[picture p129: schematic hdmi.kicad_sch]

Parts:
C497, C498: 0.1UF; C0402; Rating 16V,X7R; Manufacturer P/N GRM155R71C104KA88D
D21, D22, D23, D24, D25: ESD5B5.0ST1G; SODFL1608X70N; Manufacturer P/N ESD5B5.0ST1G
J91: 10118241-001RLF; HDMIS19_4P4; Manufacturer P/N Connector,HDMI Receptacle, Type D, Righ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
Q19: BAT54C,215; SOT-23; Manufacturer P/N BAT54C,215
R409, R530, R531, R704, R705: 10K; R0402; Rating 1%; Manufacturer P/N RC0402FR-0710KL
U12: TXS0104ERGYR; QFN50P350X350X100-15N; Manufacturer P/N TXS0104ERGYR
U91, U92: PCMF2HDMI2S; WLCSP10C40P3X4_117X157X60N; Manufacturer P/N PCMF2HDMI2S

Connections:
Earth: C497.2, C498.2, D21.1 (A1), D22.1 (A1), D23.1 (A1), D24.1 (A1), D25.1 (A1), J91.4 (DAT2_S), J91.7 (DAT1_S), J91.10 (DAT0_S), J91.13 (CLK_S), J91.16 (DDC/CEC_GND), U12.7 (GND), U12.15 (TP), U91.B1 (GND_CH1), U91.B2 (GND_CH2), U92.B1 (GND_CH1), U92.B2 (GND_CH2)
GNDPWR: J91.20 (MTG1), J91.21 (MTG2), J91.22 (MTG3), J91.23 (MTG4)
H5V: D23.2 (A2), J91.19 (+5V), Q19.3
HDMI_CEC: D25.2 (A2), J91.15 (CEC), U12.12 (B2)
HDMI_CKN: J91.14 (CLK-), U91.A3 (CH1_OUT-)
HDMI_CKP: J91.12 (CLK+), U91.A4 (CH1_OUT+)
HDMI_CLKN: U91.C3 (CH1_IN-)
HDMI_CLKP: U91.C4 (CH1_IN+)
HDMI_DATA0N: U91.C1 (CH2_IN-)
HDMI_DATA0P: U91.C2 (CH2_IN+)
HDMI_DATA1N: U92.C3 (CH1_IN-)
HDMI_DATA1P: U92.C4 (CH1_IN+)
HDMI_DATA2N: U92.C1 (CH2_IN-)
HDMI_DATA2P: U92.C2 (CH2_IN+)
HDMI_DDC_CEC: R409.2, U12.3 (A2)
HDMI_DDC_HPD: R705.2, U12.2 (A1)
HDMI_DDC_SCL: R530.2, U12.4 (A3)
HDMI_DDC_SDA: R531.2, U12.5 (A4)
HDMI_HDP: D24.2 (A2), J91.1 (HPLG), U12.13 (B1)
HDMI_SCL: D21.2 (A2), J91.17 (SCL), U12.11 (B3)
HDMI_SDA: D22.2 (A2), J91.18 (SDA), U12.10 (B4)
HDMI_T0N: J91.11 (DAT0-), U91.A1 (CH2_OUT-)
HDMI_T0P: J91.9 (DAT0+), U91.A2 (CH2_OUT+)
HDMI_T1N: J91.8 (DAT1-), U92.A3 (CH1_OUT-)
HDMI_T1P: J91.6 (DAT1+), U92.A4 (CH1_OUT+)
HDMI_T2N: J91.5 (DAT2-), U92.A1 (CH2_OUT-)
HDMI_T2P: J91.3 (DAT2+), U92.A2 (CH2_OUT+)
unnamed: R704.2, U12.8 (OE)
VDD_3V3: C498.1, R409.1, R530.1, R531.1, R704.1, R705.1, U12.1 (VCCA)
VDD_5V: C497.1, U12.14 (VCCB)
VDD_CAPE_5V: Q19.1
VDD_TYPEC: Q19.2
