beagleboard/beaglebone-ai/kicad/beaglebone-ai-rev-a1/interface1.kicad_sch

## KiCad design kicad/beaglebone-ai-rev-a1/interface1.kicad_sch (2021-06-15)

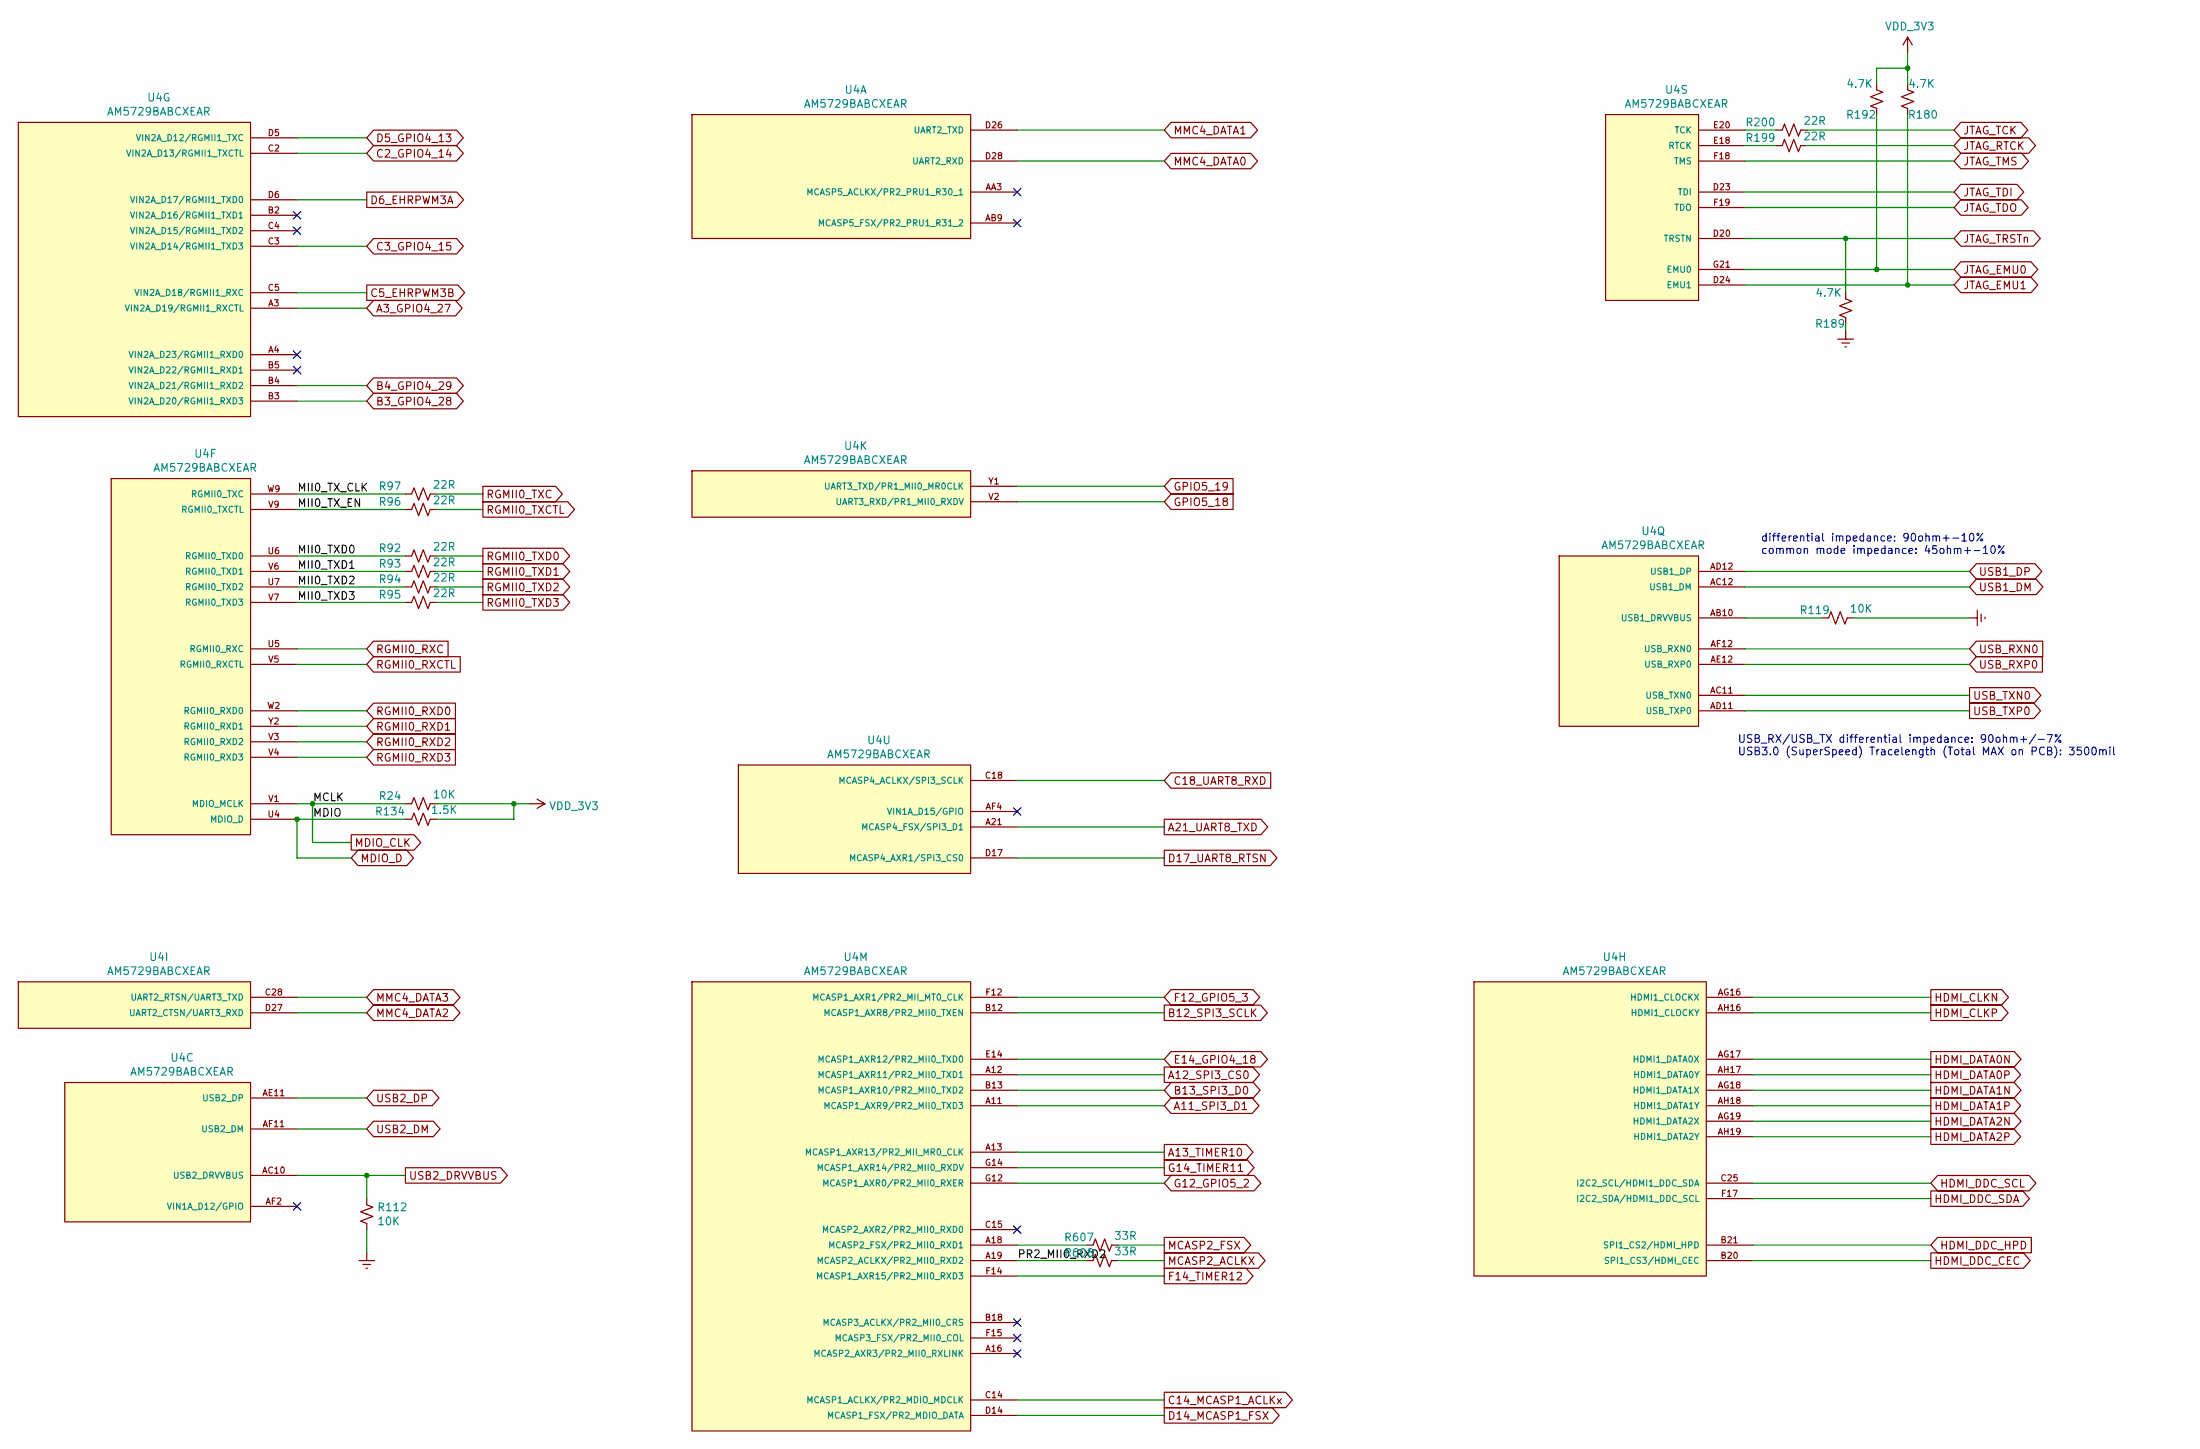
[picture p130: schematic interface1.kicad_sch]

Parts:
R24, R112, R119: 10K; R0402; Rating 5%; Manufacturer P/N RC0402JR-0710KL
R92, R93, R94, R95, R96, R97, R199, R200: 22R; R0402; Rating 5%; Manufacturer P/N RC0402JR-0722RL
R134: 1.5K; R0402; Rating 5%; Manufacturer P/N RC0402JR-071K5L
R180, R189, R192: 4.7K; R0402; Rating 5%; Manufacturer P/N RC0402JR-074K7L
R607, R608: 33R; R0402; Rating 5%; Manufacturer P/N RC0402JR-0733RL
U4: AM5729BABCXEAR; BGA760C80P28X28_2300X2300X255; Manufacturer P/N AM5729BABCXEAR

Connections:
A3_GPIO4_27: U4.A3 (VIN2A_D19/RGMII1_RXCTL)
A11_SPI3_D1: U4.A11 (MCASP1_AXR9/PR2_MII0_TXD3)
A12_SPI3_CS0: U4.A12 (MCASP1_AXR11/PR2_MII0_TXD1)
A13_TIMER10: U4.A13 (MCASP1_AXR13/PR2_MII_MR0_CLK)
A21_UART8_TXD: U4.A21 (MCASP4_FSX/SPI3_D1)
B3_GPIO4_28: U4.B3 (VIN2A_D20/RGMII1_RXD3)
B4_GPIO4_29: U4.B4 (VIN2A_D21/RGMII1_RXD2)
B12_SPI3_SCLK: U4.B12 (MCASP1_AXR8/PR2_MII0_TXEN)
B13_SPI3_D0: U4.B13 (MCASP1_AXR10/PR2_MII0_TXD2)
C2_GPIO4_14: U4.C2 (VIN2A_D13/RGMII1_TXCTL)
C3_GPIO4_15: U4.C3 (VIN2A_D14/RGMII1_TXD3)
C5_EHRPWM3B: U4.C5 (VIN2A_D18/RGMII1_RXC)
C14_MCASP1_ACLKx: U4.C14 (MCASP1_ACLKX/PR2_MDIO_MDCLK)
C18_UART8_RXD: U4.C18 (MCASP4_ACLKX/SPI3_SCLK)
D5_GPIO4_13: U4.D5 (VIN2A_D12/RGMII1_TXC)
D6_EHRPWM3A: U4.D6 (VIN2A_D17/RGMII1_TXD0)
D14_MCASP1_FSX: U4.D14 (MCASP1_FSX/PR2_MDIO_DATA)
D17_UART8_RTSN: U4.D17 (MCASP4_AXR1/SPI3_CS0)
E14_GPIO4_18: U4.E14 (MCASP1_AXR12/PR2_MII0_TXD0)
Earth: R112.2, R119.2, R189.1
F12_GPIO5_3: U4.F12 (MCASP1_AXR1/PR2_MII_MT0_CLK)
F14_TIMER12: U4.F14 (MCASP1_AXR15/PR2_MII0_RXD3)
G12_GPIO5_2: U4.G12 (MCASP1_AXR0/PR2_MII0_RXER)
G14_TIMER11: U4.G14 (MCASP1_AXR14/PR2_MII0_RXDV)
GPIO5_18: U4.V2 (UART3_RXD/PR1_MII0_RXDV)
GPIO5_19: U4.Y1 (UART3_TXD/PR1_MII0_MR0CLK)
HDMI_CLKN: U4.AG16 (HDMI1_CLOCKX)
HDMI_CLKP: U4.AH16 (HDMI1_CLOCKY)
HDMI_DATA0N: U4.AG17 (HDMI1_DATA0X)
HDMI_DATA0P: U4.AH17 (HDMI1_DATA0Y)
HDMI_DATA1N: U4.AG18 (HDMI1_DATA1X)
HDMI_DATA1P: U4.AH18 (HDMI1_DATA1Y)
HDMI_DATA2N: U4.AG19 (HDMI1_DATA2X)
HDMI_DATA2P: U4.AH19 (HDMI1_DATA2Y)
HDMI_DDC_CEC: U4.B20 (SPI1_CS3/HDMI_CEC)
HDMI_DDC_HPD: U4.B21 (SPI1_CS2/HDMI_HPD)
HDMI_DDC_SCL: U4.C25 (I2C2_SCL/HDMI1_DDC_SDA)
HDMI_DDC_SDA: U4.F17 (I2C2_SDA/HDMI1_DDC_SCL)
JTAG_EMU0: R192.1, U4.G21 (EMU0)
JTAG_EMU1: R180.1, U4.D24 (EMU1)
JTAG_RTCK: R199.2
JTAG_TCK: R200.2
JTAG_TDI: U4.D23 (TDI)
JTAG_TDO: U4.F19 (TDO)
JTAG_TMS: U4.F18 (TMS)
JTAG_TRSTn: R189.2, U4.D20 (TRSTN)
MCASP2_ACLKX: R608.2
MCASP2_FSX: R607.2
MDIO_CLK: R24.1, R134.1, U4.U4 (MDIO_D), U4.V1 (MDIO_MCLK)
MII0_TXD0: R92.1, U4.U6 (RGMII0_TXD0)
MII0_TXD1: R93.1, U4.V6 (RGMII0_TXD1)
MII0_TXD2: R94.1, U4.U7 (RGMII0_TXD2)
MII0_TXD3: R95.1, U4.V7 (RGMII0_TXD3)
MII0_TX_CLK: R97.1, U4.W9 (RGMII0_TXC)
MII0_TX_EN: R96.1, U4.V9 (RGMII0_TXCTL)
MMC4_DATA0: U4.D28 (UART2_RXD)
MMC4_DATA1: U4.D26 (UART2_TXD)
MMC4_DATA2: U4.D27 (UART2_CTSN/UART3_RXD)
MMC4_DATA3: U4.C28 (UART2_RTSN/UART3_TXD)
unnamed: R119.1, U4.AB10 (USB1_DRVVBUS)
unnamed: R199.1, U4.E18 (RTCK)
unnamed: R200.1, U4.E20 (TCK)
unnamed: R607.1, U4.A18 (MCASP2_FSX/PR2_MII0_RXD1)
PR2_MII0_RXD2: R608.1, U4.A19 (MCASP2_ACLKX/PR2_MII0_RXD2)
RGMII0_RXC: U4.U5 (RGMII0_RXC)
RGMII0_RXCTL: U4.V5 (RGMII0_RXCTL)
RGMII0_RXD0: U4.W2 (RGMII0_RXD0)
RGMII0_RXD1: U4.Y2 (RGMII0_RXD1)
RGMII0_RXD2: U4.V3 (RGMII0_RXD2)
RGMII0_RXD3: U4.V4 (RGMII0_RXD3)
RGMII0_TXC: R97.2
RGMII0_TXCTL: R96.2
RGMII0_TXD0: R92.2
RGMII0_TXD1: R93.2
RGMII0_TXD2: R94.2
RGMII0_TXD3: R95.2
USB1_DM: U4.AC12 (USB1_DM)
USB1_DP: U4.AD12 (USB1_DP)
USB2_DM: U4.AF11 (USB2_DM)
USB2_DP: U4.AE11 (USB2_DP)
USB2_DRVVBUS: R112.1, U4.AC10 (USB2_DRVVBUS)
USB_RXN0: U4.AF12 (USB_RXN0)
USB_RXP0: U4.AE12 (USB_RXP0)
USB_TXN0: U4.AC11 (USB_TXN0)
USB_TXP0: U4.AD11 (USB_TXP0)
VDD_3V3: R24.2, R134.2, R180.2, R192.2

Notes on the sheet:
USB_RX/USB_TX differential impedance: 90ohm+/-7% USB3.0 (SuperSpeed) Tracelength (Total MAX on PCB): 3500mil
differential impedance: 90ohm+-10% common mode impedance: 45ohm+-10%
