beagleboard/beaglebone-ai/kicad/beaglebone-ai-rev-a1/interface2.kicad_sch

## KiCad design kicad/beaglebone-ai-rev-a1/interface2.kicad_sch (2021-06-15)

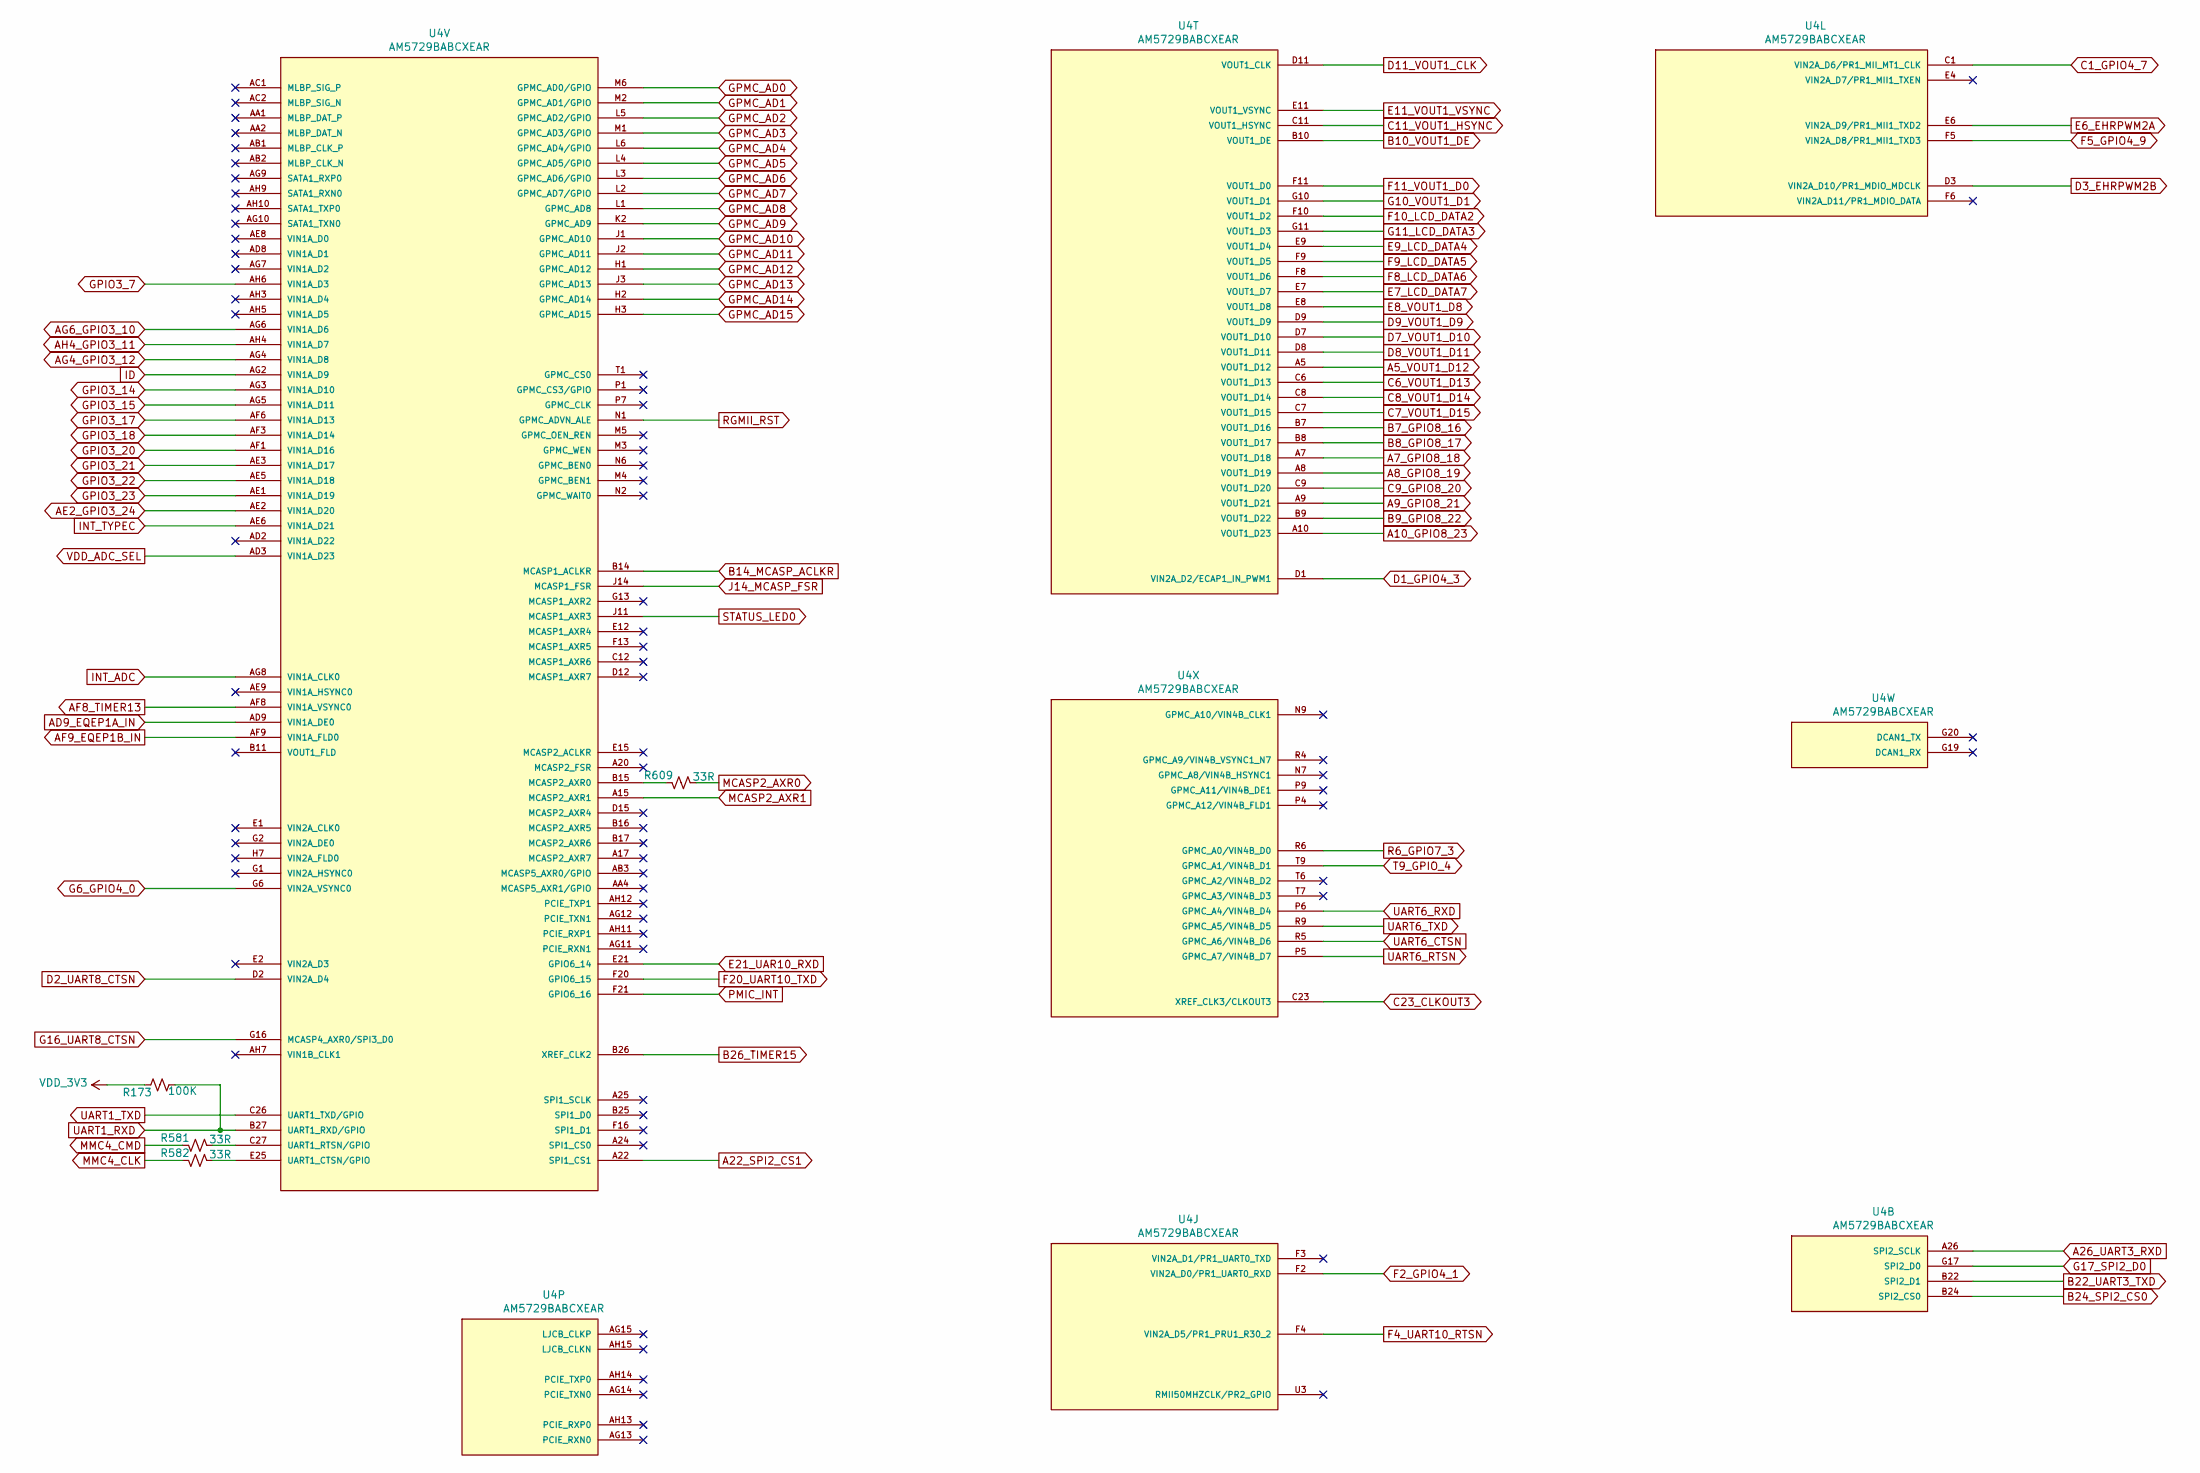
[picture p131: schematic interface2.kicad_sch]

Parts:
R173: 100K; R0402; Rating 5%; Manufacturer P/N RC0402JR-07100KL
R581, R582, R609: 33R; R0402; Rating 5%; Manufacturer P/N RC0402JR-0733RL
U4: AM5729BABCXEAR; BGA760C80P28X28_2300X2300X255; Manufacturer P/N AM5729BABCXEAR

Connections:
A5_VOUT1_D12: U4.A5 (VOUT1_D12)
A7_GPIO8_18: U4.A7 (VOUT1_D18)
A8_GPIO8_19: U4.A8 (VOUT1_D19)
A9_GPIO8_21: U4.A9 (VOUT1_D21)
A10_GPIO8_23: U4.A10 (VOUT1_D23)
A22_SPI2_CS1: U4.A22 (SPI1_CS1)
A26_UART3_RXD: U4.A26 (SPI2_SCLK)
AD9_EQEP1A_IN: U4.AD9 (VIN1A_DE0)
AE2_GPIO3_24: U4.AE2 (VIN1A_D20)
AF8_TIMER13: U4.AF8 (VIN1A_VSYNC0)
AF9_EQEP1B_IN: U4.AF9 (VIN1A_FLD0)
AG4_GPIO3_12: U4.AG4 (VIN1A_D8)
AG6_GPIO3_10: U4.AG6 (VIN1A_D6)
AH4_GPIO3_11: U4.AH4 (VIN1A_D7)
B7_GPIO8_16: U4.B7 (VOUT1_D16)
B8_GPIO8_17: U4.B8 (VOUT1_D17)
B9_GPIO8_22: U4.B9 (VOUT1_D22)
B10_VOUT1_DE: U4.B10 (VOUT1_DE)
B14_MCASP_ACLKR: U4.B14 (MCASP1_ACLKR)
B22_UART3_TXD: U4.B22 (SPI2_D1)
B24_SPI2_CS0: U4.B24 (SPI2_CS0)
B26_TIMER15: U4.B26 (XREF_CLK2)
C1_GPIO4_7: U4.C1 (VIN2A_D6/PR1_MII_MT1_CLK)
C6_VOUT1_D13: U4.C6 (VOUT1_D13)
C7_VOUT1_D15: U4.C7 (VOUT1_D15)
C8_VOUT1_D14: U4.C8 (VOUT1_D14)
C9_GPIO8_20: U4.C9 (VOUT1_D20)
C11_VOUT1_HSYNC: U4.C11 (VOUT1_HSYNC)
C23_CLKOUT3: U4.C23 (XREF_CLK3/CLKOUT3)
D1_GPIO4_3: U4.D1 (VIN2A_D2/ECAP1_IN_PWM1)
D2_UART8_CTSN: U4.D2 (VIN2A_D4)
D3_EHRPWM2B: U4.D3 (VIN2A_D10/PR1_MDIO_MDCLK)
D7_VOUT1_D10: U4.D7 (VOUT1_D10)
D8_VOUT1_D11: U4.D8 (VOUT1_D11)
D9_VOUT1_D9: U4.D9 (VOUT1_D9)
D11_VOUT1_CLK: U4.D11 (VOUT1_CLK)
E6_EHRPWM2A: U4.E6 (VIN2A_D9/PR1_MII1_TXD2)
E7_LCD_DATA7: U4.E7 (VOUT1_D7)
E8_VOUT1_D8: U4.E8 (VOUT1_D8)
E9_LCD_DATA4: U4.E9 (VOUT1_D4)
E11_VOUT1_VSYNC: U4.E11 (VOUT1_VSYNC)
E21_UAR10_RXD: U4.E21 (GPIO6_14)
F2_GPIO4_1: U4.F2 (VIN2A_D0/PR1_UART0_RXD)
F4_UART10_RTSN: U4.F4 (VIN2A_D5/PR1_PRU1_R30_2)
F5_GPIO4_9: U4.F5 (VIN2A_D8/PR1_MII1_TXD3)
F8_LCD_DATA6: U4.F8 (VOUT1_D6)
F9_LCD_DATA5: U4.F9 (VOUT1_D5)
F10_LCD_DATA2: U4.F10 (VOUT1_D2)
F11_VOUT1_D0: U4.F11 (VOUT1_D0)
F20_UART10_TXD: U4.F20 (GPIO6_15)
G6_GPIO4_0: U4.G6 (VIN2A_VSYNC0)
G10_VOUT1_D1: U4.G10 (VOUT1_D1)
G11_LCD_DATA3: U4.G11 (VOUT1_D3)
G16_UART8_CTSN: U4.G16 (MCASP4_AXR0/SPI3_D0)
G17_SPI2_D0: U4.G17 (SPI2_D0)
GPIO3_7: U4.AH6 (VIN1A_D3)
GPIO3_14: U4.AG3 (VIN1A_D10)
GPIO3_15: U4.AG5 (VIN1A_D11)
GPIO3_17: U4.AF6 (VIN1A_D13)
GPIO3_18: U4.AF3 (VIN1A_D14)
GPIO3_20: U4.AF1 (VIN1A_D16)
GPIO3_21: U4.AE3 (VIN1A_D17)
GPIO3_22: U4.AE5 (VIN1A_D18)
GPIO3_23: U4.AE1 (VIN1A_D19)
GPMC_AD0: U4.M6 (GPMC_AD0/GPIO)
GPMC_AD1: U4.M2 (GPMC_AD1/GPIO)
GPMC_AD2: U4.L5 (GPMC_AD2/GPIO)
GPMC_AD3: U4.M1 (GPMC_AD3/GPIO)
GPMC_AD4: U4.L6 (GPMC_AD4/GPIO)
GPMC_AD5: U4.L4 (GPMC_AD5/GPIO)
GPMC_AD6: U4.L3 (GPMC_AD6/GPIO)
GPMC_AD7: U4.L2 (GPMC_AD7/GPIO)
GPMC_AD8: U4.L1 (GPMC_AD8)
GPMC_AD9: U4.K2 (GPMC_AD9)
GPMC_AD10: U4.J1 (GPMC_AD10)
GPMC_AD11: U4.J2 (GPMC_AD11)
GPMC_AD12: U4.H1 (GPMC_AD12)
GPMC_AD13: U4.J3 (GPMC_AD13)
GPMC_AD14: U4.H2 (GPMC_AD14)
GPMC_AD15: U4.H3 (GPMC_AD15)
ID: U4.AG2 (VIN1A_D9)
INT_ADC: U4.AG8 (VIN1A_CLK0)
INT_TYPEC: U4.AE6 (VIN1A_D21)
J14_MCASP_FSR: U4.J14 (MCASP1_FSR)
MCASP2_AXR0: R609.2
MCASP2_AXR1: U4.A15 (MCASP2_AXR1)
MMC4_CLK: R582.1
MMC4_CMD: R581.1
unnamed: R581.2, U4.C27 (UART1_RTSN/GPIO)
unnamed: R582.2, U4.E25 (UART1_CTSN/GPIO)
unnamed: R609.1, U4.B15 (MCASP2_AXR0)
PMIC_INT: U4.F21 (GPIO6_16)
R6_GPIO7_3: U4.R6 (GPMC_A0/VIN4B_D0)
RGMII_RST: U4.N1 (GPMC_ADVN_ALE)
STATUS_LED0: U4.J11 (MCASP1_AXR3)
T9_GPIO_4: U4.T9 (GPMC_A1/VIN4B_D1)
UART1_RXD: R173.2, U4.B27 (UART1_RXD/GPIO)
UART1_TXD: U4.C26 (UART1_TXD/GPIO)
UART6_CTSN: U4.R5 (GPMC_A6/VIN4B_D6)
UART6_RTSN: U4.P5 (GPMC_A7/VIN4B_D7)
UART6_RXD: U4.P6 (GPMC_A4/VIN4B_D4)
UART6_TXD: U4.R9 (GPMC_A5/VIN4B_D5)
VDD_3V3: R173.1
VDD_ADC_SEL: U4.AD3 (VIN1A_D23)
