beagleboard/beaglebone-ai/kicad/beaglebone-ai-rev-a1/mmc_uboot.kicad_sch

## KiCad design kicad/beaglebone-ai-rev-a1/mmc_uboot.kicad_sch (2021-06-15)

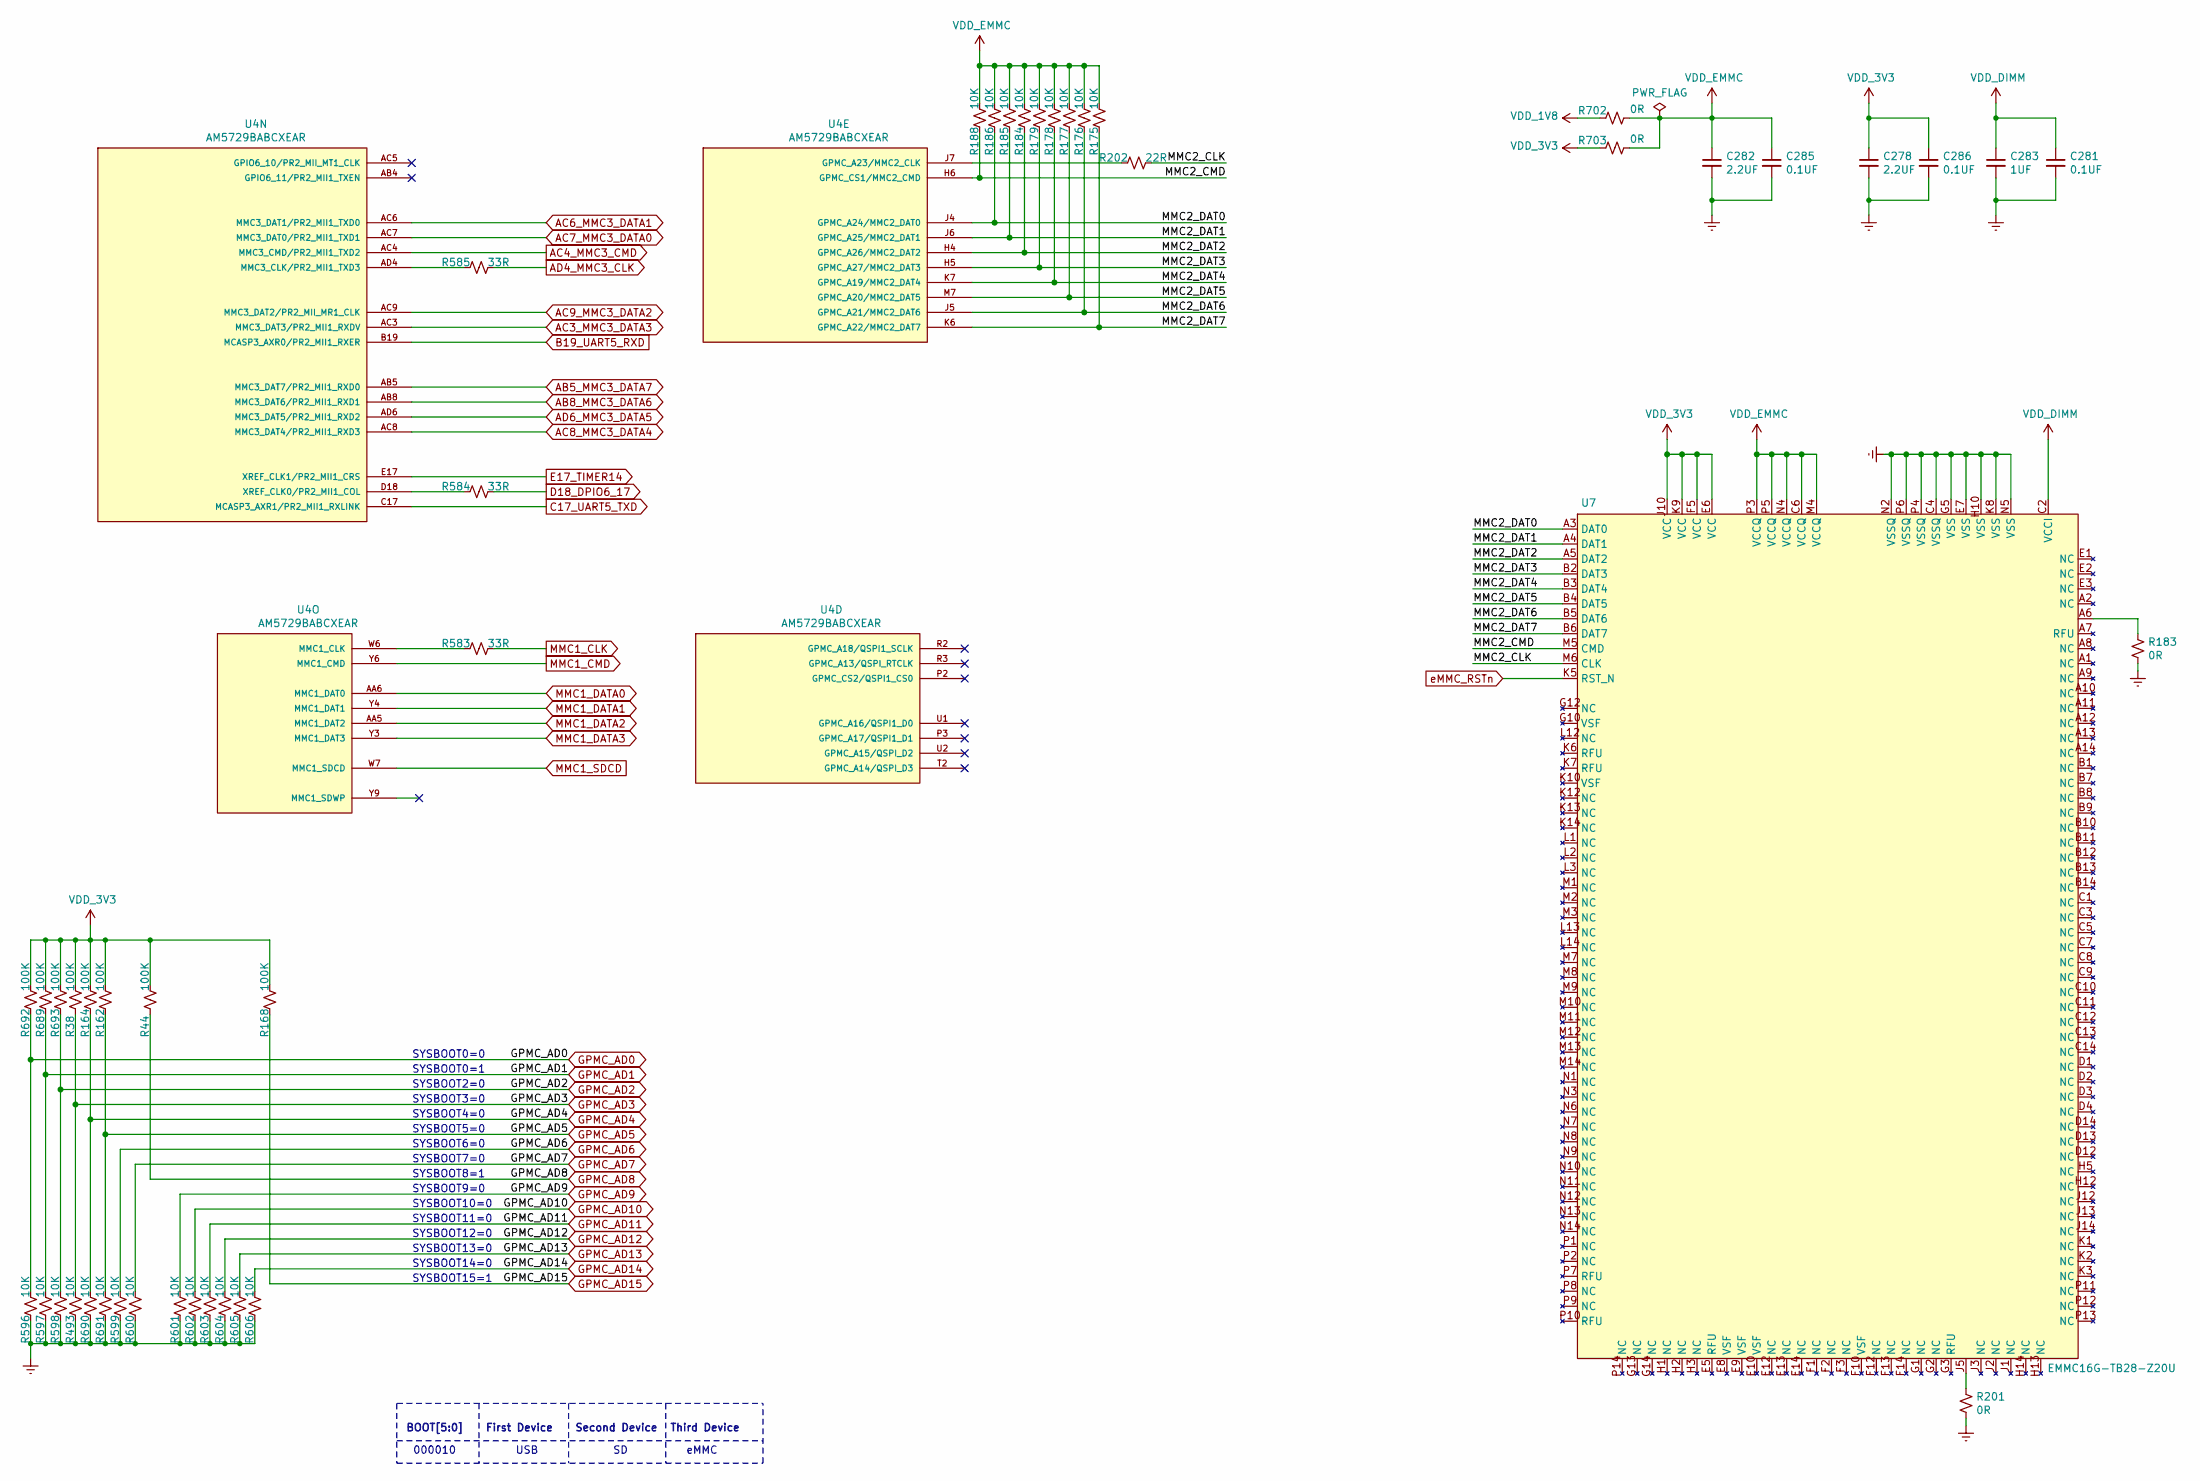
[picture p132: schematic mmc_uboot.kicad_sch]

Parts:
C278, C282: 2.2UF; C0603; Rating 16V,X5R; Manufacturer P/N GRM188R61C225KE15D
C281, C285, C286: 0.1UF; C0402; Rating 16V,X7R; Manufacturer P/N GRM155R71C104KA88D
C283: 1UF; C0402; Rating 10V,X5R; Manufacturer P/N GRM155R61A105KE15D
R38, R44, R162, R164, R168, R689, R692, R693: 100K; R0402; Rating 5%; Manufacturer P/N RC0402JR-07100KL
R175, R176, R177, R178, R179, R184, R185, R186, R188, R493, R596, R597, R598, R599, R600, R601, R602, R603, R604, R605, R606, R690, R691: 10K; R0402; Rating 5%; Manufacturer P/N RC0402JR-0710KL
R183, R201, R702, R703: 0R; R0402; Rating 5%; Manufacturer P/N RC0402JR-070RL
R202: 22R; R0402; Rating 5%; Manufacturer P/N RC0402JR-0722RL
R583, R584, R585: 33R; R0402; Rating 5%; Manufacturer P/N RC0402JR-0733RL
U4: AM5729BABCXEAR; BGA760C80P28X28_2300X2300X255; Manufacturer P/N AM5729BABCXEAR
U7: EMMC16G-TB28-Z20U; BGA153P5; Manufacturer P/N EMMC16G-TB28-Z20U

Connections:
AB5_MMC3_DATA7: U4.AB5 (MMC3_DAT7/PR2_MII1_RXD0)
AB8_MMC3_DATA6: U4.AB8 (MMC3_DAT6/PR2_MII1_RXD1)
AC3_MMC3_DATA3: U4.AC3 (MMC3_DAT3/PR2_MII1_RXDV)
AC4_MMC3_CMD: U4.AC4 (MMC3_CMD/PR2_MII1_TXD2)
AC6_MMC3_DATA1: U4.AC6 (MMC3_DAT1/PR2_MII1_TXD0)
AC7_MMC3_DATA0: U4.AC7 (MMC3_DAT0/PR2_MII1_TXD1)
AC8_MMC3_DATA4: U4.AC8 (MMC3_DAT4/PR2_MII1_RXD3)
AC9_MMC3_DATA2: U4.AC9 (MMC3_DAT2/PR2_MII_MR1_CLK)
AD4_MMC3_CLK: R585.1
AD6_MMC3_DATA5: U4.AD6 (MMC3_DAT5/PR2_MII1_RXD2)
B19_UART5_RXD: U4.B19 (MCASP3_AXR0/PR2_MII1_RXER)
C17_UART5_TXD: U4.C17 (MCASP3_AXR1/PR2_MII1_RXLINK)
D18_DPIO6_17: R584.1
E17_TIMER14: U4.E17 (XREF_CLK1/PR2_MII1_CRS)
Earth: C278.2, C281.2, C282.2, C283.2, C285.2, C286.2, R183.2, R201.2, R493.2, R596.2, R597.2, R598.2, R599.2, R600.2, R601.2, R602.2, R603.2, R604.2, R605.2, R606.2, R690.2, R691.2, U7.C4 (VSSQ), U7.E7 (VSS), U7.G5 (VSS), U7.H10 (VSS), U7.K8 (VSS), U7.N2 (VSSQ), U7.N5 (VSS), U7.P4 (VSSQ), U7.P6 (VSSQ)
GPMC_AD0: R596.1, R692.2
GPMC_AD1: R597.1, R689.2
GPMC_AD2: R598.1, R693.2
GPMC_AD3: R38.2, R493.1
GPMC_AD4: R164.2, R690.1
GPMC_AD5: R162.2, R691.1
GPMC_AD6: R599.1
GPMC_AD7: R600.1
GPMC_AD8: R44.2
GPMC_AD9: R601.1
GPMC_AD10: R602.1
GPMC_AD11: R603.1
GPMC_AD12: R604.1
GPMC_AD13: R605.1
GPMC_AD14: R606.1
GPMC_AD15: R168.2
MMC1_CLK: R583.1
MMC1_CMD: U4.Y6 (MMC1_CMD)
MMC1_DATA0: U4.AA6 (MMC1_DAT0)
MMC1_DATA1: U4.Y4 (MMC1_DAT1)
MMC1_DATA2: U4.AA5 (MMC1_DAT2)
MMC1_DATA3: U4.Y3 (MMC1_DAT3)
MMC1_SDCD: U4.W7 (MMC1_SDCD)
MMC2_CLK: R202.1, U7.M6 (CLK)
MMC2_CMD: R188.2, U4.H6 (GPMC_CS1/MMC2_CMD), U7.M5 (CMD)
MMC2_DAT0: R186.2, U4.J4 (GPMC_A24/MMC2_DAT0), U7.A3 (DAT0)
MMC2_DAT1: R185.2, U4.J6 (GPMC_A25/MMC2_DAT1), U7.A4 (DAT1)
MMC2_DAT2: R184.2, U4.H4 (GPMC_A26/MMC2_DAT2), U7.A5 (DAT2)
MMC2_DAT3: R179.2, U4.H5 (GPMC_A27/MMC2_DAT3), U7.B2 (DAT3)
MMC2_DAT4: R178.2, U4.K7 (GPMC_A19/MMC2_DAT4), U7.B3 (DAT4)
MMC2_DAT5: R177.2, U4.M7 (GPMC_A20/MMC2_DAT5), U7.B4 (DAT5)
MMC2_DAT6: R176.2, U4.J5 (GPMC_A21/MMC2_DAT6), U7.B5 (DAT6)
MMC2_DAT7: R175.2, U4.K6 (GPMC_A22/MMC2_DAT7), U7.B6 (DAT7)
unnamed: R183.1, U7.A6
unnamed: R201.1, U7.J5
unnamed: R202.2, U4.J7 (GPMC_A23/MMC2_CLK)
unnamed: R583.2, U4.W6 (MMC1_CLK)
unnamed: R584.2, U4.D18 (XREF_CLK0/PR2_MII1_COL)
unnamed: R585.2, U4.AD4 (MMC3_CLK/PR2_MII1_TXD3)
VDD_1V8: R702.1
VDD_3V3: C278.1, C286.1, R38.1, R44.1, R162.1, R164.1, R168.1, R689.1, R692.1, R693.1, R703.1, U7.E6 (VCC), U7.F5 (VCC), U7.J10 (VCC), U7.K9 (VCC)
VDD_DIMM: C281.1, C283.1, U7.C2 (VCCI)
VDD_EMMC: C282.1, C285.1, R175.1, R176.1, R177.1, R178.1, R179.1, R184.1, R185.1, R186.1, R188.1, R702.2, R703.2, U7.C6 (VCCQ), U7.M4 (VCCQ), U7.N4 (VCCQ), U7.P3 (VCCQ), U7.P5 (VCCQ)
eMMC_RSTn: U7.K5 (RST_N)

Notes on the sheet:
SYSBOOT0=0
SYSBOOT0=1
SYSBOOT2=0
SYSBOOT3=0
SYSBOOT4=0
SYSBOOT5=0
SYSBOOT6=0
SYSBOOT7=0
SYSBOOT8=1
SYSBOOT9=0
SYSBOOT10=0
SYSBOOT11=0
SYSBOOT12=0
SYSBOOT13=0
SYSBOOT14=0
SYSBOOT15=1
000010
BOOT[5:0]
USB
First Device
Second Device
eMMC
Third Device
