beagleboard/beaglebone-ai/kicad/beaglebone-ai-rev-a1/pmic1.kicad_sch

## KiCad design kicad/beaglebone-ai-rev-a1/pmic1.kicad_sch (2021-06-15)

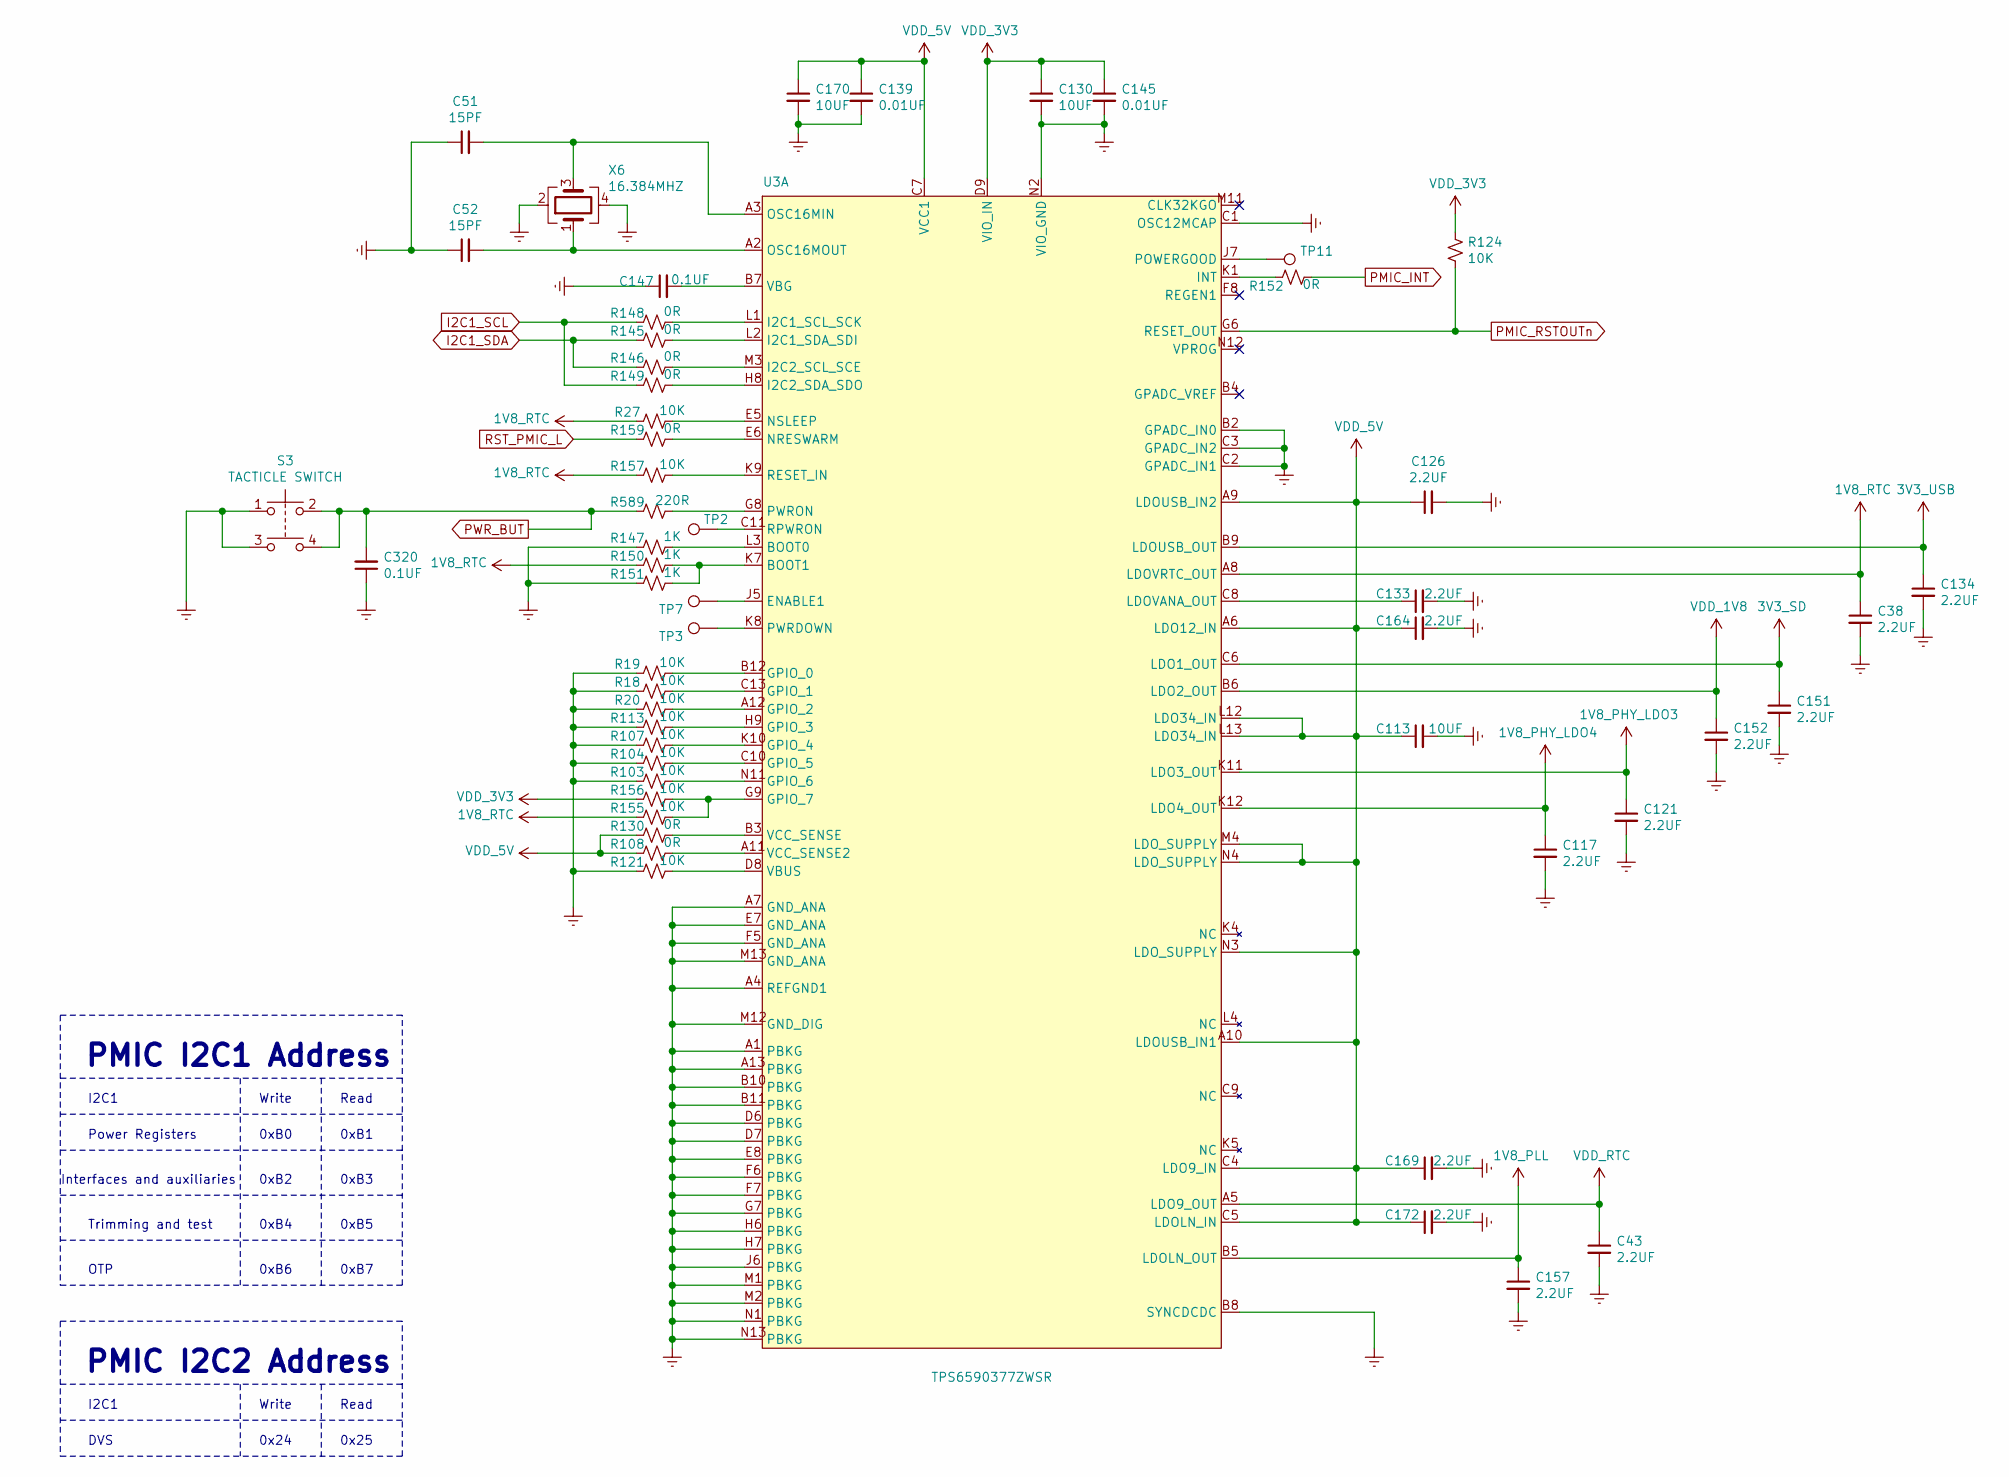
[picture p133: schematic pmic1.kicad_sch]

Parts:
C38, C43, C117, C121, C133, C134, C151, C152, C157: 2.2UF; C0402; Rating 6.3V,X5R; Manufacturer P/N GRM155R60J225ME15D
C51, C52: 15PF; C0402; Rating 50V,C0G; Manufacturer P/N GRM1555C1H150GA01D
C113, C130, C170: 10UF; C0603; Rating 10V,X5R; Manufacturer P/N GRM188R61A106KE69D
C126, C164, C169, C172: 2.2UF; C0603; Rating 16V,X5R; Manufacturer P/N GRM188R61C225KE15D
C139, C145: 0.01UF; C0402; Rating X7R,16V; Manufacturer P/N GRM155R71C103KA01D
C147, C320: 0.1UF; C0402; Rating 16V,X7R; Manufacturer P/N GRM155R71C104KA88D
R18, R19, R20, R27, R103, R104, R107, R113, R121, R124, R155, R156, R157: 10K; R0402; Rating 5%; Manufacturer P/N RC0402JR-0710KL
R108, R130, R145, R146, R148, R149, R152, R159: 0R; R0402; Rating 5%; Manufacturer P/N RC0402JR-070RL
R147, R150, R151: 1K; R0402; Rating 5%; Manufacturer P/N RC0402JR-071KL
R589: 220R; R0402; Rating 5%; Manufacturer P/N RC0402JR-07220RL
S3: TACTICLE SWITCH; SWS4B46X28; Manufacturer P/N KMR231GLFS
TP2, TP3, TP7, TP11: NI; TP30
U3: TPS6590377ZWSR; BGA169C80P13X13_1200X1200X140; Manufacturer P/N TPS6590377ZWSR
X6: 16.384MHZ; OSCCC250X200X60-4N; Rating 20PPM; Manufacturer P/N 5ZAA16384102TFA5Q3

Connections:
1V8_PHY_LDO3: C121.1, U3.K11 (LDO3_OUT)
1V8_PHY_LDO4: C117.1, U3.K12 (LDO4_OUT)
1V8_PLL: C157.1, U3.B5 (LDOLN_OUT)
1V8_RTC: C38.1, R27.1, R150.1, R155.1, R157.1, U3.A8 (LDOVRTC_OUT)
3V3_SD: C151.1, U3.C6 (LDO1_OUT)
3V3_USB: C134.1, U3.B9 (LDOUSB_OUT)
Earth: C38.2, C43.2, C51.1, C52.1, C113.2, C117.2, C121.2, C126.2, C130.2, C133.2, C134.2, C139.2, C145.2, C147.1, C151.2, C152.2, C157.2, C164.2, C169.2, C170.2, C172.2, C320.1, R18.1, R19.1, R20.1, R103.1, R104.1, R107.1, R113.1, R121.1, R147.1, R151.1, S3.1, S3.3, U3.A1 (PBKG), U3.A4 (REFGND1), U3.A7 (GND_ANA), U3.A13 (PBKG), U3.B2 (GPADC_IN0), U3.B8 (SYNCDCDC), U3.B10 (PBKG), U3.B11 (PBKG), U3.C1 (OSC12MCAP), U3.C2 (GPADC_IN1), U3.C3 (GPADC_IN2), U3.D6 (PBKG), U3.D7 (PBKG), U3.E7 (GND_ANA), U3.E8 (PBKG), U3.F5 (GND_ANA), U3.F6 (PBKG), U3.F7 (PBKG), U3.G7 (PBKG), U3.H6 (PBKG), U3.H7 (PBKG), U3.J6 (PBKG), U3.M1 (PBKG), U3.M2 (PBKG), U3.M12 (GND_DIG), U3.M13 (GND_ANA), U3.N1 (PBKG), U3.N2 (VIO_GND), U3.N13 (PBKG), X6.2, X6.4
I2C1_SCL: R148.1, R149.1
I2C1_SDA: R145.1, R146.1
unnamed: C51.2, U3.A3 (OSC16MIN), X6.3
unnamed: C52.2, U3.A2 (OSC16MOUT), X6.1
unnamed: C133.1, U3.C8 (LDOVANA_OUT)
unnamed: C147.2, U3.B7 (VBG)
unnamed: R18.2, U3.C13 (GPIO_1)
unnamed: R19.2, U3.B12 (GPIO_0)
unnamed: R20.2, U3.A12 (GPIO_2)
unnamed: R27.2, U3.E5 (NSLEEP)
unnamed: R103.2, U3.N11 (GPIO_6)
unnamed: R104.2, U3.C10 (GPIO_5)
unnamed: R107.2, U3.K10 (GPIO_4)
unnamed: R108.2, U3.A11 (VCC_SENSE2)
unnamed: R113.2, U3.H9 (GPIO_3)
unnamed: R121.2, U3.D8 (VBUS)
unnamed: R130.2, U3.B3 (VCC_SENSE)
unnamed: R145.2, U3.L2 (I2C1_SDA_SDI)
unnamed: R146.2, U3.M3 (I2C2_SCL_SCE)
unnamed: R147.2, U3.L3 (BOOT0)
unnamed: R148.2, U3.L1 (I2C1_SCL_SCK)
unnamed: R149.2, U3.H8 (I2C2_SDA_SDO)
unnamed: R150.2, R151.2, U3.K7 (BOOT1)
unnamed: R152.1, U3.K1 (INT)
unnamed: R155.2, R156.2, U3.G9 (GPIO_7)
unnamed: R157.2, U3.K9 (RESET_IN)
unnamed: R159.2, U3.E6 (NRESWARM)
unnamed: R589.2, U3.G8 (PWRON)
unnamed: TP2.1, U3.C11 (RPWRON)
unnamed: TP3.1, U3.K8 (PWRDOWN)
unnamed: TP7.1, U3.J5 (ENABLE1)
unnamed: TP11.1, U3.J7 (POWERGOOD)
PMIC_INT: R152.2
PMIC_RSTOUTn: R124.1, U3.G6 (RESET_OUT)
PWR_BUT: C320.2, R589.1, S3.2, S3.4
RST_PMIC_L: R159.1
VDD_1V8: C152.1, U3.B6 (LDO2_OUT)
VDD_3V3: C130.1, C145.1, R124.2, R156.1, U3.D9 (VIO_IN)
VDD_5V: C113.1, C126.1, C139.1, C164.1, C169.1, C170.1, C172.1, R108.1, R130.1, U3.A6 (LDO12_IN), U3.A9 (LDOUSB_IN2), U3.A10 (LDOUSB_IN1), U3.C4 (LDO9_IN), U3.C5 (LDOLN_IN), U3.C7 (VCC1), U3.L12 (LDO34_IN), U3.L13 (LDO34_IN), U3.M4 (LDO_SUPPLY), U3.N3 (LDO_SUPPLY), U3.N4 (LDO_SUPPLY)
VDD_RTC: C43.1, U3.A5 (LDO9_OUT)

Notes on the sheet:
Interfaces and auxiliaries
I2C1
Power Registers
Trimming and test
OTP
DVS
Write
0xB0
0xB2
0xB4
0xB6
0x24
Read
0xB1
0xB3
0xB5
0xB7
0x25
PMIC I2C1 Address
PMIC I2C2 Address
