beagleboard/beaglebone-ai/kicad/beaglebone-ai-rev-a1/pmic2.kicad_sch

## KiCad design kicad/beaglebone-ai-rev-a1/pmic2.kicad_sch (2021-06-15)

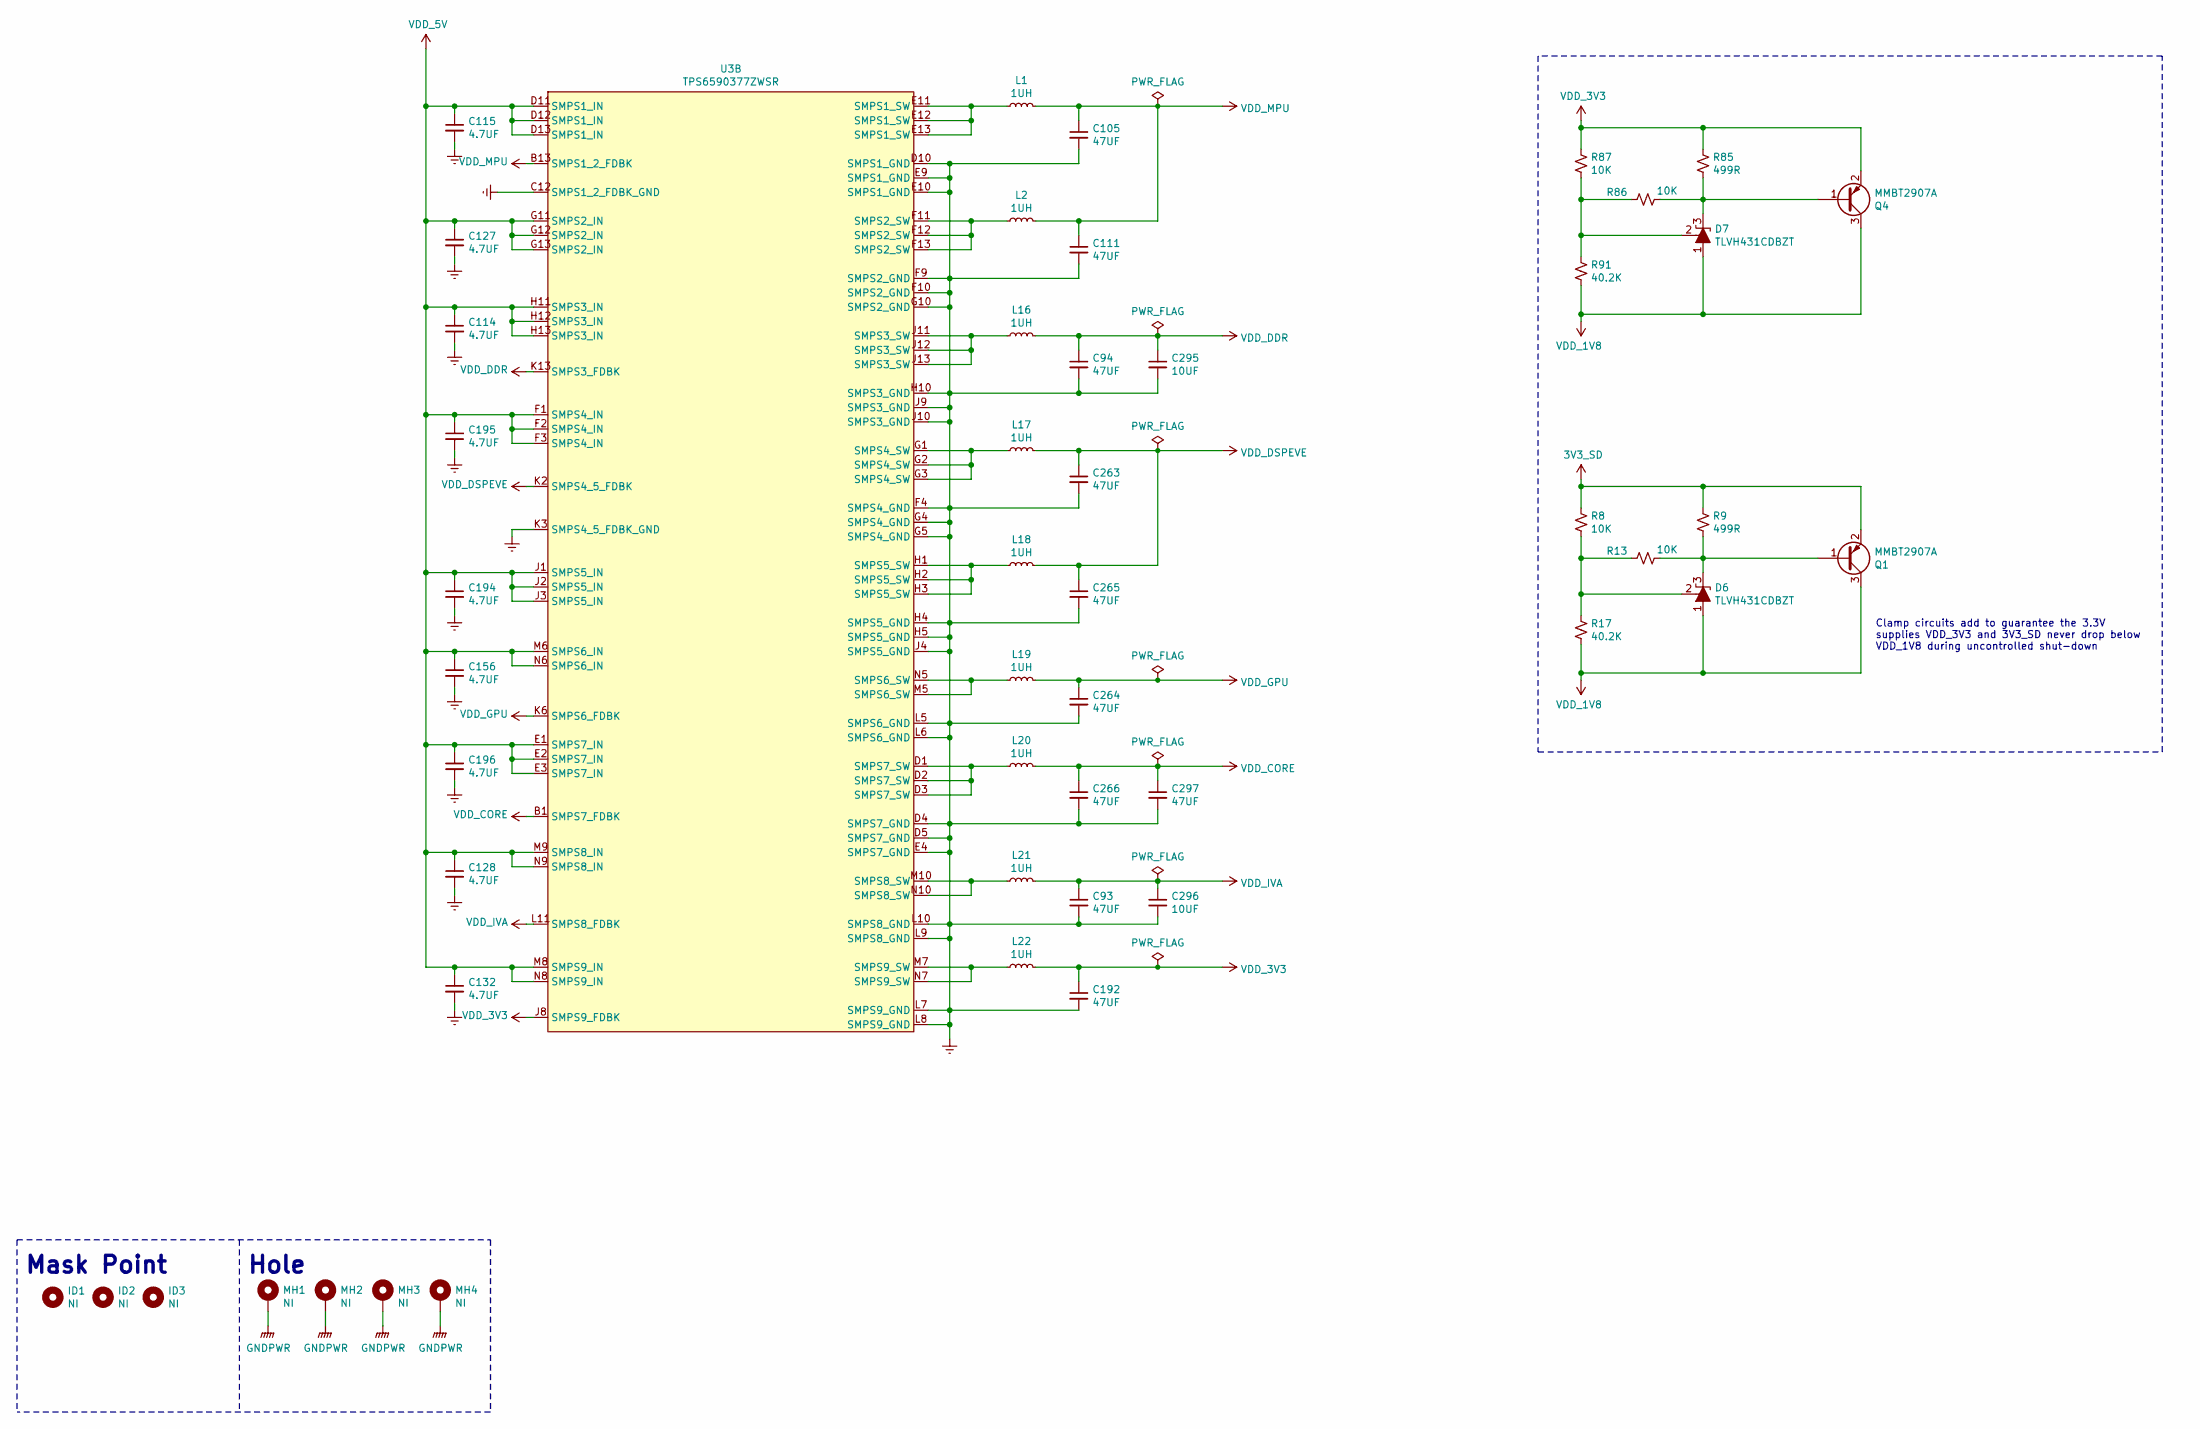
[picture p134: schematic pmic2.kicad_sch]

Parts:
C93, C94, C105, C111, C192, C263, C264, C265, C266, C297: 47UF; C0805; Rating 6.3V,X5R; Manufacturer P/N GRM21BR60J476ME15L
C114, C115, C127, C128, C132, C156, C194, C195, C196: 4.7UF; C0603; Rating 16V,X5R; Manufacturer P/N GRM188R61C475KAAJD
C295: 10UF; C0603; Rating 10V,X5R; Manufacturer P/N GRM188R61A106KE69D
C296: 10UF; C0402; Rating X5R,6.3V; Manufacturer P/N CC0402MRX5R5BB106
D6, D7: TLVH431CDBZT; SOT95P240X120-3N; Manufacturer P/N TLVH431CDBZT
ID1, ID2, ID3: NI; FD40
L1, L2: 1UH; L40X40_B; Manufacturer P/N Power Inductor,Magnetic shielded,1uH,id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
L16, L17, L18, L19, L20, L21, L22: 1UH; INDPW250X200X105N; Manufacturer P/N SMD Power Inductors 1uH +/-20%;-25C to 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
MH1, MH2, MH3, MH4: NI; Plated hole,Circle,DAI 4.445MM ,VIA 3.175MM
Q1, Q4: MMBT2907A; SOT23_123; Rating 600mA; Manufacturer P/N MMBT2907A-7-F
R8, R13, R86, R87: 10K; R0402; Rating 1%; Manufacturer P/N RC0402FR-0710KL
R9, R85: 499R; R0402; Rating 1%; Manufacturer P/N RC0402FR-07499RL
R17, R91: 40.2K; R0402; Rating 1%; Manufacturer P/N RC0402FR-0740K2L
U3: TPS6590377ZWSR; BGA169C80P13X13_1200X1200X140; Manufacturer P/N TPS6590377ZWSR

Connections:
3V3_SD: Q1.2 (E), R8.1, R9.1
Earth: C93.2, C94.2, C105.2, C111.2, C114.2, C115.2, C127.2, C128.2, C132.2, C156.2, C192.2, C194.2, C195.2, C196.2, C263.2, C264.2, C265.2, C266.2, C295.2, C296.2, C297.2, U3.C12 (SMPS1_2_FDBK_GND), U3.D4 (SMPS7_GND), U3.D5 (SMPS7_GND), U3.D10 (SMPS1_GND), U3.E4 (SMPS7_GND), U3.E9 (SMPS1_GND), U3.E10 (SMPS1_GND), U3.F4 (SMPS4_GND), U3.F9 (SMPS2_GND), U3.F10 (SMPS2_GND), U3.G4 (SMPS4_GND), U3.G5 (SMPS4_GND), U3.G10 (SMPS2_GND), U3.H4 (SMPS5_GND), U3.H5 (SMPS5_GND), U3.H10 (SMPS3_GND), U3.J4 (SMPS5_GND), U3.J9 (SMPS3_GND), U3.J10 (SMPS3_GND), U3.K3 (SMPS4_5_FDBK_GND), U3.L5 (SMPS6_GND), U3.L6 (SMPS6_GND), U3.L7 (SMPS9_GND), U3.L8 (SMPS9_GND), U3.L9 (SMPS8_GND), U3.L10 (SMPS8_GND)
GNDPWR: MH1.1, MH2.1, MH3.1, MH4.1
unnamed: D6.2 (REF), R8.2, R13.1, R17.2
unnamed: D6.3 (K), Q1.1 (B), R9.2, R13.2
unnamed: D7.2 (REF), R86.1, R87.2, R91.2
unnamed: D7.3 (K), Q4.1 (B), R85.2, R86.2
unnamed: L1.1, U3.E11 (SMPS1_SW), U3.E12 (SMPS1_SW), U3.E13 (SMPS1_SW)
unnamed: L2.1, U3.F11 (SMPS2_SW), U3.F12 (SMPS2_SW), U3.F13 (SMPS2_SW)
unnamed: L16.1, U3.J11 (SMPS3_SW), U3.J12 (SMPS3_SW), U3.J13 (SMPS3_SW)
unnamed: L17.1, U3.G1 (SMPS4_SW), U3.G2 (SMPS4_SW), U3.G3 (SMPS4_SW)
unnamed: L18.1, U3.H1 (SMPS5_SW), U3.H2 (SMPS5_SW), U3.H3 (SMPS5_SW)
unnamed: L19.1, U3.M5 (SMPS6_SW), U3.N5 (SMPS6_SW)
unnamed: L20.1, U3.D1 (SMPS7_SW), U3.D2 (SMPS7_SW), U3.D3 (SMPS7_SW)
unnamed: L21.1, U3.M10 (SMPS8_SW), U3.N10 (SMPS8_SW)
unnamed: L22.1, U3.M7 (SMPS9_SW), U3.N7 (SMPS9_SW)
VDD_1V8: D6.1 (A), D7.1 (A), Q1.3 (C), Q4.3 (C), R17.1, R91.1
VDD_3V3: C192.1, L22.2, Q4.2 (E), R85.1, R87.1, U3.J8 (SMPS9_FDBK)
VDD_5V: C114.1, C115.1, C127.1, C128.1, C132.1, C156.1, C194.1, C195.1, C196.1, U3.D11 (SMPS1_IN), U3.D12 (SMPS1_IN), U3.D13 (SMPS1_IN), U3.E1 (SMPS7_IN), U3.E2 (SMPS7_IN), U3.E3 (SMPS7_IN), U3.F1 (SMPS4_IN), U3.F2 (SMPS4_IN), U3.F3 (SMPS4_IN), U3.G11 (SMPS2_IN), U3.G12 (SMPS2_IN), U3.G13 (SMPS2_IN), U3.H11 (SMPS3_IN), U3.H12 (SMPS3_IN), U3.H13 (SMPS3_IN), U3.J1 (SMPS5_IN), U3.J2 (SMPS5_IN), U3.J3 (SMPS5_IN), U3.M6 (SMPS6_IN), U3.M8 (SMPS9_IN), U3.M9 (SMPS8_IN), U3.N6 (SMPS6_IN), U3.N8 (SMPS9_IN), U3.N9 (SMPS8_IN)
VDD_CORE: C266.1, C297.1, L20.2, U3.B1 (SMPS7_FDBK)
VDD_DDR: C94.1, C295.1, L16.2, U3.K13 (SMPS3_FDBK)
VDD_DSPEVE: C263.1, C265.1, L17.2, L18.2, U3.K2 (SMPS4_5_FDBK)
VDD_GPU: C264.1, L19.2, U3.K6 (SMPS6_FDBK)
VDD_IVA: C93.1, C296.1, L21.2, U3.L11 (SMPS8_FDBK)
VDD_MPU: C105.1, C111.1, L1.2, L2.2, U3.B13 (SMPS1_2_FDBK)

Notes on the sheet:
Mask Point
Hole
Clamp circuits add to guarantee the 3.3V supplies VDD_3V3 and 3V3_SD never drop below VDD_1V8 during uncontrolled shut-down
