beagleboard/beaglebone-ai/kicad/beaglebone-ai-rev-a1/pp_decoupling.kicad_sch

## KiCad design kicad/beaglebone-ai-rev-a1/pp_decoupling.kicad_sch (2021-06-15)

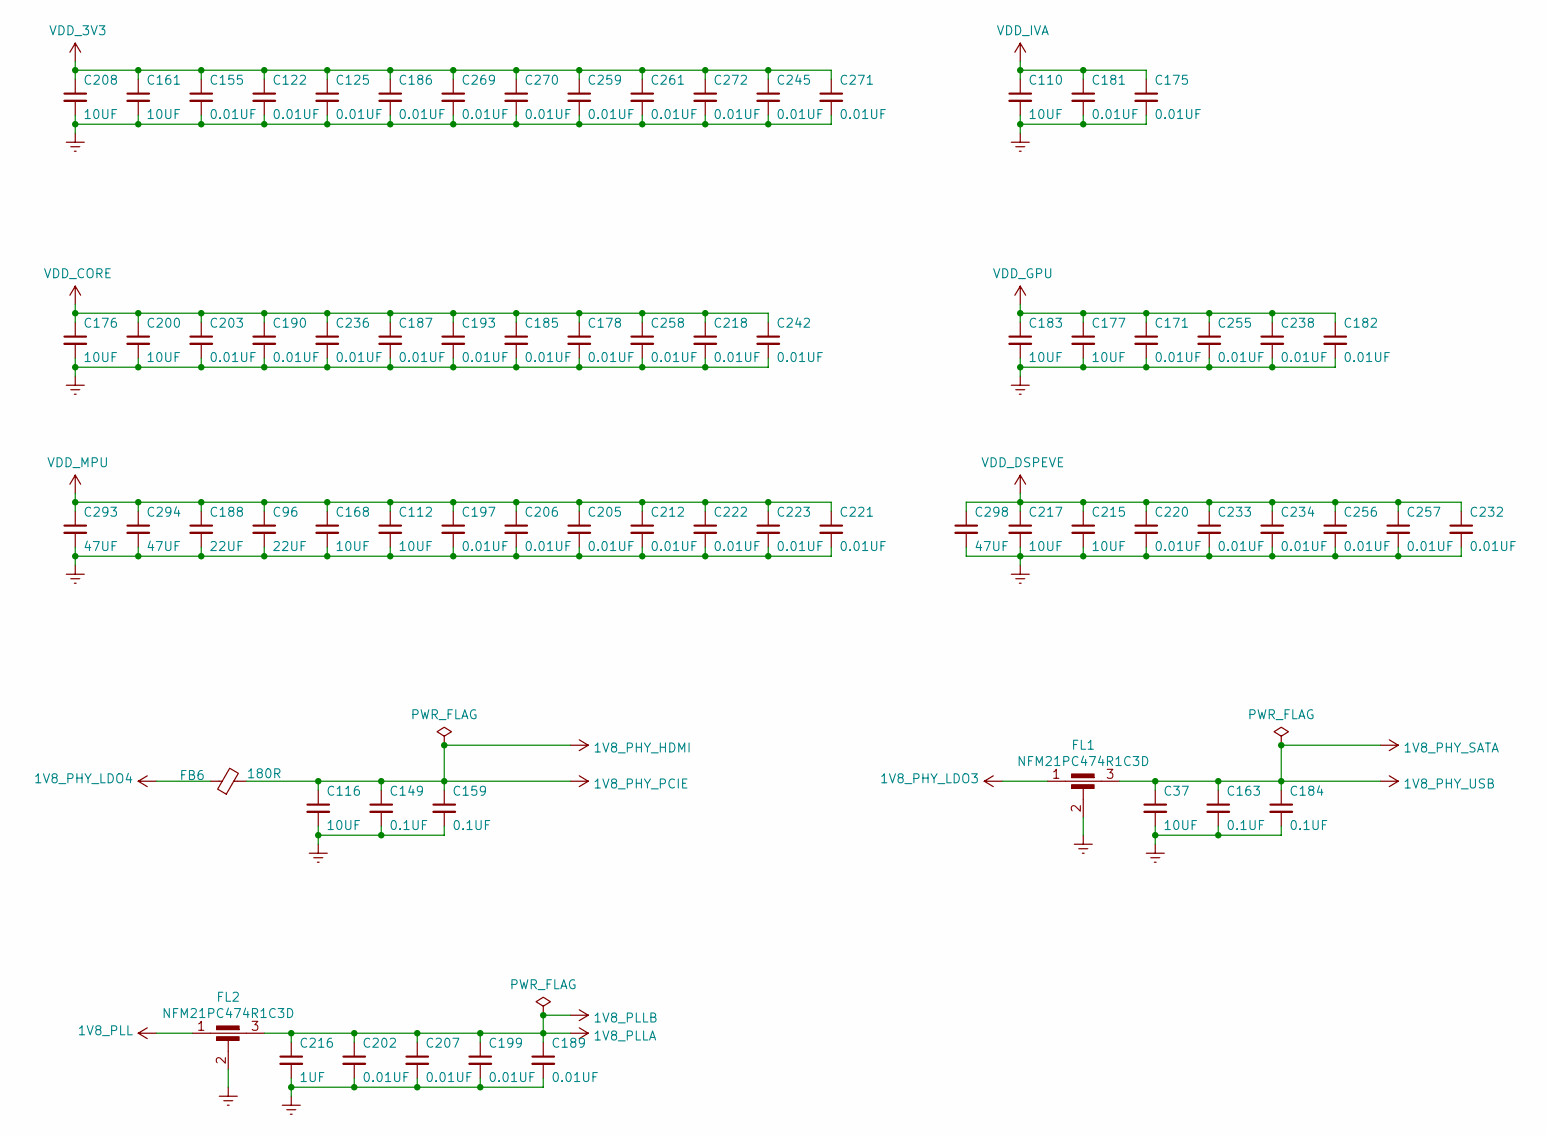
[picture p135: schematic pp_decoupling.kicad_sch]

Parts:
C37, C116, C161, C208: 10UF; C0603; Rating 10V,X5R; Manufacturer P/N GRM188R61A106KE69D
C96, C188: 22UF; C0603; Rating 6.3V,X5R; Manufacturer P/N GRM188R60J226MEA0D
C110, C112, C168, C176, C177, C183, C200, C215, C217: 10UF; C0402; Rating X5R,6.3V; Manufacturer P/N CC0402MRX5R5BB106
C122, C125, C155, C171, C175, C178, C181, C182, C185, C186, C187, C189, C190, C193, C197, C199, C202, C203, C205, C206, C207, C212, C218, C220, C221, C222, C223, C232, C233, C234, C236, C238, C242, C245, C255, C256, C257, C258, C259, C261, C269, C270, C271, C272: 0.01UF; C0402; Rating X7R,16V; Manufacturer P/N GRM155R71C103KA01D
C149, C159, C163, C184: 0.1UF; C0402; Rating 16V,X7R; Manufacturer P/N GRM155R71C104KA88D
C216: 1UF; C0402; Rating 16V,X5R; Manufacturer P/N GRM155R61C105KA12D
C293, C294, C298: 47UF; C0805; Rating 6.3V,X5R; Manufacturer P/N GRM21BR60J476ME15L
FB6: 180R; L0603; Rating 1500mA; Manufacturer P/N BLM18PG181SN1D
FL1, FL2: NFM21PC474R1C3D; FL0805; Manufacturer P/N NFM21PC474R1C3D

Connections:
1V8_PHY_HDMI: C116.1, C149.1, C159.1, FB6.2
1V8_PHY_LDO3: FL1.1
1V8_PHY_LDO4: FB6.1
1V8_PHY_SATA: C37.1, C163.1, C184.1, FL1.3
1V8_PLL: FL2.1
1V8_PLLA: C189.1, C199.1, C202.1, C207.1, C216.1, FL2.3
Earth: C37.2, C96.2, C110.2, C112.2, C116.2, C122.2, C125.2, C149.2, C155.2, C159.2, C161.2, C163.2, C168.2, C171.2, C175.2, C176.2, C177.2, C178.2, C181.2, C182.2, C183.2, C184.2, C185.2, C186.2, C187.2, C188.2, C189.2, C190.2, C193.2, C197.2, C199.2, C200.2, C202.2, C203.2, C205.2, C206.2, C207.2, C208.2, C212.2, C215.2, C216.2, C217.2, C218.2, C220.2, C221.2, C222.2, C223.2, C232.2, C233.2, C234.2, C236.2, C238.2, C242.2, C245.2, C255.2, C256.2, C257.2, C258.2, C259.2, C261.2, C269.2, C270.2, C271.2, C272.2, C293.2, C294.2, C298.2, FL1.2, FL2.2
VDD_3V3: C122.1, C125.1, C155.1, C161.1, C186.1, C208.1, C245.1, C259.1, C261.1, C269.1, C270.1, C271.1, C272.1
VDD_CORE: C176.1, C178.1, C185.1, C187.1, C190.1, C193.1, C200.1, C203.1, C218.1, C236.1, C242.1, C258.1
VDD_DSPEVE: C215.1, C217.1, C220.1, C232.1, C233.1, C234.1, C256.1, C257.1, C298.1
VDD_GPU: C171.1, C177.1, C182.1, C183.1, C238.1, C255.1
VDD_IVA: C110.1, C175.1, C181.1
VDD_MPU: C96.1, C112.1, C168.1, C188.1, C197.1, C205.1, C206.1, C212.1, C221.1, C222.1, C223.1, C293.1, C294.1
