beagleboard/beaglebone-ai/kicad/beaglebone-ai-rev-a1/proc_power.kicad_sch

## KiCad design kicad/beaglebone-ai-rev-a1/proc_power.kicad_sch (2021-06-15)

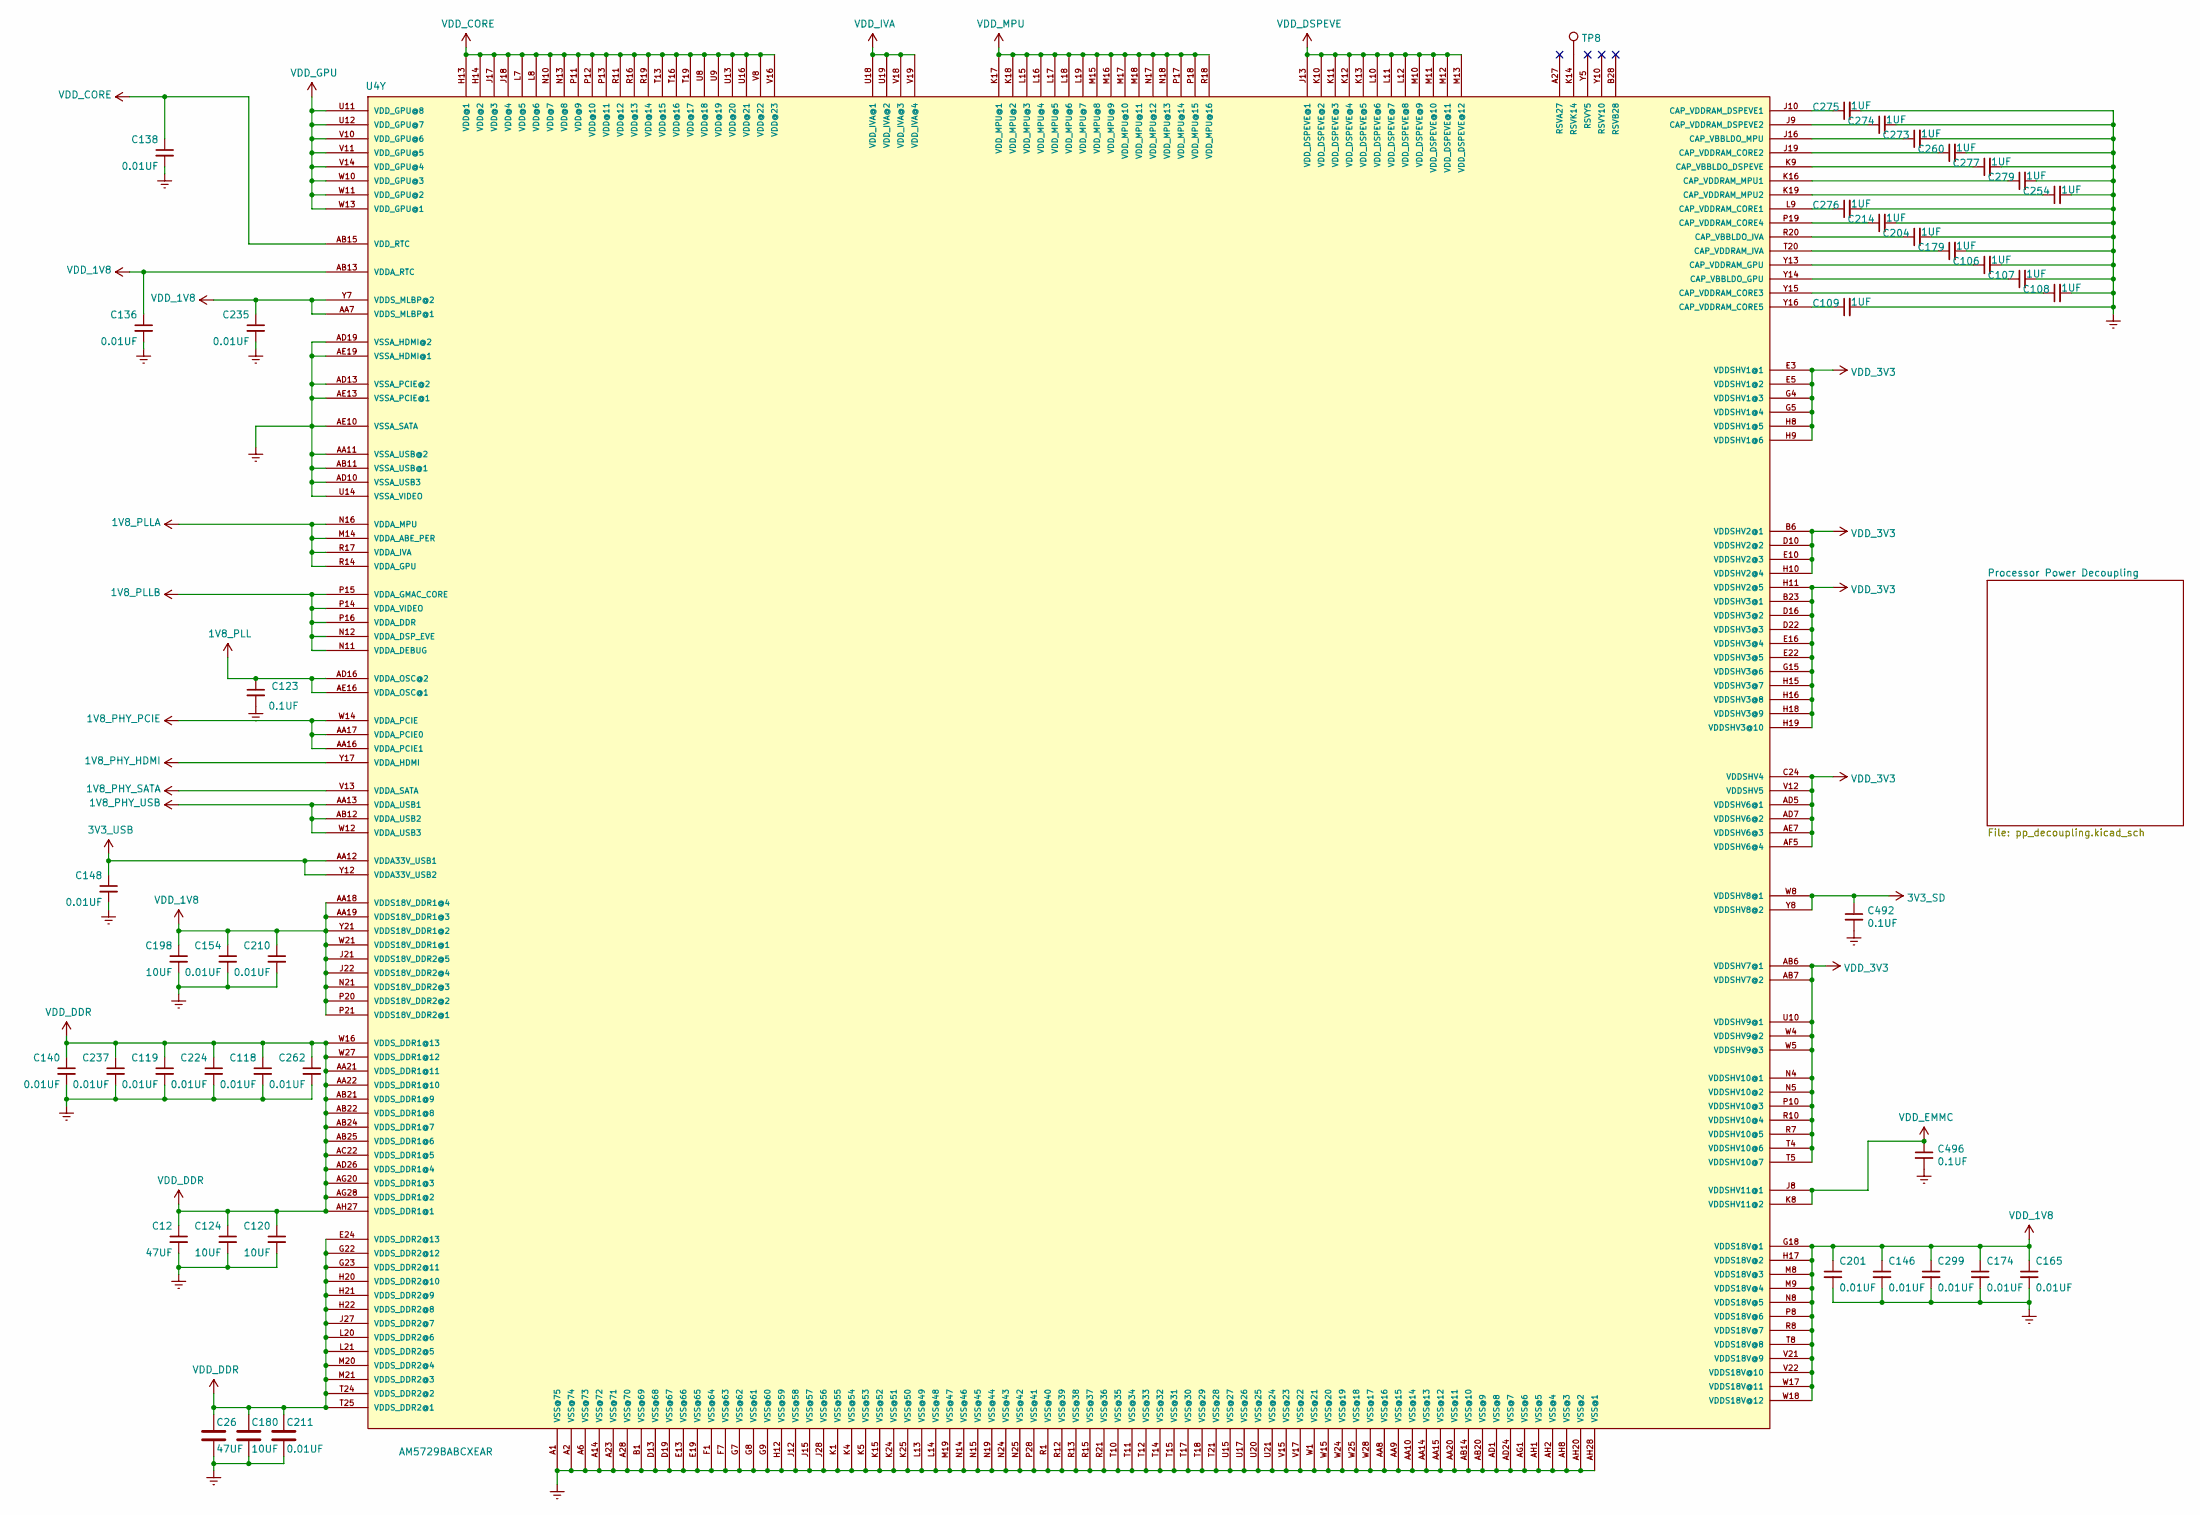
[picture p136: schematic proc_power.kicad_sch]

Parts:
C12, C26: 47UF; C0805; Rating 6.3V,X5R; Manufacturer P/N GRM21BR60J476ME15L
C106, C107, C108, C109, C179, C204, C214, C254, C260, C273, C274, C275, C276, C277, C279: 1UF; C0402; Rating 10V,X5R; Manufacturer P/N GRM155R61A105KE15D
C118, C119, C136, C138, C140, C146, C148, C154, C165, C174, C201, C210, C211, C224, C235, C237, C262, C299: 0.01UF; C0402; Rating X7R,16V; Manufacturer P/N GRM155R71C103KA01D
C120, C124, C180, C198: 10UF; C0603; Rating 10V,X5R; Manufacturer P/N GRM188R61A106KE69D
C123, C492, C496: 0.1UF; C0402; Rating 16V,X7R; Manufacturer P/N GRM155R71C104KA88D
TP8: NI; TP30
U4: AM5729BABCXEAR; BGA760C80P28X28_2300X2300X255; Manufacturer P/N AM5729BABCXEAR

Connections:
1V8_PHY_HDMI: U4.Y17 (VDDA_HDMI)
1V8_PHY_PCIE: U4.AA16 (VDDA_PCIE1), U4.AA17 (VDDA_PCIE0), U4.W14 (VDDA_PCIE)
1V8_PHY_SATA: U4.V13 (VDDA_SATA)
1V8_PHY_USB: U4.AA13 (VDDA_USB1), U4.AB12 (VDDA_USB2), U4.W12 (VDDA_USB3)
1V8_PLL: C123.1, U4.AD16 (VDDA_OSC@2), U4.AE16 (VDDA_OSC@1)
1V8_PLLA: U4.M14 (VDDA_ABE_PER), U4.N16 (VDDA_MPU), U4.R14 (VDDA_GPU), U4.R17 (VDDA_IVA)
1V8_PLLB: U4.N11 (VDDA_DEBUG), U4.N12 (VDDA_DSP_EVE), U4.P14 (VDDA_VIDEO), U4.P15 (VDDA_GMAC_CORE), U4.P16 (VDDA_DDR)
3V3_SD: C492.1, U4.W8 (VDDSHV8@1), U4.Y8 (VDDSHV8@2)
3V3_USB: C148.1, U4.AA12 (VDDA33V_USB1), U4.Y12 (VDDA33V_USB2)
Earth: C12.2, C26.2, C106.2, C107.2, C108.2, C109.2, C118.2, C119.2, C120.2, C123.2, C124.2, C136.2, C138.2, C140.2, C146.2, C148.2, C154.2, C165.2, C174.2, C179.2, C180.2, C198.2, C201.2, C204.2, C210.2, C211.2, C214.2, C224.2, C235.2, C237.2, C254.2, C260.2, C262.2, C273.2, C274.2, C275.2, C276.2, C277.2, C279.2, C299.2, C492.2, C496.2, U4.A1 (VSS@75), U4.A2 (VSS@74), U4.A6 (VSS@73), U4.A14 (VSS@72), U4.A23 (VSS@71), U4.A28 (VSS@70), U4.AA8 (VSS@16), U4.AA9 (VSS@15), U4.AA10 (VSS@14), U4.AA11 (VSSA_USB@2), U4.AA14 (VSS@13), U4.AA15 (VSS@12), U4.AA20 (VSS@11), U4.AB11 (VSSA_USB@1), U4.AB14 (VSS@10), U4.AB20 (VSS@9), U4.AD1 (VSS@8), U4.AD10 (VSSA_USB3), U4.AD13 (VSSA_PCIE@2), U4.AD19 (VSSA_HDMI@2), U4.AD24 (VSS@7), U4.AE10 (VSSA_SATA), U4.AE13 (VSSA_PCIE@1), U4.AE19 (VSSA_HDMI@1), U4.AG1 (VSS@6), U4.AH1 (VSS@5), U4.AH2 (VSS@4), U4.AH8 (VSS@3), U4.AH20 (VSS@2), U4.AH28 (VSS@1), U4.B1 (VSS@69), U4.D13 (VSS@68), U4.D19 (VSS@67), U4.E13 (VSS@66), U4.E19 (VSS@65), U4.F1 (VSS@64), U4.F7 (VSS@63), U4.G7 (VSS@62), U4.G8 (VSS@61), U4.G9 (VSS@60), U4.H12 (VSS@59), U4.J12 (VSS@58), U4.J15 (VSS@57), U4.J28 (VSS@56), U4.K1 (VSS@55), U4.K4 (VSS@54), U4.K5 (VSS@53), U4.K15 (VSS@52), U4.K24 (VSS@51), U4.K25 (VSS@50), U4.L13 (VSS@49), U4.L14 (VSS@48), U4.M19 (VSS@47), U4.N14 (VSS@46), U4.N15 (VSS@45), U4.N19 (VSS@44), U4.N24 (VSS@43), U4.N25 (VSS@42), U4.P28 (VSS@41), U4.R1 (VSS@40), U4.R12 (VSS@39), U4.R13 (VSS@38), U4.R15 (VSS@37), U4.R21 (VSS@36), U4.T10 (VSS@35), U4.T11 (VSS@34), U4.T12 (VSS@33), U4.T14 (VSS@32), U4.T15 (VSS@31), U4.T17 (VSS@30), U4.T18 (VSS@29), U4.T21 (VSS@28), U4.U14 (VSSA_VIDEO), U4.U15 (VSS@27), U4.U17 (VSS@26), U4.U20 (VSS@25), U4.U21 (VSS@24), U4.V15 (VSS@23), U4.V17 (VSS@22), U4.W1 (VSS@21), U4.W15 (VSS@20), U4.W24 (VSS@19), U4.W25 (VSS@18), U4.W28 (VSS@17)
unnamed: C106.1, U4.Y13 (CAP_VDDRAM_GPU)
unnamed: C107.1, U4.Y14 (CAP_VBBLDO_GPU)
unnamed: C108.1, U4.Y15 (CAP_VDDRAM_CORE3)
unnamed: C109.1, U4.Y16 (CAP_VDDRAM_CORE5)
unnamed: C179.1, U4.T20 (CAP_VDDRAM_IVA)
unnamed: C204.1, U4.R20 (CAP_VBBLDO_IVA)
unnamed: C214.1, U4.P19 (CAP_VDDRAM_CORE4)
unnamed: C254.1, U4.K19 (CAP_VDDRAM_MPU2)
unnamed: C260.1, U4.J19 (CAP_VDDRAM_CORE2)
unnamed: C273.1, U4.J16 (CAP_VBBLDO_MPU)
unnamed: C274.1, U4.J9 (CAP_VDDRAM_DSPEVE2)
unnamed: C275.1, U4.J10 (CAP_VDDRAM_DSPEVE1)
unnamed: C276.1, U4.L9 (CAP_VDDRAM_CORE1)
unnamed: C277.1, U4.K9 (CAP_VBBLDO_DSPEVE)
unnamed: C279.1, U4.K16 (CAP_VDDRAM_MPU1)
unnamed: TP8.1, U4.K14 (RSVK14)
VDD_1V8: C136.1, C146.1, C154.1, C165.1, C174.1, C198.1, C201.1, C210.1, C235.1, C299.1, U4.AA7 (VDDS_MLBP@1), U4.AA18 (VDDS18V_DDR1@4), U4.AA19 (VDDS18V_DDR1@3), U4.AB13 (VDDA_RTC), U4.G18 (VDDS18V@1), U4.H17 (VDDS18V@2), U4.J21 (VDDS18V_DDR2@5), U4.J22 (VDDS18V_DDR2@4), U4.M8 (VDDS18V@3), U4.M9 (VDDS18V@4), U4.N8 (VDDS18V@5), U4.N21 (VDDS18V_DDR2@3), U4.P8 (VDDS18V@6), U4.P20 (VDDS18V_DDR2@2), U4.P21 (VDDS18V_DDR2@1), U4.R8 (VDDS18V@7), U4.T8 (VDDS18V@8), U4.V21 (VDDS18V@9), U4.V22 (VDDS18V@10), U4.W17 (VDDS18V@11), U4.W18 (VDDS18V@12), U4.W21 (VDDS18V_DDR1@1), U4.Y7 (VDDS_MLBP@2), U4.Y21 (VDDS18V_DDR1@2)
VDD_3V3: U4.AB6 (VDDSHV7@1), U4.AB7 (VDDSHV7@2), U4.AD5 (VDDSHV6@1), U4.AD7 (VDDSHV6@2), U4.AE7 (VDDSHV6@3), U4.AF5 (VDDSHV6@4), U4.B6 (VDDSHV2@1), U4.B23 (VDDSHV3@1), U4.C24 (VDDSHV4), U4.D10 (VDDSHV2@2), U4.D16 (VDDSHV3@2), U4.D22 (VDDSHV3@3), U4.E3 (VDDSHV1@1), U4.E5 (VDDSHV1@2), U4.E10 (VDDSHV2@3), U4.E16 (VDDSHV3@4), U4.E22 (VDDSHV3@5), U4.G4 (VDDSHV1@3), U4.G5 (VDDSHV1@4), U4.G15 (VDDSHV3@6), U4.H8 (VDDSHV1@5), U4.H9 (VDDSHV1@6), U4.H10 (VDDSHV2@4), U4.H11 (VDDSHV2@5), U4.H15 (VDDSHV3@7), U4.H16 (VDDSHV3@8), U4.H18 (VDDSHV3@9), U4.H19 (VDDSHV3@10), U4.N4 (VDDSHV10@1), U4.N5 (VDDSHV10@2), U4.P10 (VDDSHV10@3), U4.R7 (VDDSHV10@5), U4.R10 (VDDSHV10@4), U4.T4 (VDDSHV10@6), U4.T5 (VDDSHV10@7), U4.U10 (VDDSHV9@1), U4.V12 (VDDSHV5), U4.W4 (VDDSHV9@2), U4.W5 (VDDSHV9@3)
VDD_CORE: C138.1, U4.AB15 (VDD_RTC), U4.H13 (VDD@1), U4.H14 (VDD@2), U4.J17 (VDD@3), U4.J18 (VDD@4), U4.L7 (VDD@5), U4.L8 (VDD@6), U4.N10 (VDD@7), U4.N13 (VDD@8), U4.P11 (VDD@9), U4.P12 (VDD@10), U4.P13 (VDD@11), U4.R11 (VDD@12), U4.R16 (VDD@13), U4.R19 (VDD@14), U4.T13 (VDD@15), U4.T16 (VDD@16), U4.T19 (VDD@17), U4.U8 (VDD@18), U4.U9 (VDD@19), U4.U13 (VDD@20), U4.U16 (VDD@21), U4.V8 (VDD@22), U4.V16 (VDD@23)
VDD_DDR: C12.1, C26.1, C118.1, C119.1, C120.1, C124.1, C140.1, C180.1, C211.1, C224.1, C237.1, C262.1, U4.AA21 (VDDS_DDR1@11), U4.AA22 (VDDS_DDR1@10), U4.AB21 (VDDS_DDR1@9), U4.AB22 (VDDS_DDR1@8), U4.AB24 (VDDS_DDR1@7), U4.AB25 (VDDS_DDR1@6), U4.AC22 (VDDS_DDR1@5), U4.AD26 (VDDS_DDR1@4), U4.AG20 (VDDS_DDR1@3), U4.AG28 (VDDS_DDR1@2), U4.AH27 (VDDS_DDR1@1), U4.E24 (VDDS_DDR2@13), U4.G22 (VDDS_DDR2@12), U4.G23 (VDDS_DDR2@11), U4.H20 (VDDS_DDR2@10), U4.H21 (VDDS_DDR2@9), U4.H22 (VDDS_DDR2@8), U4.J27 (VDDS_DDR2@7), U4.L20 (VDDS_DDR2@6), U4.L21 (VDDS_DDR2@5), U4.M20 (VDDS_DDR2@4), U4.M21 (VDDS_DDR2@3), U4.T24 (VDDS_DDR2@2), U4.T25 (VDDS_DDR2@1), U4.W16 (VDDS_DDR1@13), U4.W27 (VDDS_DDR1@12)
VDD_DSPEVE: U4.J13 (VDD_DSPEVE@1), U4.K10 (VDD_DSPEVE@2), U4.K11 (VDD_DSPEVE@3), U4.K12 (VDD_DSPEVE@4), U4.K13 (VDD_DSPEVE@5), U4.L10 (VDD_DSPEVE@6), U4.L11 (VDD_DSPEVE@7), U4.L12 (VDD_DSPEVE@8), U4.M10 (VDD_DSPEVE@9), U4.M11 (VDD_DSPEVE@10), U4.M12 (VDD_DSPEVE@11), U4.M13 (VDD_DSPEVE@12)
VDD_EMMC: C496.1, U4.J8 (VDDSHV11@1), U4.K8 (VDDSHV11@2)
VDD_GPU: U4.U11 (VDD_GPU@8), U4.U12 (VDD_GPU@7), U4.V10 (VDD_GPU@6), U4.V11 (VDD_GPU@5), U4.V14 (VDD_GPU@4), U4.W10 (VDD_GPU@3), U4.W11 (VDD_GPU@2), U4.W13 (VDD_GPU@1)
VDD_IVA: U4.U18 (VDD_IVA@1), U4.U19 (VDD_IVA@2), U4.V18 (VDD_IVA@3), U4.V19 (VDD_IVA@4)
VDD_MPU: U4.K17 (VDD_MPU@1), U4.K18 (VDD_MPU@2), U4.L15 (VDD_MPU@3), U4.L16 (VDD_MPU@4), U4.L17 (VDD_MPU@5), U4.L18 (VDD_MPU@6), U4.L19 (VDD_MPU@7), U4.M15 (VDD_MPU@8), U4.M16 (VDD_MPU@9), U4.M17 (VDD_MPU@10), U4.M18 (VDD_MPU@11), U4.N17 (VDD_MPU@12), U4.N18 (VDD_MPU@13), U4.P17 (VDD_MPU@14), U4.P18 (VDD_MPU@15), U4.R18 (VDD_MPU@16)
