beagleboard/beaglebone-ai/kicad/beaglebone-ai-rev-a1/usb.kicad_sch

## KiCad design kicad/beaglebone-ai-rev-a1/usb.kicad_sch (2021-06-15)

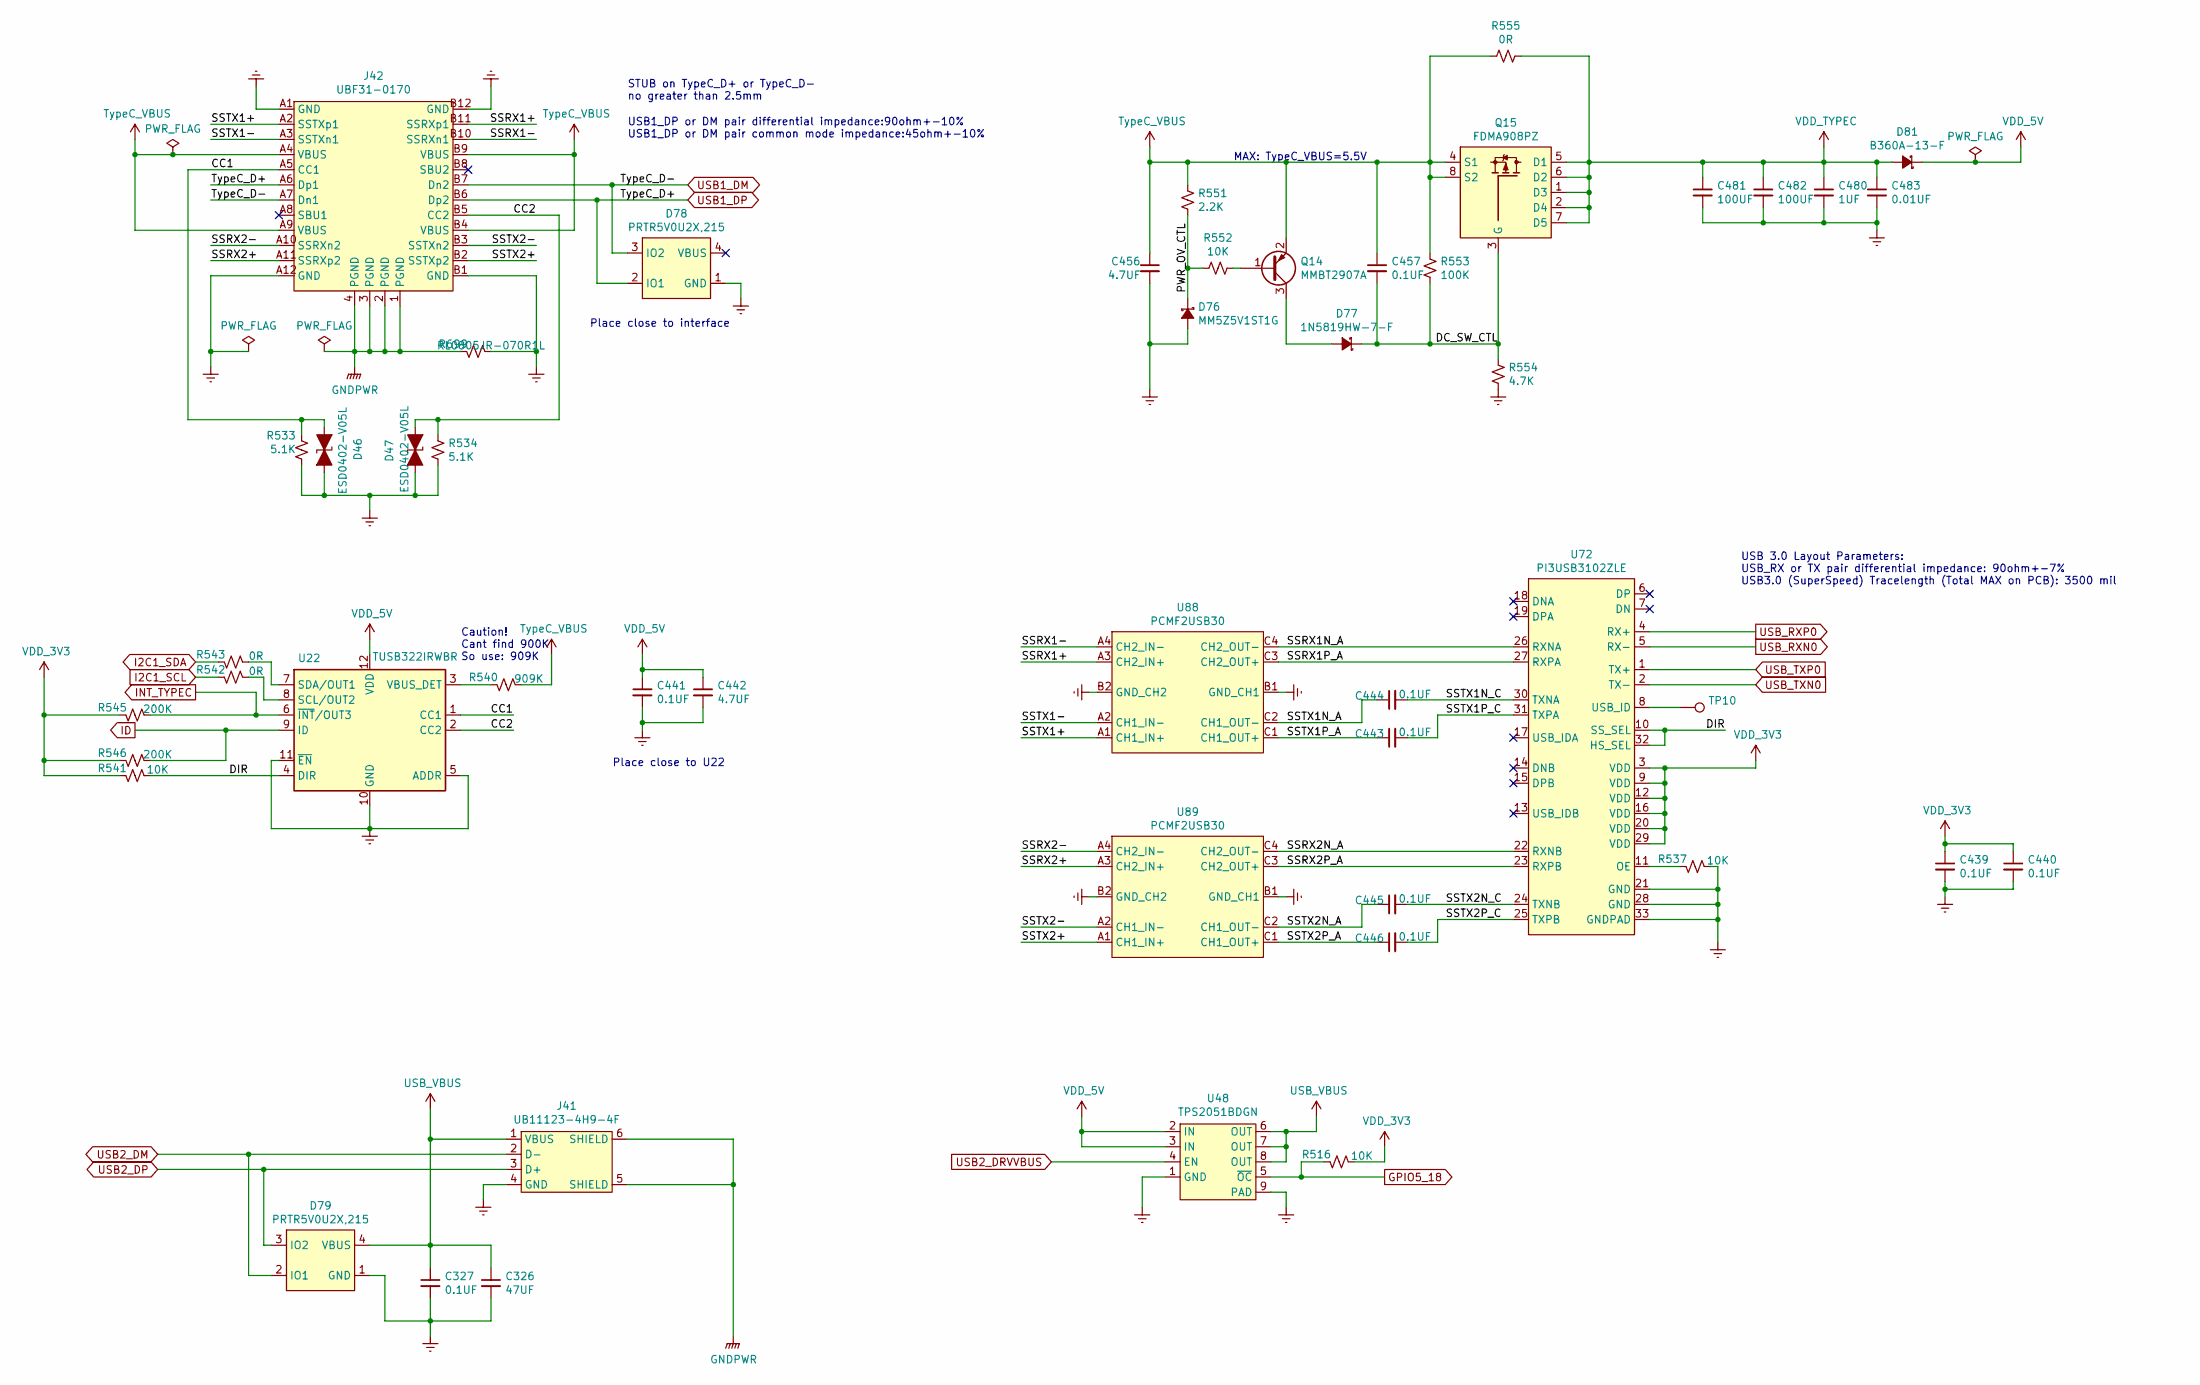
[picture p137: schematic usb.kicad_sch]

Parts:
C326: 47UF; C1210; Rating 10V,X5R; Manufacturer P/N GRM32ER61A476ME20
C327, C439, C440, C441, C443, C444, C445, C446, C457: 0.1UF; C0402; Rating 16V,X7R; Manufacturer P/N GRM155R71C104KA88D
C442, C456: 4.7UF; C0603; Rating 16V,X5R; Manufacturer P/N GRM188R61C475KAAJD
C480: 1UF; C0402; Rating 10V,X5R; Manufacturer P/N GRM155R61A105KE15D
C481, C482: 100UF; C1210; Rating 6.3V,X5R; Manufacturer P/N GRM32ER60J107ME20#
C483: 0.01UF; C0402; Rating X7R,16V; Manufacturer P/N GRM155R71C103KA01D
D46, D47: ESD0402-V05L; D0402; Rating 5V; Manufacturer P/N ESD0402-V05L
D76: MM5Z5V1ST1G; SOD523; Manufacturer P/N MM5Z5V1ST1G
D77: 1N5819HW-7-F; SOD123_A; Manufacturer P/N 1N5819HW-7-F
D78, D79: PRTR5V0U2X,215; SOT143_190P240X115-4N; Manufacturer P/N PRTR5V0U2X,215
D81: B360A-13-F; D_SMA; Manufacturer P/N B360A-13-F
J41: UB11123-4H9-4F; USB_A_SH; Manufacturer P/N Connector,USB A port,4 Position,female,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
J42: UBF31-0170; USB_MTCONN_UBF31-0170; Manufacturer P/N Connector,USB type C port,female,flat i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
Q14: MMBT2907A; SOT-23; Rating 600mA; Manufacturer P/N MMBT2907A-7-F
Q15: FDMA908PZ; DFN6_2FN; Manufacturer P/N FDMA908PZ
R516, R537: 10K; R0402; Rating 1%; Manufacturer P/N RC0402FR-0710KL
R533, R534: 5.1K; R0402; Rating 1%; Manufacturer P/N RC0402FR-075K1L
R540: 909K; R0402; Rating 1%; Manufacturer P/N RC0402FR-07909KL
R541, R552: 10K; R0402; Rating 5%; Manufacturer P/N RC0402JR-0710KL
R542, R543: 0R; R0402; Rating 5%; Manufacturer P/N RC0402JR-070RL
R545, R546: 200K; R0402; Rating 5%; Manufacturer P/N RC0402JR-07200KL
R551: 2.2K; R0402; Rating 5%; Manufacturer P/N RC0402JR-072K2L
R553: 100K; R0402; Rating 5%; Manufacturer P/N RC0402JR-07100KL
R554: 4.7K; R0402; Rating 5%; Manufacturer P/N RC0402JR-074K7L
R555: 0R; R0805; Rating 5%; Manufacturer P/N RC0805JR-070RL
R699: RL0805JR-070R1L; R0805; Rating 5%; Manufacturer P/N RL0805JR-070R1L
TP10: NI; TP30
U22: TUSB322IRWBR; Texas_X2QFN-12_1.6x1.6mm_P0.4mm; Manufacturer P/N TUSB322IRWBR
U48: TPS2051BDGN; SOP8_1FH; Manufacturer P/N TPS2051BDGN
U72: PI3USB3102ZLE; QFN40P300X600X80-33N; Manufacturer P/N PI3USB3102ZLE
U88, U89: PCMF2USB30; WLCSP10C40P3X4_117X157X60N; Manufacturer P/N PCMF2USB30Z

Connections:
CC1: D46.2 (A2), J42.A5 (CC1), R533.1, U22.1 (CC1)
CC2: D47.2 (A2), J42.B5 (CC2), R534.1, U22.2 (CC2)
DC_SW_CTL: C457.2, D77.2 (K), Q15.3 (G), R553.2, R554.1
DIR: R541.2, U22.4 (DIR), U72.10 (SS_SEL), U72.32 (HS_SEL)
Earth: C326.2, C327.2, C439.2, C440.2, C441.2, C442.2, C456.2, C480.2, C481.2, C482.2, C483.2, D46.1 (A1), D47.1 (A1), D76.1 (A), D78.1 (GND), D79.1 (GND), J41.4 (GND), J42.A1 (GND), J42.A12 (GND), J42.B1 (GND), J42.B12 (GND), R533.2, R534.2, R537.2, R554.2, R699.2, U22.5 (ADDR), U22.10 (GND), U22.11 (~EN), U48.1 (GND), U48.9 (PAD), U72.21 (GND), U72.28 (GND), U72.33 (GNDPAD), U88.B1 (GND_CH1), U88.B2 (GND_CH2), U89.B1 (GND_CH1), U89.B2 (GND_CH2)
GNDPWR: J41.5 (SHIELD), J41.6 (SHIELD), J42.1 (PGND), J42.2 (PGND), J42.3 (PGND), J42.4 (PGND), R699.1
GPIO5_18: R516.1, U48.5 (~OC)
I2C1_SCL: R542.1
I2C1_SDA: R543.1
ID: R546.2, U22.9 (ID)
INT_TYPEC: R545.2, U22.6 (~INT~/OUT3)
unnamed: D77.1 (A), Q14.3 (C)
unnamed: Q14.1 (B), R552.2
unnamed: R537.1, U72.11 (OE)
unnamed: R540.1, U22.3 (VBUS_DET)
unnamed: R542.2, U22.8 (SCL/OUT2)
unnamed: R543.2, U22.7 (SDA/OUT1)
unnamed: TP10.1, U72.8 (USB_ID)
PWR_OV_CTL: D76.2 (K), R551.2, R552.1
SSRX1+: J42.B11 (SSRXp1), U88.A3 (CH2_IN+)
SSRX1-: J42.B10 (SSRXn1), U88.A4 (CH2_IN-)
SSRX1N_A: U72.26 (RXNA), U88.C4 (CH2_OUT-)
SSRX1P_A: U72.27 (RXPA), U88.C3 (CH2_OUT+)
SSRX2+: J42.A11 (SSRXp2), U89.A3 (CH2_IN+)
SSRX2-: J42.A10 (SSRXn2), U89.A4 (CH2_IN-)
SSRX2N_A: U72.22 (RXNB), U89.C4 (CH2_OUT-)
SSRX2P_A: U72.23 (RXPB), U89.C3 (CH2_OUT+)
SSTX1+: J42.A2 (SSTXp1), U88.A1 (CH1_IN+)
SSTX1-: J42.A3 (SSTXn1), U88.A2 (CH1_IN-)
SSTX1N_A: C444.1, U88.C2 (CH1_OUT-)
SSTX1N_C: C444.2, U72.30 (TXNA)
SSTX1P_A: C443.1, U88.C1 (CH1_OUT+)
SSTX1P_C: C443.2, U72.31 (TXPA)
SSTX2+: J42.B2 (SSTXp2), U89.A1 (CH1_IN+)
SSTX2-: J42.B3 (SSTXn2), U89.A2 (CH1_IN-)
SSTX2N_A: C445.1, U89.C2 (CH1_OUT-)
SSTX2N_C: C445.2, U72.24 (TXNB)
SSTX2P_A: C446.1, U89.C1 (CH1_OUT+)
SSTX2P_C: C446.2, U72.25 (TXPB)
TypeC_VBUS: C456.1, C457.1, J42.A4 (VBUS), J42.A9 (VBUS), J42.B4 (VBUS), J42.B9 (VBUS), Q14.2 (E), Q15.4 (S1), Q15.8 (S2), R540.2, R551.1, R553.1, R555.1
USB1_DM: D78.3 (IO2), J42.A7 (Dn1), J42.B7 (Dn2)
USB1_DP: D78.2 (IO1), J42.A6 (Dp1), J42.B6 (Dp2)
USB2_DM: D79.2 (IO1), J41.2 (D-)
USB2_DP: D79.3 (IO2), J41.3 (D+)
USB2_DRVVBUS: U48.4 (EN)
USB_RXN0: U72.5 (RX-)
USB_RXP0: U72.4 (RX+)
USB_TXN0: U72.2 (TX-)
USB_TXP0: U72.1 (TX+)
USB_VBUS: C326.1, C327.1, D79.4 (VBUS), J41.1 (VBUS), U48.6 (OUT), U48.7 (OUT), U48.8 (OUT)
VDD_3V3: C439.1, C440.1, R516.2, R541.1, R545.1, R546.1, U72.3 (VDD), U72.9 (VDD), U72.12 (VDD), U72.16 (VDD), U72.20 (VDD), U72.29 (VDD)
VDD_5V: C441.1, C442.1, D81.2 (K), U22.12 (VDD), U48.2 (IN), U48.3 (IN)
VDD_TYPEC: C480.1, C481.1, C482.1, C483.1, D81.1 (A), Q15.1 (D3), Q15.2 (D4), Q15.5 (D1), Q15.6 (D2), Q15.7 (D5), R555.2

Notes on the sheet:
Caution! Cant find 900K So use: 909K
Place close to interface
Place close to U22
STUB on TypeC_D+ or TypeC_D- no greater than 2.5mm
USB1_DP or DM pair differential impedance:90ohm+-10% USB1_DP or DM pair common mode impedance:45ohm+-10%
MAX: TypeC_VBUS=5.5V
USB 3.0 Layout Parameters: USB_RX or TX pair differential impedance: 90ohm+-7% USB3.0 (SuperSpeed) Tracelength (Total MAX on PCB): 3500 mil
