beagleboard/beaglebone-ai/kicad/beaglebone-ai-rev-a1/wifi.kicad_sch

## KiCad design kicad/beaglebone-ai-rev-a1/wifi.kicad_sch (2021-06-15)

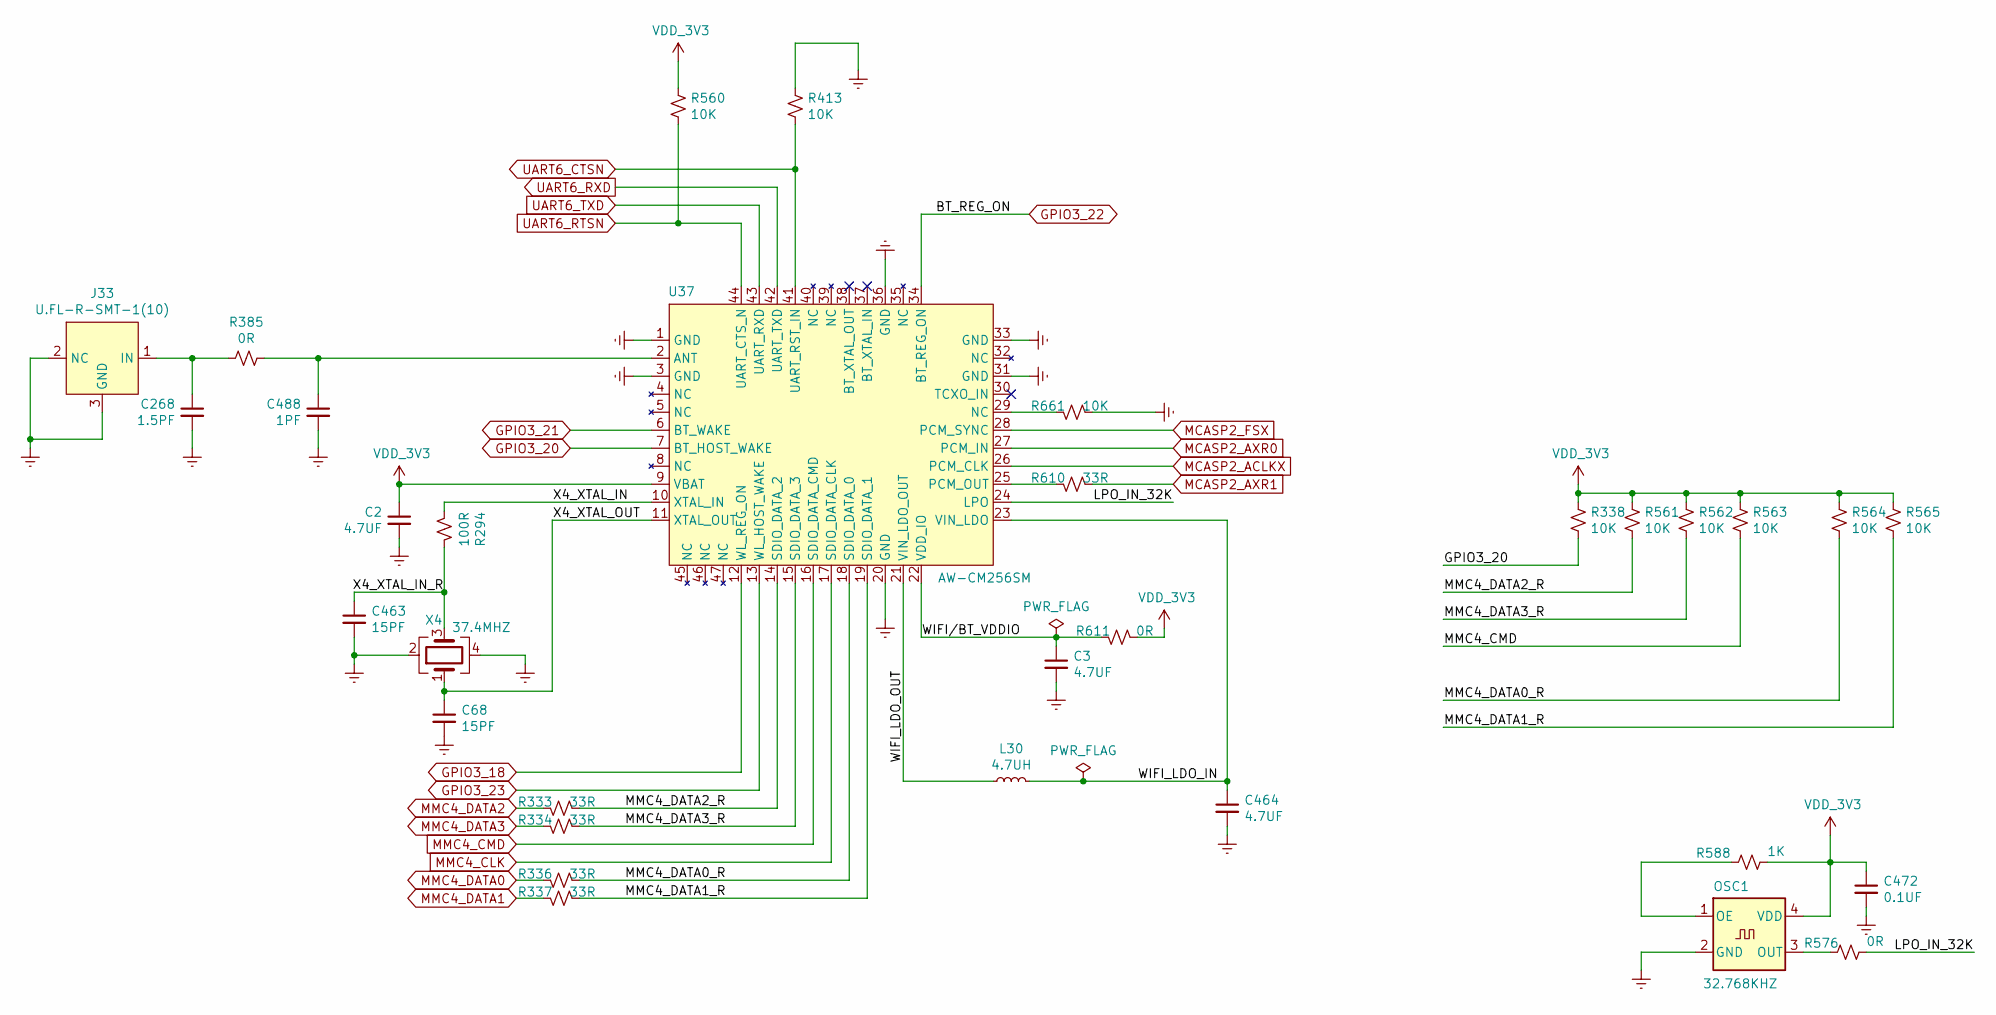
[picture p138: schematic wifi.kicad_sch]

Parts:
C2, C3, C464: 4.7UF; C0603; Rating 10V,X5R; Manufacturer P/N GRM188R61A475KE15D
C68, C463: 15PF; C0402; Rating 50V,C0G; Manufacturer P/N GRM1555C1H150GA01D
C268: 1.5PF; C0402; Rating 50V,C0G; Manufacturer P/N GRM1555C1H1R5CA01D
C472: 0.1UF; C0402; Rating 16V,X7R; Manufacturer P/N GRM155R71C104KA88D
C488: 1PF; C0402; Rating 50V,NP0; Manufacturer P/N GJM1555C1H1R0BB01D
J33: U.FL-R-SMT-1(10); ANT3S_26X26; Manufacturer P/N Connector,Coaxial Connector,U.FL-R-SMT-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
L30: 4.7UH; L25X20; Manufacturer P/N Power Inductor,Magnetic shielded,4.7uH,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
OSC1: 32.768KHZ; X4S25X20; Rating 30PPM; Manufacturer P/N 1651-L3273-BTBQYA
R294: 100R; R0402; Rating 1%; Manufacturer P/N RC0402FR-07100RL
R333, R334, R336, R337, R610: 33R; R0402; Rating 5%; Manufacturer P/N RC0402JR-0733RL
R338, R413, R560, R561, R562, R563, R564, R565: 10K; R0402; Rating 1%; Manufacturer P/N RC0402FR-0710KL
R385, R576, R611: 0R; R0402; Rating 5%; Manufacturer P/N RC0402JR-070RL
R588: 1K; R0402; Rating 5%; Manufacturer P/N RC0402JR-071KL
R661: 10K; R0402; Rating 5%; Manufacturer P/N RC0402JR-0710KL
U37: AW-CM256SM; WLBT90P1200X1200X160-47N; Manufacturer P/N AW-CM256SM
X4: 37.4MHZ; X4S16X12; Manufacturer P/N X37M400000S002

Connections:
Earth: C2.2, C3.2, C68.2, C268.2, C463.2, C464.2, C472.2, C488.2, J33.2 (NC), J33.3 (GND), OSC1.2 (GND), R413.1, R661.2, U37.1 (GND), U37.3 (GND), U37.20 (GND), U37.31 (GND), U37.33 (GND), U37.36 (GND), X4.2, X4.4
GPIO3_18: U37.12 (WL_REG_ON)
GPIO3_20: R338.2, U37.7 (BT_HOST_WAKE)
GPIO3_21: U37.6 (BT_WAKE)
GPIO3_22: U37.34 (BT_REG_ON)
GPIO3_23: U37.13 (WL_HOST_WAKE)
LPO_IN_32K: R576.2, U37.24 (LPO)
MCASP2_ACLKX: U37.26 (PCM_CLK)
MCASP2_AXR0: U37.27 (PCM_IN)
MCASP2_AXR1: R610.2
MCASP2_FSX: U37.28 (PCM_SYNC)
MMC4_CLK: U37.17 (SDIO_DATA_CLK)
MMC4_CMD: R563.2, U37.16 (SDIO_DATA_CMD)
MMC4_DATA0: R336.1
MMC4_DATA0_R: R336.2, R564.2, U37.18 (SDIO_DATA_0)
MMC4_DATA1: R337.1
MMC4_DATA1_R: R337.2, R565.2, U37.19 (SDIO_DATA_1)
MMC4_DATA2: R333.1
MMC4_DATA2_R: R333.2, R561.2, U37.14 (SDIO_DATA_2)
MMC4_DATA3: R334.1
MMC4_DATA3_R: R334.2, R562.2, U37.15 (SDIO_DATA_3)
unnamed: C268.1, J33.1 (IN), R385.1
unnamed: C488.1, R385.2, U37.2 (ANT)
unnamed: OSC1.1 (OE), R588.1
unnamed: OSC1.3 (OUT), R576.1
unnamed: R610.1, U37.25 (PCM_OUT)
unnamed: R661.1, U37.29 (NC)
UART6_CTSN: R413.2, U37.41 (UART_RST_IN)
UART6_RTSN: R560.2, U37.44 (UART_CTS_N)
UART6_RXD: U37.42 (UART_TXD)
UART6_TXD: U37.43 (UART_RXD)
VDD_3V3: C2.1, C472.1, OSC1.4 (VDD), R338.1, R560.1, R561.1, R562.1, R563.1, R564.1, R565.1, R588.2, R611.2, U37.9 (VBAT)
WIFI_LDO_IN: C464.1, L30.2, U37.23 (VIN_LDO)
WIFI_LDO_OUT: L30.1, U37.21 (VIN_LDO_OUT)
WIFI/BT_VDDIO: C3.1, R611.1, U37.22 (VDD_IO)
X4_XTAL_IN: R294.2, U37.10 (XTAL_IN)
X4_XTAL_IN_R: C463.1, R294.1, X4.3
X4_XTAL_OUT: C68.1, U37.11 (XTAL_OUT), X4.1
