beagleboard/beaglebone-ai/kicad/beaglebone-ai-rev-a2/ethernet.kicad_sch

## KiCad design kicad/beaglebone-ai-rev-a2/ethernet.kicad_sch (2021-06-15)

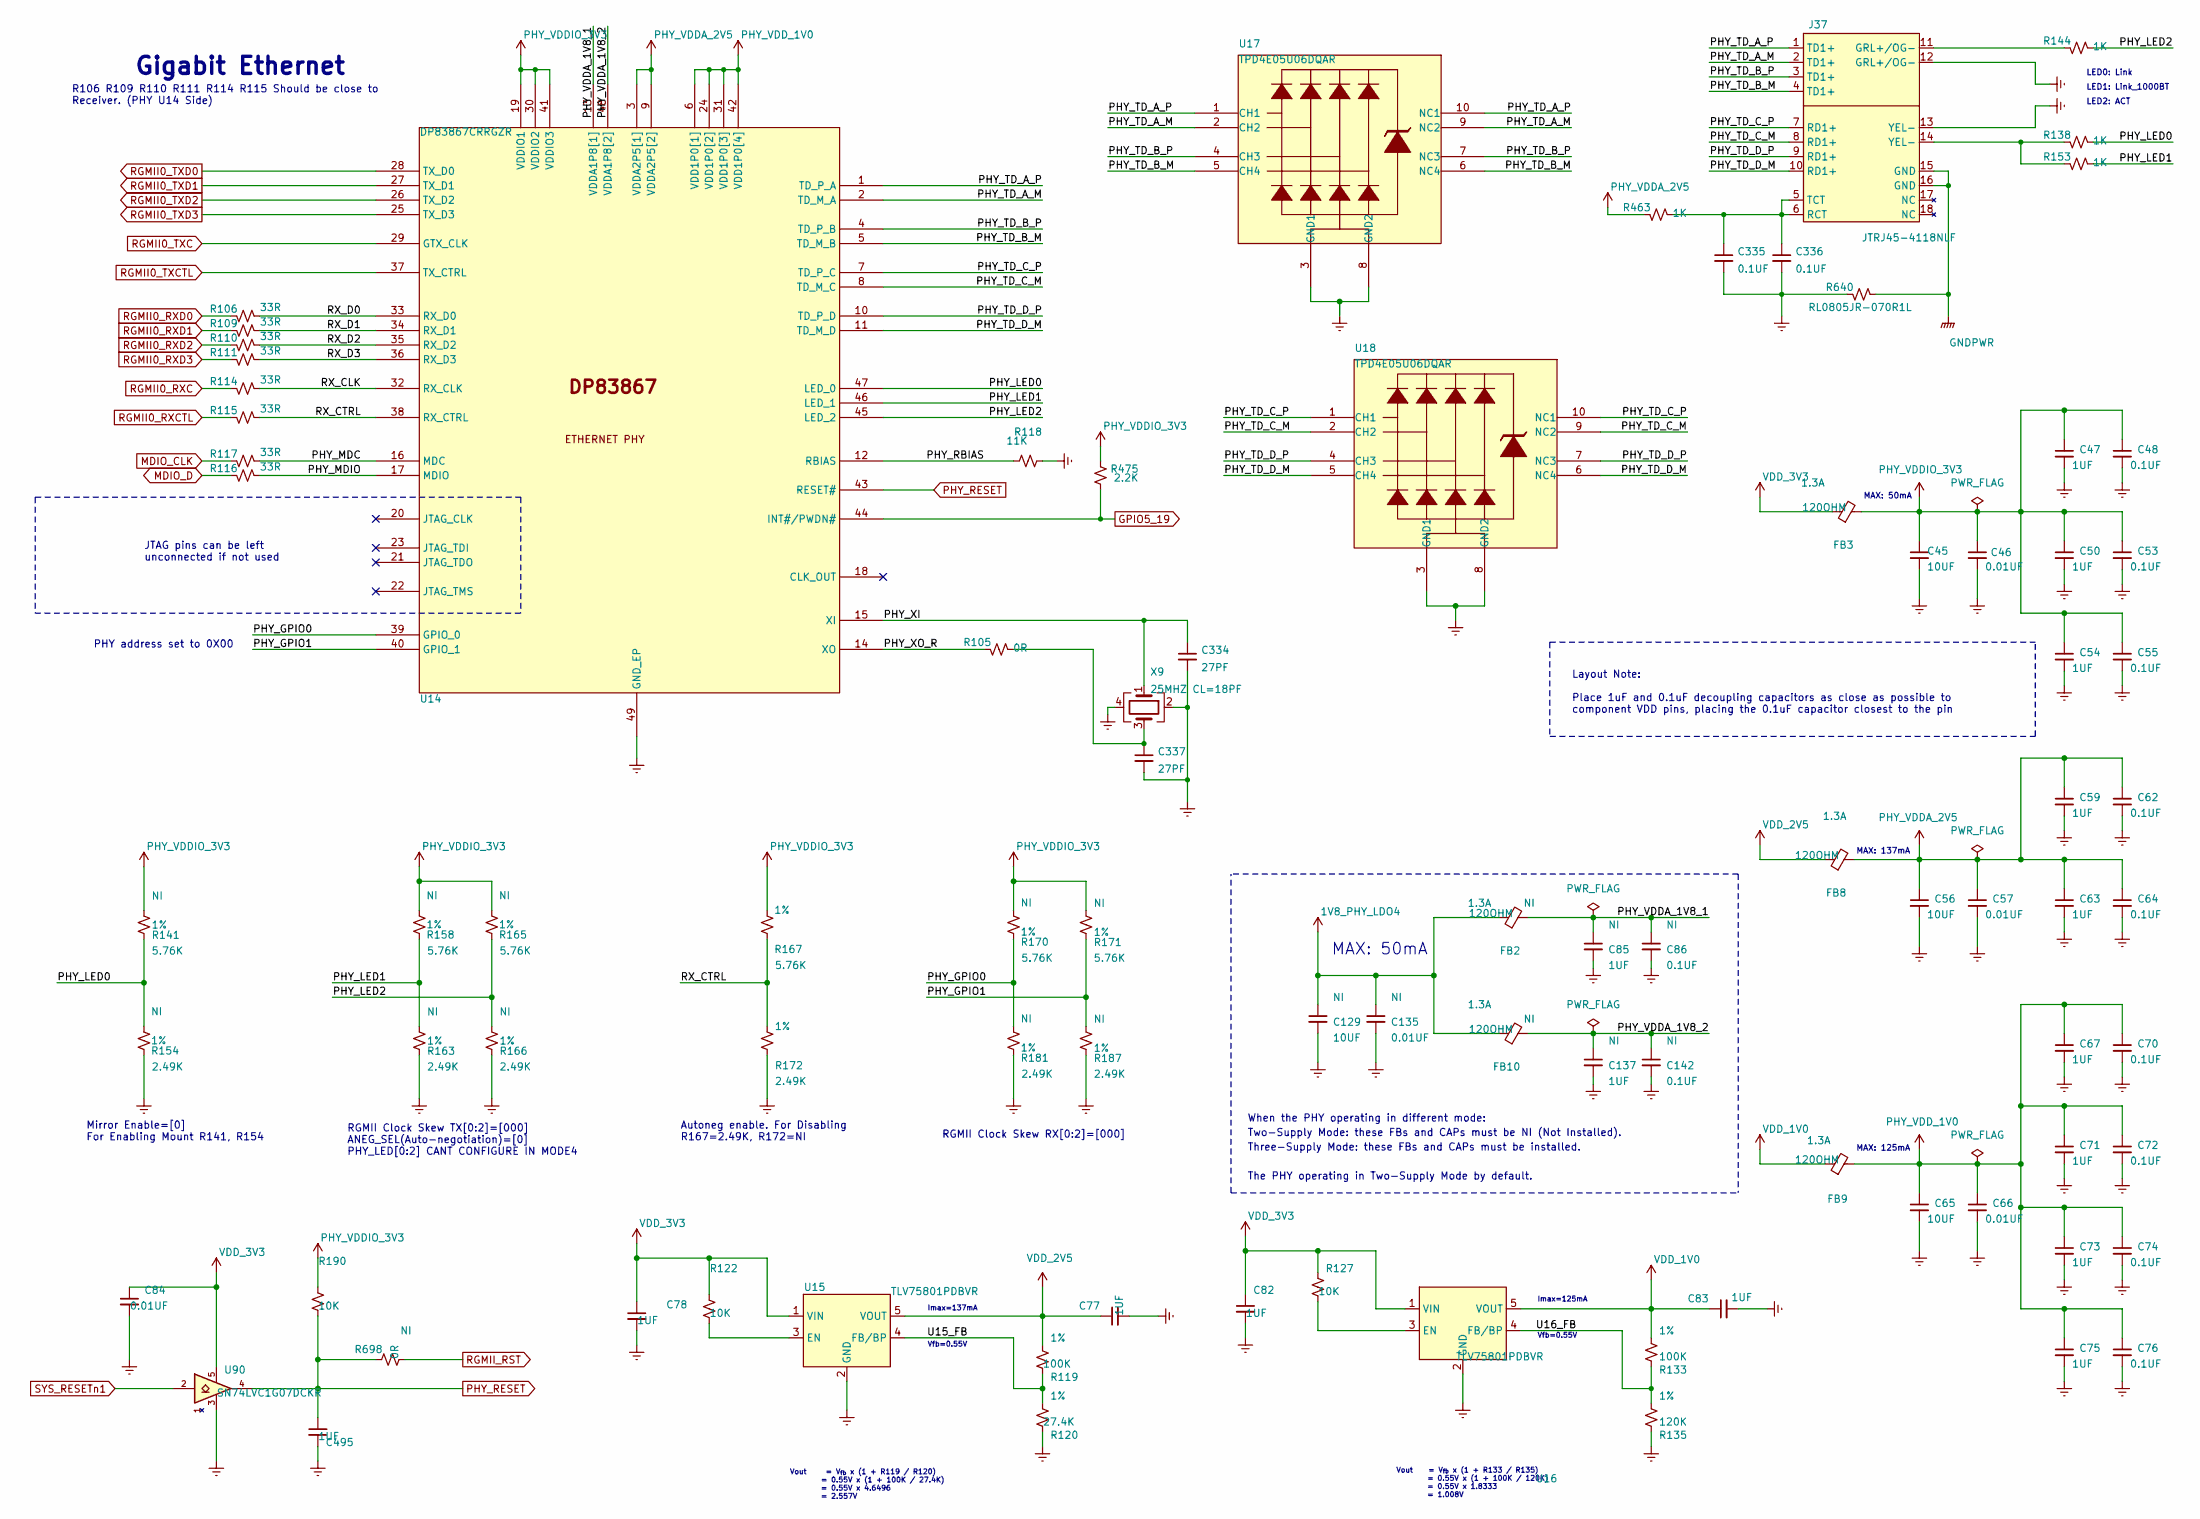
[picture p139: schematic ethernet.kicad_sch]

Parts:
C45, C56, C65, C129: 10UF; C0402; Rating 6.3V,X5R; Part Type Ceramic Capacitor
C46, C57, C66, C84, C135: 0.01UF; C0402; Rating 50V,X7R; Part Type Ceramic Capacitor
C47, C50, C54, C59, C63, C67, C71, C73, C75, C77, C78, C82, C83, C85, C137, C495: 1UF; C0402; Rating 10V,X5R; Part Type Ceramic Capacitor
C48, C53, C55, C62, C64, C70, C72, C74, C76, C86, C142: 0.1UF; C0402; Rating 16V,X7R; Part Type Ceramic Capacitor
C334, C337: 27PF; C0402; Rating 50V,C0G; Manufacturer P/N GRM1555C1H220JA01D
C335, C336: 0.1UF; C0402; Rating 16V,X7R; Manufacturer P/N GRM155R71C104KA88D
FB2, FB3, FB8, FB9, FB10: 120OHM; L0402; Rating 1.3A; Part Type Ferrite Bead
J37: JTRJ45-4118NLF; RJ45_MTCONN_JTRJ45-4118NLF; Manufacturer P/N JTRJ45-4118NLF
R105: 0R; R0402; Rating 5%; Manufacturer P/N RC0402JR-070RL
R106, R109, R110, R111, R114, R115, R116, R117: 33R; R0402; Rating 5%; Manufacturer P/N RC0402JR-0733RL
R118: 11K; R0402; Manufacturer P/N RC0402FR-0711KL
R119, R133: 100K; R0402; Rating 1%; Part Type Thick Film Resistor
R120: 27.4K; R0402; Rating 1%; Part Type Thick Film Resistor
R122, R127, R190: 10K; R0402; Rating 1%; Part Type Thick Film Resistor
R135: 120K; R0402; Rating 1%; Part Type Thick Film Resistor
R138, R144, R153, R463: 1K; R0402; Rating 1%; Manufacturer P/N RC0402FR-071KL
R141, R158, R165, R167, R170, R171: 5.76K; R0402; Rating 1%; Part Type Thick Film Resistor
R154, R163, R166, R172, R181, R187: 2.49K; R0402; Rating 1%; Part Type Thick Film Resistor
R475: 2.2K; R0402; Manufacturer P/N RC0402JR-072K2L
R640: RL0805JR-070R1L; R0805; Rating 5%; Manufacturer P/N RL0805JR-070R1L
R698: 0R; R0402; Rating 5%; Part Type Thick Film Resistor
U14: DP83867CRRGZR; QFN48_0D5_7X7MM; Part Type ETH PHY
U15, U16: TLV75801PDBVR; SOT23_5; Part Type LDO
U17, U18: TPD4E05U06DQAR; USON10_0D5_2D5X1X0D5MM; Part Type ESD
U90: SN74LVC1G07DCKR; SC70_5; Part Type Logic
X9: 25MHZ CL=18PF; OSCCC250X200X60-4N; Rating 20PPM; Manufacturer P/N 5ZAA25000202TFA0Q3

Connections:
1V8_PHY_LDO4: C129.1, C135.1, FB2.1, FB10.1
Earth: C334.2, C335.2, C336.2, C337.2, J37.12 (GRL+/OG-), J37.13 (YEL-), R118.2, R640.1, U14.49 (GND_EP), X9.2, X9.4
GND: C45.2, C46.2, C47.2, C48.2, C50.2, C53.2, C54.2, C55.2, C56.2, C57.2, C59.2, C62.2, C63.2, C64.2, C65.2, C66.2, C67.2, C70.2, C71.2, C72.2, C73.2, C74.2, C75.2, C76.2, C77.2, C78.2, C82.2, C83.2, C84.2, C85.2, C86.2, C129.2, C135.2, C137.2, C142.2, C495.2, R120.2, R135.2, R154.2, R163.2, R166.2, R172.2, R181.2, R187.2, U15.2 (GND), U16.2 (GND), U17.3 (GND1), U17.8 (GND2), U18.3 (GND1), U18.8 (GND2), U90.3 (GND)
GNDPWR: J37.15 (GND), J37.16 (GND), R640.2
GPIO5_19: R475.1, U14.44 (INT#/PWDN#)
MDIO_CLK: R117.1
MDIO_D: R116.1
unnamed: C335.1, C336.1, J37.5 (TCT), J37.6 (RCT), R463.2
unnamed: C337.1, R105.2, X9.3
unnamed: J37.11 (GRL+/OG-), R144.1
unnamed: J37.14 (YEL-), R138.1, R153.1
unnamed: R122.2, U15.3 (EN)
unnamed: R127.2, U16.3 (EN)
PHY_GPIO0: R170.2, R181.1, U14.39 (GPIO_0)
PHY_GPIO1: R171.2, R187.1, U14.40 (GPIO_1)
PHY_LED0: R138.2, R141.2, R154.1, U14.47 (LED_0)
PHY_LED1: R153.2, R158.2, R163.1, U14.46 (LED_1)
PHY_LED2: R144.2, R165.2, R166.1, U14.45 (LED_2)
PHY_MDC: R117.2, U14.16 (MDC)
PHY_MDIO: R116.2, U14.17 (MDIO)
PHY_RBIAS: R118.1, U14.12 (RBIAS)
PHY_RESET: C495.1, R190.2, R698.1, U14.43 (RESET#), U90.4
PHY_TD_A_M: J37.2 (TD1+), U14.2 (TD_M_A), U17.2 (CH2), U17.9 (NC2)
PHY_TD_A_P: J37.1 (TD1+), U14.1 (TD_P_A), U17.1 (CH1), U17.10 (NC1)
PHY_TD_B_M: J37.4 (TD1+), U14.5 (TD_M_B), U17.5 (CH4), U17.6 (NC4)
PHY_TD_B_P: J37.3 (TD1+), U14.4 (TD_P_B), U17.4 (CH3), U17.7 (NC3)
PHY_TD_C_M: J37.8 (RD1+), U14.8 (TD_M_C), U18.2 (CH2), U18.9 (NC2)
PHY_TD_C_P: J37.7 (RD1+), U14.7 (TD_P_C), U18.1 (CH1), U18.10 (NC1)
PHY_TD_D_M: J37.10 (RD1+), U14.11 (TD_M_D), U18.5 (CH4), U18.6 (NC4)
PHY_TD_D_P: J37.9 (RD1+), U14.10 (TD_P_D), U18.4 (CH3), U18.7 (NC3)
PHY_VDDA_1V8_1: C85.1, C86.1, FB2.2, U14.13 (VDDA1P8[1])
PHY_VDDA_1V8_2: C137.1, C142.1, FB10.2, U14.48 (VDDA1P8[2])
PHY_VDDA_2V5: C56.1, C57.1, C59.1, C62.1, C63.1, C64.1, FB8.2, R463.1, U14.3 (VDDA2P5[1]), U14.9 (VDDA2P5[2])
PHY_VDDIO_3V3: C45.1, C46.1, C47.1, C48.1, C50.1, C53.1, C54.1, C55.1, FB3.2, R141.1, R158.1, R165.1, R167.1, R170.1, R171.1, R190.1, R475.2, U14.19 (VDDIO1), U14.30 (VDDIO2), U14.41 (VDDIO3)
PHY_VDD_1V0: C65.1, C66.1, C67.1, C70.1, C71.1, C72.1, C73.1, C74.1, C75.1, C76.1, FB9.2, U14.6 (VDD1P0[1]), U14.24 (VDD1P0[2]), U14.31 (VDD1P0[3]), U14.42 (VDD1P0[4])
PHY_XI: C334.1, U14.15 (XI), X9.1
PHY_XO_R: R105.1, U14.14 (XO)
RGMII0_RXC: R114.1
RGMII0_RXCTL: R115.1
RGMII0_RXD0: R106.1
RGMII0_RXD1: R109.1
RGMII0_RXD2: R110.1
RGMII0_RXD3: R111.1
RGMII0_TXC: U14.29 (GTX_CLK)
RGMII0_TXCTL: U14.37 (TX_CTRL)
RGMII0_TXD0: U14.28 (TX_D0)
RGMII0_TXD1: U14.27 (TX_D1)
RGMII0_TXD2: U14.26 (TX_D2)
RGMII0_TXD3: U14.25 (TX_D3)
RGMII_RST: R698.2
RX_CLK: R114.2, U14.32 (RX_CLK)
RX_CTRL: R115.2, R167.2, R172.1, U14.38 (RX_CTRL)
RX_D0: R106.2, U14.33 (RX_D0)
RX_D1: R109.2, U14.34 (RX_D1)
RX_D2: R110.2, U14.35 (RX_D2)
RX_D3: R111.2, U14.36 (RX_D3)
SYS_RESETn1: U90.2
U15_FB: R119.2, R120.1, U15.4 (FB/BP)
U16_FB: R133.2, R135.1, U16.4 (FB/BP)
VDD_1V0: C83.1, FB9.1, R133.1, U16.5 (VOUT)
VDD_2V5: C77.1, FB8.1, R119.1, U15.5 (VOUT)
VDD_3V3: C78.1, C82.1, C84.1, FB3.1, R122.1, R127.1, U15.1 (VIN), U16.1 (VIN), U90.5 (VCC)

Notes on the sheet:
R106 R109 R110 R111 R114 R115 Should be close to Receiver. (PHY U14 Side)
Mirror Enable=[0] For Enabling Mount R141, R154
PHY address set to 0X00
JTAG pins can be left unconnected if not used
Gigabit Ethernet
RGMII Clock Skew TX[0:2]=[000] ANEG_SEL(Auto-negotiation)=[0] PHY_LED[0:2] CANT CONFIGURE IN MODE4
Autoneg enable. For Disabling R167=2.49K, R172=NI
Vout = V_{fb} x (1 + R119 / R120) = 0.55V x (1 + 100K / 27.4K) = 0.55V x 4.6496 = 2.557V
Imax=137mA
Vfb=0.55V
RGMII Clock Skew RX[0:2]=[000]
When the PHY operating in different mode:
Two-Supply Mode: these FBs and CAPs must be NI (Not Installed).
Three-Supply Mode: these FBs and CAPs must be installed.
The PHY operating in Two-Supply Mode by default.
Vout = V_{fb} x (1 + R133 / R135) = 0.55V x (1 + 100K / 120K) = 0.55V x 1.8333 = 1.008V
MAX: 50mA
Imax=125mA
Layout Note: Place 1uF and 0.1uF decoupling capacitors as close as possible to component VDD pins, placing the 0.1uF capacitor closest to the pin
MAX: 137mA
MAX: 125mA
LED0: Link
LED1: Link_1000BT
LED2: ACT
