beagleboard/beaglebone-ai/kicad/beaglebone-ai-rev-a2/hdmi.kicad_sch

## KiCad design kicad/beaglebone-ai-rev-a2/hdmi.kicad_sch (2021-06-15)

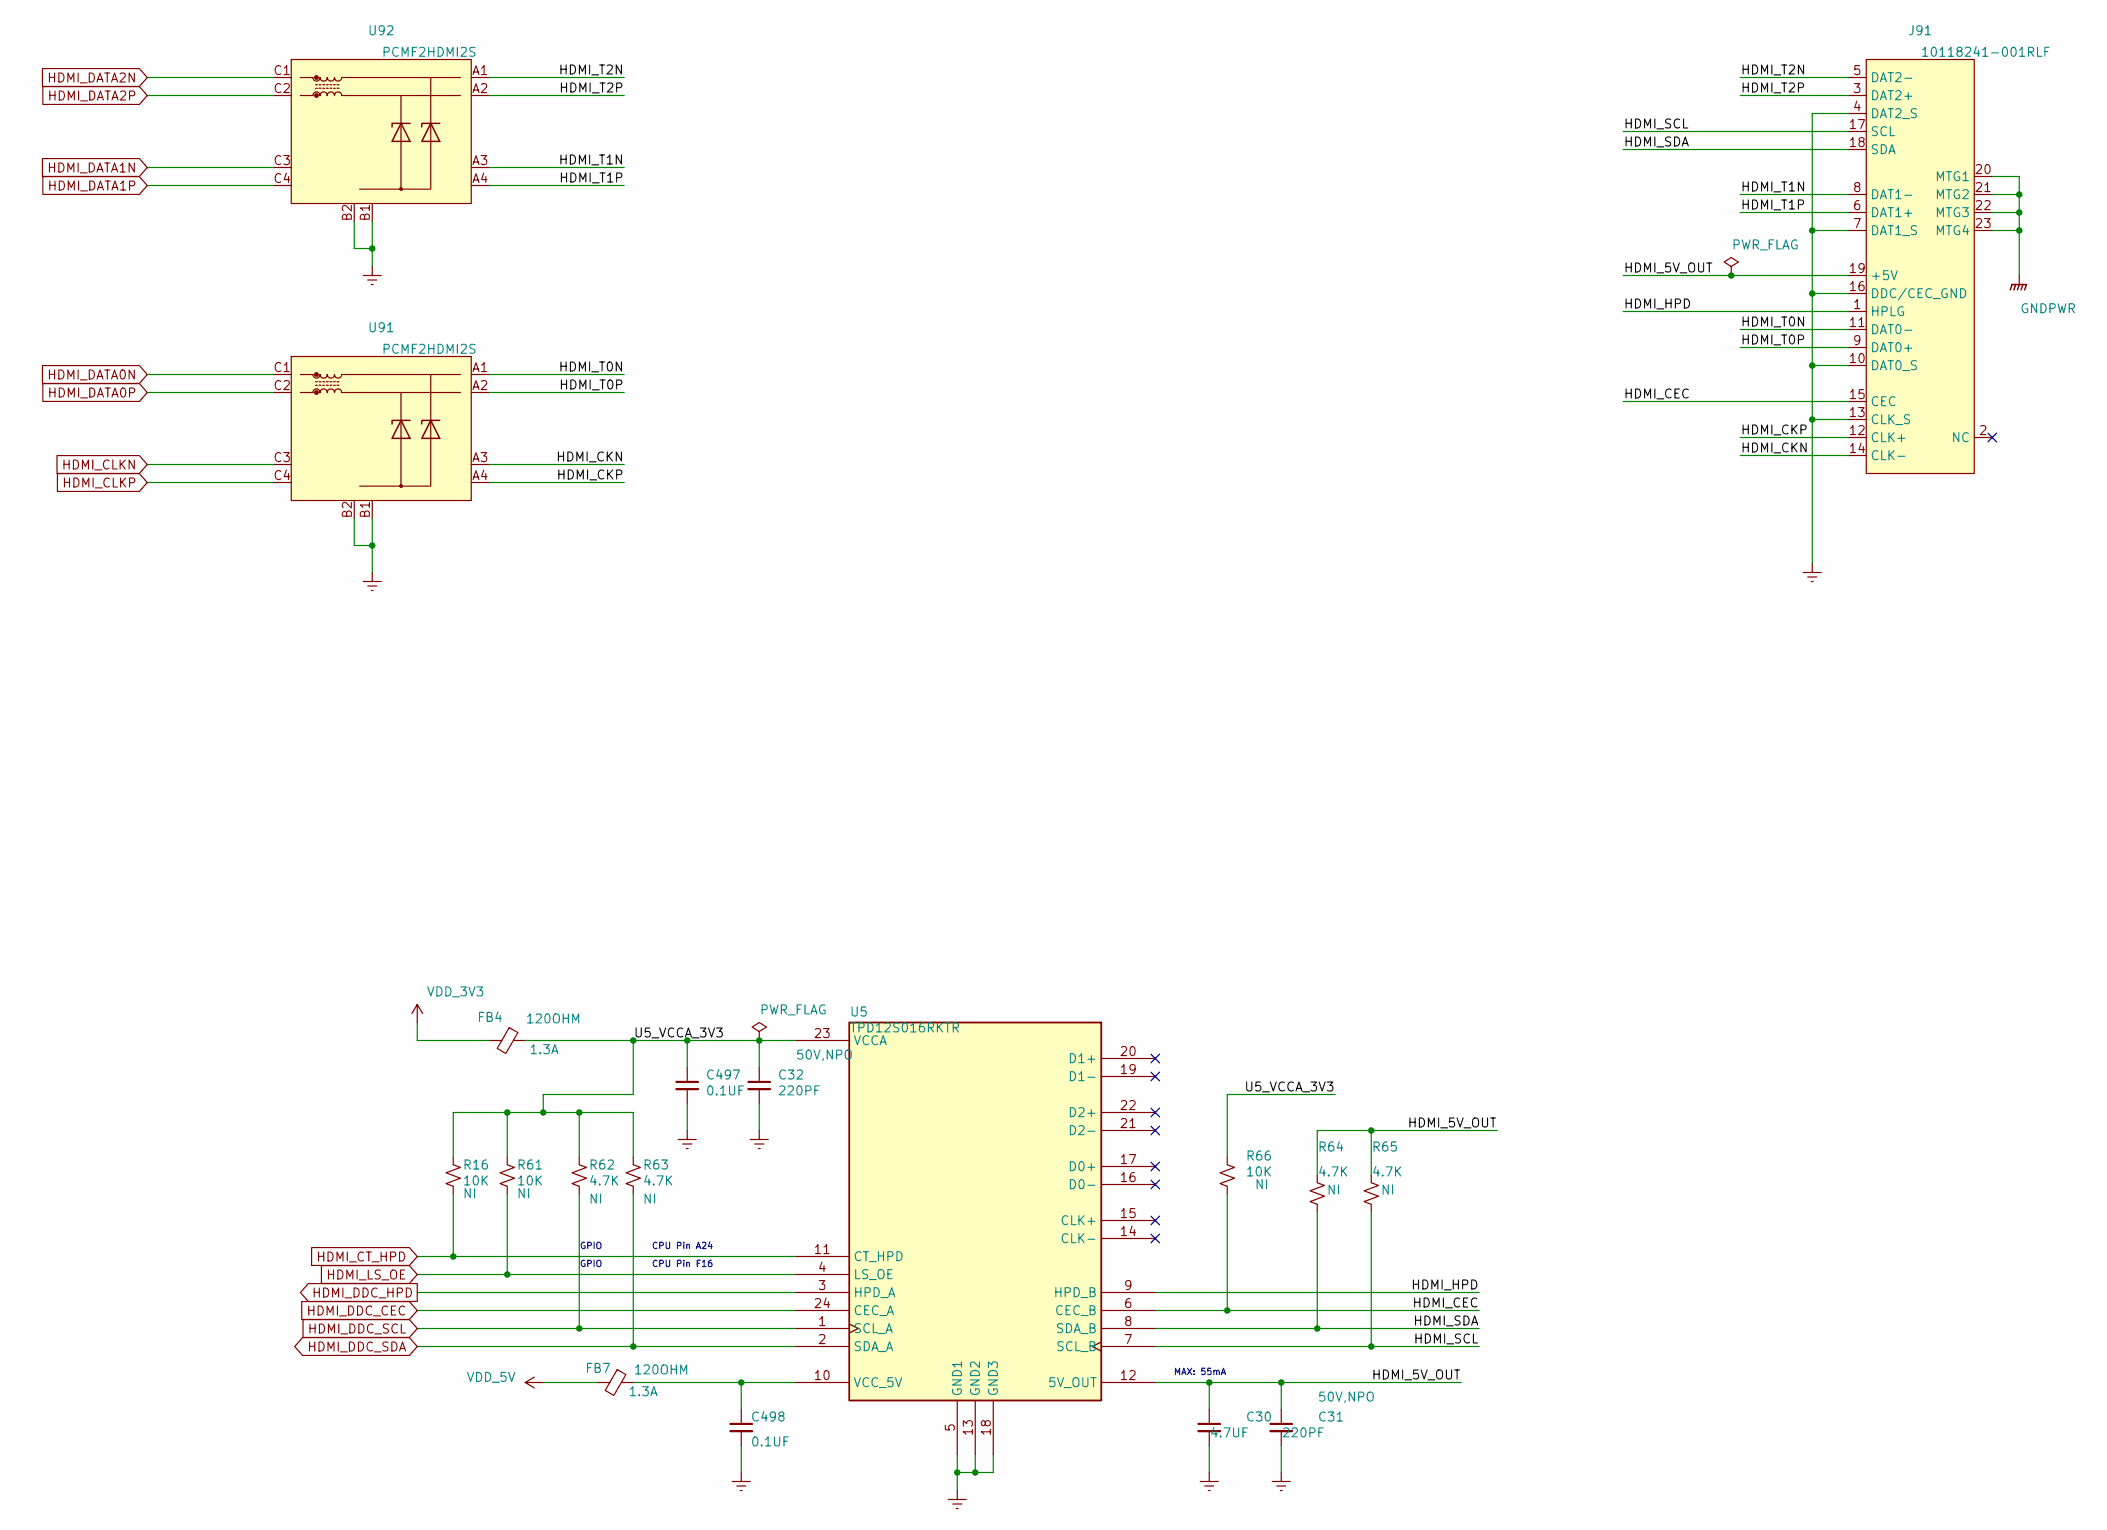
[picture p141: schematic hdmi.kicad_sch]

Parts:
C30: 4.7UF; C0603; Rating 16V,X5R; Part Type Ceramic Capacitor
C31, C32: 220PF; C0402; Rating 50V,NPO; Part Type Ceramic
C497, C498: 0.1UF; C0402; Rating 16V,X7R; Part Type Ceramic Capacitor
FB4, FB7: 120OHM; L0402; Rating 1.3A; Part Type Ferrite Bead
J91: 10118241-001RLF; HDMIS19_4P4; Manufacturer P/N 10118241-001RLF
R16, R61, R66: 10K; R0402; Rating 1%; Part Type Thick Film Resistor
R62, R63, R64, R65: 4.7K; R0402; Rating 1%; Part Type Thick Film Resistor
U5: TPD12S016RKTR; UQFN24_0D4_4X2X0_55MM; Part Type HDMI Companion Chip
U91, U92: PCMF2HDMI2S; WLCSP10C40P3X4_117X157X60N; Manufacturer P/N PCMF2HDMI2S

Connections:
Earth: C30.2, C31.2, C32.2, C497.2, C498.2, J91.4 (DAT2_S), J91.7 (DAT1_S), J91.10 (DAT0_S), J91.13 (CLK_S), J91.16 (DDC/CEC_GND), U5.5 (GND1), U5.13 (GND2), U5.18 (GND3), U91.B1 (GND_CH1), U91.B2 (GND_CH2), U92.B1 (GND_CH1), U92.B2 (GND_CH2)
GNDPWR: J91.20 (MTG1), J91.21 (MTG2), J91.22 (MTG3), J91.23 (MTG4)
HDMI_5V_OUT: C30.1, C31.1, J91.19 (+5V), R64.1, R65.1, U5.12 (5V_OUT)
HDMI_CEC: J91.15 (CEC), R66.2, U5.6 (CEC_B)
HDMI_CKN: J91.14 (CLK-), U91.A3 (CH1_OUT-)
HDMI_CKP: J91.12 (CLK+), U91.A4 (CH1_OUT+)
HDMI_CLKN: U91.C3 (CH1_IN-)
HDMI_CLKP: U91.C4 (CH1_IN+)
HDMI_CT_HPD: R16.2, U5.11 (CT_HPD)
HDMI_DATA0N: U91.C1 (CH2_IN-)
HDMI_DATA0P: U91.C2 (CH2_IN+)
HDMI_DATA1N: U92.C3 (CH1_IN-)
HDMI_DATA1P: U92.C4 (CH1_IN+)
HDMI_DATA2N: U92.C1 (CH2_IN-)
HDMI_DATA2P: U92.C2 (CH2_IN+)
HDMI_DDC_CEC: U5.24 (CEC_A)
HDMI_DDC_HPD: U5.3 (HPD_A)
HDMI_DDC_SCL: R62.2, U5.1 (SCL_A)
HDMI_DDC_SDA: R63.2, U5.2 (SDA_A)
HDMI_HPD: J91.1 (HPLG), U5.9 (HPD_B)
HDMI_LS_OE: R61.2, U5.4 (LS_OE)
HDMI_SCL: J91.17 (SCL), R65.2, U5.7 (SCL_B)
HDMI_SDA: J91.18 (SDA), R64.2, U5.8 (SDA_B)
HDMI_T0N: J91.11 (DAT0-), U91.A1 (CH2_OUT-)
HDMI_T0P: J91.9 (DAT0+), U91.A2 (CH2_OUT+)
HDMI_T1N: J91.8 (DAT1-), U92.A3 (CH1_OUT-)
HDMI_T1P: J91.6 (DAT1+), U92.A4 (CH1_OUT+)
HDMI_T2N: J91.5 (DAT2-), U92.A1 (CH2_OUT-)
HDMI_T2P: J91.3 (DAT2+), U92.A2 (CH2_OUT+)
unnamed: C498.1, FB7.1, U5.10 (VCC_5V)
U5_VCCA_3V3: C32.1, C497.1, FB4.1, R16.1, R61.1, R62.1, R63.1, R66.1, U5.23 (VCCA)
VDD_3V3: FB4.2
VDD_5V: FB7.2

Notes on the sheet:
GPIO
CPU Pin A24
CPU Pin F16
MAX: 55mA
