beagleboard/beaglebone-ai/kicad/beaglebone-ai-rev-a2/usb.kicad_sch

## KiCad design kicad/beaglebone-ai-rev-a2/usb.kicad_sch (2021-06-15)

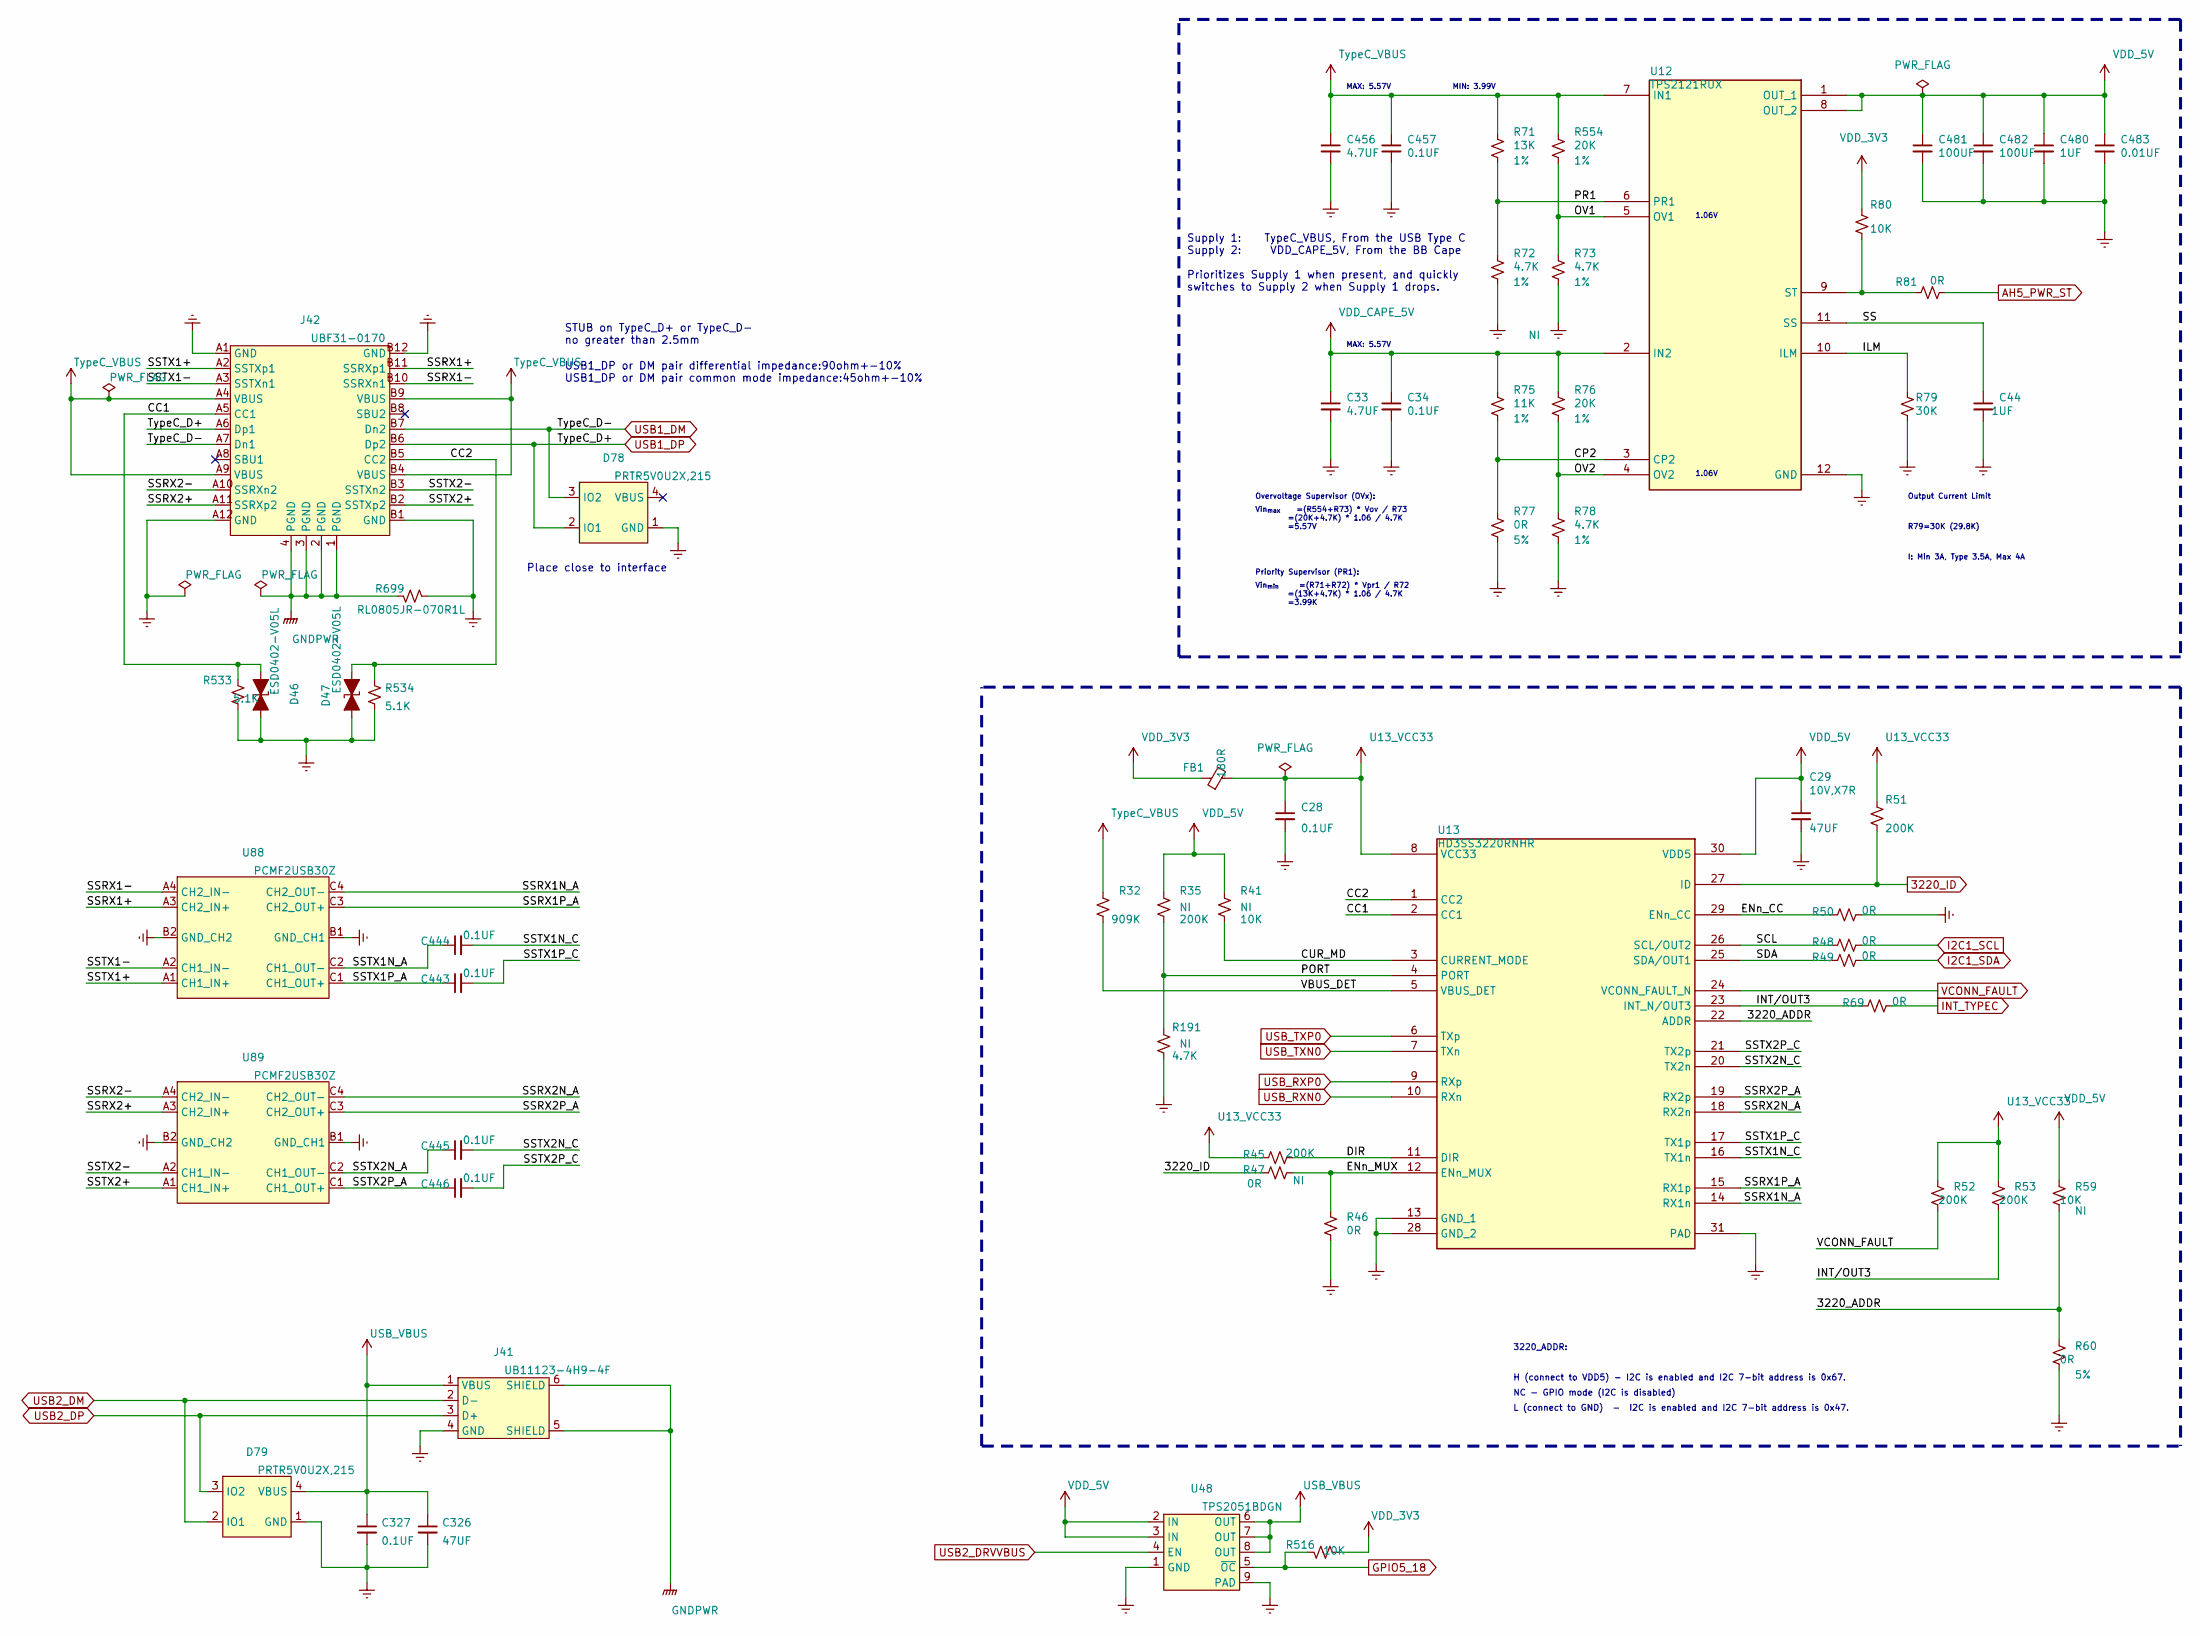
[picture p143: schematic usb.kicad_sch]

Parts:
C28, C34, C457: 0.1UF; C0402; Rating 16V,X7R; Part Type Ceramic Capacitor
C29: 47UF; C1210; Rating 10V,X7R; Part Type Ceramic Capacitor
C33, C456: 4.7UF; C0603; Rating 16V,X5R; Part Type Ceramic Capacitor
C44, C480: 1UF; C0402; Rating 10V,X5R; Part Type Ceramic Capacitor
C326: 47UF; C1210; Rating 10V,X5R; Manufacturer P/N GRM32ER61A476ME20
C327, C443, C444, C445, C446: 0.1UF; C0402; Rating 16V,X7R; Manufacturer P/N GRM155R71C104KA88D
C481, C482: 100UF; C1210; Rating 10V,X5R; Part Type Ceramic Capacitor
C483: 0.01UF; C0402; Rating 50V,X7R; Part Type Ceramic Capacitor
D46, D47: ESD0402-V05L; D0402; Rating 5V; Manufacturer P/N ESD0402-V05L
D78, D79: PRTR5V0U2X,215; SOT143_190P240X115-4N; Manufacturer P/N PRTR5V0U2X,215
FB1: 180R; L0603; Rating 1.5A; Part Type Ferrite Bead
J41: UB11123-4H9-4F; USB_A_SH; Manufacturer P/N UB11123-4H9-4F
J42: UBF31-0170; USB_MTCONN_UBF31-0170; Manufacturer P/N UBF31-0170
R32: 909K; R0402; Rating 1%; Part Type Thick Film Resistor
R35, R45, R51, R52, R53: 200K; R0402; Rating 5%; Part Type Thick Film Resistor
R41, R59, R80: 10K; R0402; Rating 1%; Part Type Thick Film Resistor
R46, R47, R48, R49, R50, R60, R69, R77, R81: 0R; R0402; Rating 5%; Part Type Thick Film Resistor
R71: 13K; R0402; Rating 1%; Part Type Thick Film Resistor
R72, R73, R78, R191: 4.7K; R0402; Rating 1%; Part Type Thick Film Resistor
R75: 11K; R0402; Rating 1%; Part Type Thick Film Resistor
R76, R554: 20K; R0402; Rating 1%; Part Type Thick Film Resistor
R79: 30K; R0402; Rating 1%; Part Type Thick Film Resistor
R516: 10K; R0402; Rating 1%; Manufacturer P/N RC0402FR-0710KL
R533, R534: 5.1K; R0402; Rating 1%; Manufacturer P/N RC0402FR-075K1L
R699: RL0805JR-070R1L; R0805; Rating 5%; Manufacturer P/N RL0805JR-070R1L
U12: TPS2121RUX; VQFN12_0D5_2X2_5X1MM; Part Type Power Mux
U13: HD3SS3220RNHR; WQFN30_0D4_4_5X2_5X0_8MM; Part Type Type-C Controller
U48: TPS2051BDGN; SOP8_1FH; Manufacturer P/N TPS2051BDGN
U88, U89: PCMF2USB30Z; WLCSP10C40P3X4_117X157X60N; Manufacturer P/N PCMF2USB30Z

Connections:
3220_ADDR: R59.2, R60.1, U13.22 (ADDR)
3220_ID: R47.1, R51.2, U13.27 (ID)
AH5_PWR_ST: R81.2
CC1: D46.2 (A2), J42.A5 (CC1), R533.1, U13.2 (CC1)
CC2: D47.2 (A2), J42.B5 (CC2), R534.1, U13.1 (CC2)
CP2: R75.2, R77.1, U12.3 (CP2)
CUR_MD: R41.2, U13.3 (CURRENT_MODE)
DIR: R45.2, U13.11 (DIR)
ENn_CC: R50.1, U13.29 (ENn_CC)
ENn_MUX: R46.1, R47.2, U13.12 (ENn_MUX)
Earth: C28.2, C29.2, C33.2, C34.2, C44.2, C326.2, C327.2, C456.2, C457.2, C480.2, C481.2, C482.2, C483.2, D46.1 (A1), D47.1 (A1), D78.1 (GND), D79.1 (GND), J41.4 (GND), J42.A1 (GND), J42.A12 (GND), J42.B1 (GND), J42.B12 (GND), R46.2, R50.2, R60.2, R72.2, R73.2, R77.2, R78.2, R79.2, R191.2, R533.2, R534.2, R699.2, U12.12 (GND), U13.13 (GND_1), U13.28 (GND_2), U13.31 (PAD), U48.1 (GND), U48.9 (PAD), U88.B1 (GND_CH1), U88.B2 (GND_CH2), U89.B1 (GND_CH1), U89.B2 (GND_CH2)
GNDPWR: J41.5 (SHIELD), J41.6 (SHIELD), J42.1 (PGND), J42.2 (PGND), J42.3 (PGND), J42.4 (PGND), R699.1
GPIO5_18: R516.1, U48.5 (~OC)
I2C1_SCL: R48.2
I2C1_SDA: R49.2
ILM: R79.1, U12.10 (ILM)
INT/OUT3: R53.2, R69.1, U13.23 (INT_N/OUT3)
INT_TYPEC: R69.2
unnamed: R80.2, R81.1, U12.9 (ST)
OV1: R73.1, R554.2, U12.5 (OV1)
OV2: R76.2, R78.1, U12.4 (OV2)
PORT: R35.2, R191.1, U13.4 (PORT)
PR1: R71.2, R72.1, U12.6 (PR1)
SCL: R48.1, U13.26 (SCL/OUT2)
SDA: R49.1, U13.25 (SDA/OUT1)
SS: C44.1, U12.11 (SS)
SSRX1+: J42.B11 (SSRXp1), U88.A3 (CH2_IN+)
SSRX1-: J42.B10 (SSRXn1), U88.A4 (CH2_IN-)
SSRX1N_A: U13.14 (RX1n), U88.C4 (CH2_OUT-)
SSRX1P_A: U13.15 (RX1p), U88.C3 (CH2_OUT+)
SSRX2+: J42.A11 (SSRXp2), U89.A3 (CH2_IN+)
SSRX2-: J42.A10 (SSRXn2), U89.A4 (CH2_IN-)
SSRX2N_A: U13.18 (RX2n), U89.C4 (CH2_OUT-)
SSRX2P_A: U13.19 (RX2p), U89.C3 (CH2_OUT+)
SSTX1+: J42.A2 (SSTXp1), U88.A1 (CH1_IN+)
SSTX1-: J42.A3 (SSTXn1), U88.A2 (CH1_IN-)
SSTX1N_A: C444.1, U88.C2 (CH1_OUT-)
SSTX1N_C: C444.2, U13.16 (TX1n)
SSTX1P_A: C443.1, U88.C1 (CH1_OUT+)
SSTX1P_C: C443.2, U13.17 (TX1p)
SSTX2+: J42.B2 (SSTXp2), U89.A1 (CH1_IN+)
SSTX2-: J42.B3 (SSTXn2), U89.A2 (CH1_IN-)
SSTX2N_A: C445.1, U89.C2 (CH1_OUT-)
SSTX2N_C: C445.2, U13.20 (TX2n)
SSTX2P_A: C446.1, U89.C1 (CH1_OUT+)
SSTX2P_C: C446.2, U13.21 (TX2p)
TypeC_VBUS: C456.1, C457.1, J42.A4 (VBUS), J42.A9 (VBUS), J42.B4 (VBUS), J42.B9 (VBUS), R32.1, R71.1, R554.1, U12.7 (IN1)
U13_VCC33: C28.1, FB1.2, R45.1, R51.1, R52.1, R53.1, U13.8 (VCC33)
USB1_DM: D78.3 (IO2), J42.A7 (Dn1), J42.B7 (Dn2)
USB1_DP: D78.2 (IO1), J42.A6 (Dp1), J42.B6 (Dp2)
USB2_DM: D79.2 (IO1), J41.2 (D-)
USB2_DP: D79.3 (IO2), J41.3 (D+)
USB2_DRVVBUS: U48.4 (EN)
USB_RXN0: U13.10 (RXn)
USB_RXP0: U13.9 (RXp)
USB_TXN0: U13.7 (TXn)
USB_TXP0: U13.6 (TXp)
USB_VBUS: C326.1, C327.1, D79.4 (VBUS), J41.1 (VBUS), U48.6 (OUT), U48.7 (OUT), U48.8 (OUT)
VBUS_DET: R32.2, U13.5 (VBUS_DET)
VCONN_FAULT: R52.2, U13.24 (VCONN_FAULT_N)
VDD_3V3: FB1.1, R80.1, R516.2
VDD_5V: C29.1, C480.1, C481.1, C482.1, C483.1, R35.1, R41.1, R59.1, U12.1 (OUT_1), U12.8 (OUT_2), U13.30 (VDD5), U48.2 (IN), U48.3 (IN)
VDD_CAPE_5V: C33.1, C34.1, R75.1, R76.1, U12.2 (IN2)

Notes on the sheet:
Place close to interface
STUB on TypeC_D+ or TypeC_D- no greater than 2.5mm
USB1_DP or DM pair differential impedance:90ohm+-10% USB1_DP or DM pair common mode impedance:45ohm+-10%
Supply 1: TypeC_VBUS, From the USB Type C Supply 2: VDD_CAPE_5V, From the BB Cape Prioritizes Supply 1 when present, and quickly switches to Supply 2 when Supply 1 drops.
Overvoltage Supervisor (OVx):
Vin_{max} =(R554+R73) * Vov / R73 =(20K+4.7K) * 1.06 / 4.7K =5.57V
Priority Supervisor (PR1):
Vin_{min} =(R71+R72) * Vpr1 / R72 =(13K+4.7K) * 1.06 / 4.7K =3.99K
MAX: 5.57V
MIN: 3.99V
3220_ADDR:
H (connect to VDD5) - I2C is enabled and I2C 7-bit address is 0x67.
NC - GPIO mode (I2C is disabled)
L (connect to GND) - I2C is enabled and I2C 7-bit address is 0x47.
1.06V
Output Current Limit
R79=30K (29.8K)
I: Min 3A, Type 3.5A, Max 4A
